AlessandroCrosby/GRUPO2/TALLERES/TALLERES SEMANA N°7/Link del video.pdf

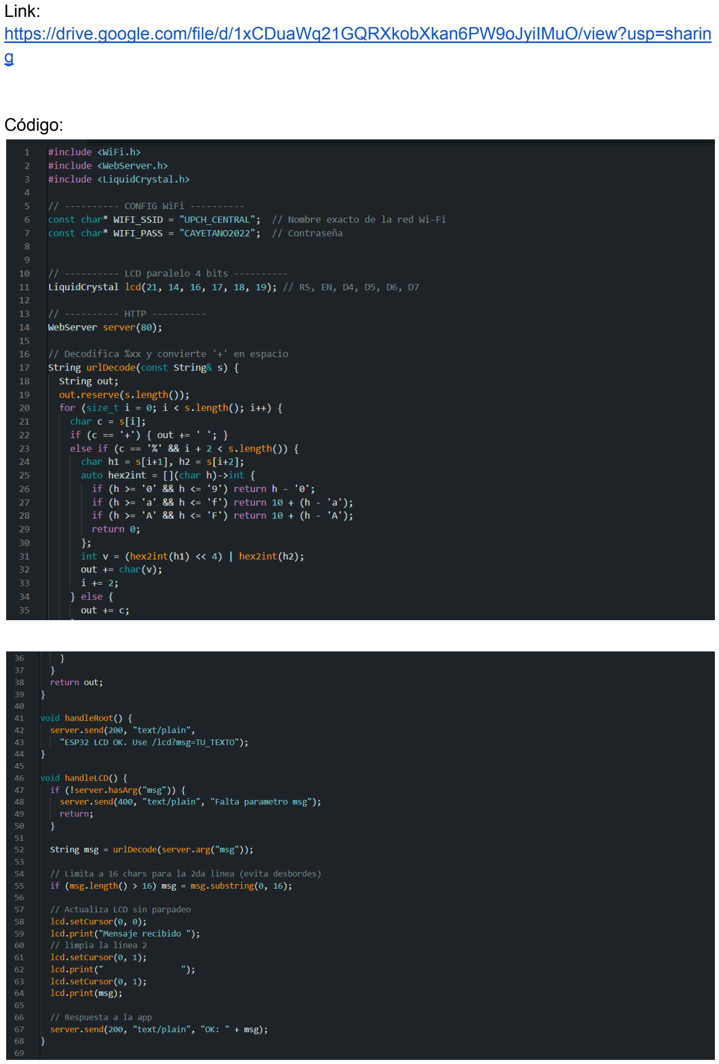
[picture p41: page 1]

Link:
https://drive.google.com/file/d/1xCDuaWq21GQRXkobXkan6PW9oJyiIMuO/view?usp=sharin g (https://drive.google.com/file/d/1xCDuaWq21GQRXkobXkan6PW9oJyiIMuO/view?usp=sharing)

Código:

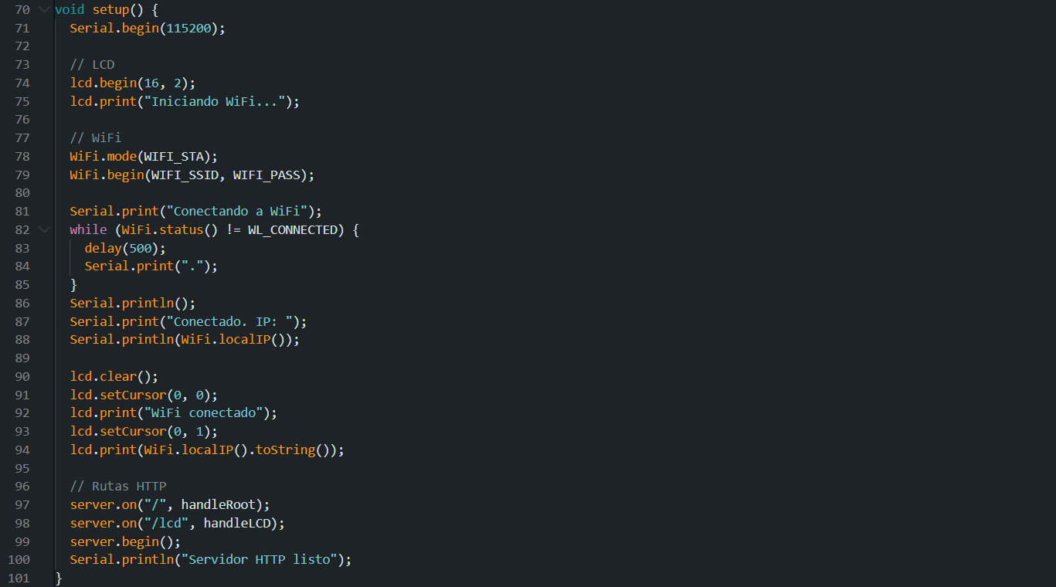
[picture p42: figure]

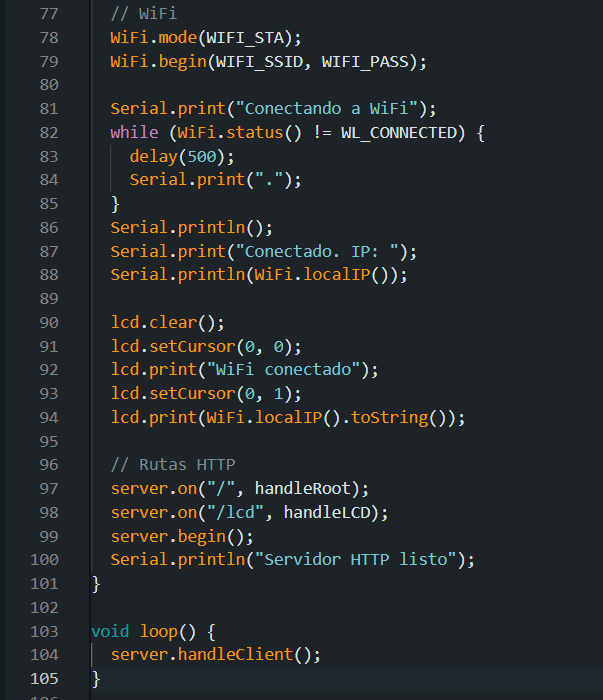
[picture p43: figure]

#include <WiFi.h>

#include <WebServer.h>

#include <LiquidCrystal.h>

// ---------- CONFIG WiFi ----------
const char* WIFI_SSID = "UPCH_CENTRAL"; // Nombre exacto de la red Wi-Fi const char* WIFI_PASS = "CAYETANO2022"; // Contraseña

// ---------- LCD paralelo 4 bits ----------
LiquidCrystal lcd(21, 14, 16, 17, 18, 19); // RS, EN, D4, D5, D6, D7

// ---------- HTTP ----------
WebServer server(80);

// Decodifica %xx y convierte '+' en espacio String urlDecode(const String& s) {
String out;
out.reserve(s.length());
for (size_t i = 0; i < s.length(); i++) { char c = s[i];
if (c == '+') { out += ' '; }
else if (c == '%' && i + 2 < s.length()) { char h1 = s[i+1], h2 = s[i+2];
auto hex2int = [](char h)->int {
if (h >= '0' && h <= '9') return h - '0';
if (h >= 'a' && h <= 'f') return 10 + (h - 'a'); if (h >= 'A' && h <= 'F') return 10 + (h - 'A'); return 0;
};
int v = (hex2int(h1) << 4) | hex2int(h2);
out += char(v);
i += 2;
} else {
out += c;
}
}
return out;
}

void handleRoot() {
server.send(200, "text/plain",
"ESP32 LCD OK. Use /lcd?msg=TU_TEXTO"); }

void handleLCD() {
if (!server.hasArg("msg")) {
server.send(400, "text/plain", "Falta parametro msg"); return;
}

String msg = urlDecode(server.arg("msg"));

// Limita a 16 chars para la 2da linea (evita desbordes) if (msg.length() > 16) msg = msg.substring(0, 16);

// Actualiza LCD sin parpadeo

lcd.setCursor(0, 0);
lcd.print("Mensaje recibido "); // limpia la linea 2
lcd.setCursor(0, 1);
lcd.print(" | ");
lcd.setCursor(0, 1);
lcd.print(msg);

// Respuesta a la app
server.send(200, "text/plain", "OK: " + msg); }

void setup() {
Serial.begin(115200);

// LCD
lcd.begin(16, 2);
lcd.print("Iniciando WiFi...");

// WiFi
WiFi.mode(WIFI_STA);
WiFi.begin(WIFI_SSID, WIFI_PASS);

Serial.print("Conectando a WiFi");
while (WiFi.status() != WL_CONNECTED) { delay(500);
Serial.print(".");
}
Serial.println();
Serial.print("Conectado. IP: "); Serial.println(WiFi.localIP());

lcd.clear();
lcd.setCursor(0, 0);
lcd.print("WiFi conectado"); lcd.setCursor(0, 1);
lcd.print(WiFi.localIP().toString());

// Rutas HTTP
server.on("/", handleRoot); server.on("/lcd", handleLCD); server.begin();
Serial.println("Servidor HTTP listo"); }

void loop() {
server.handleClient();
}
