AlessandroCrosby/GRUPO2/TALLERES/TALLERES SEMANA N°8/TALLER 8.pdf

## EJERCICIO 1:

## Captura del correo

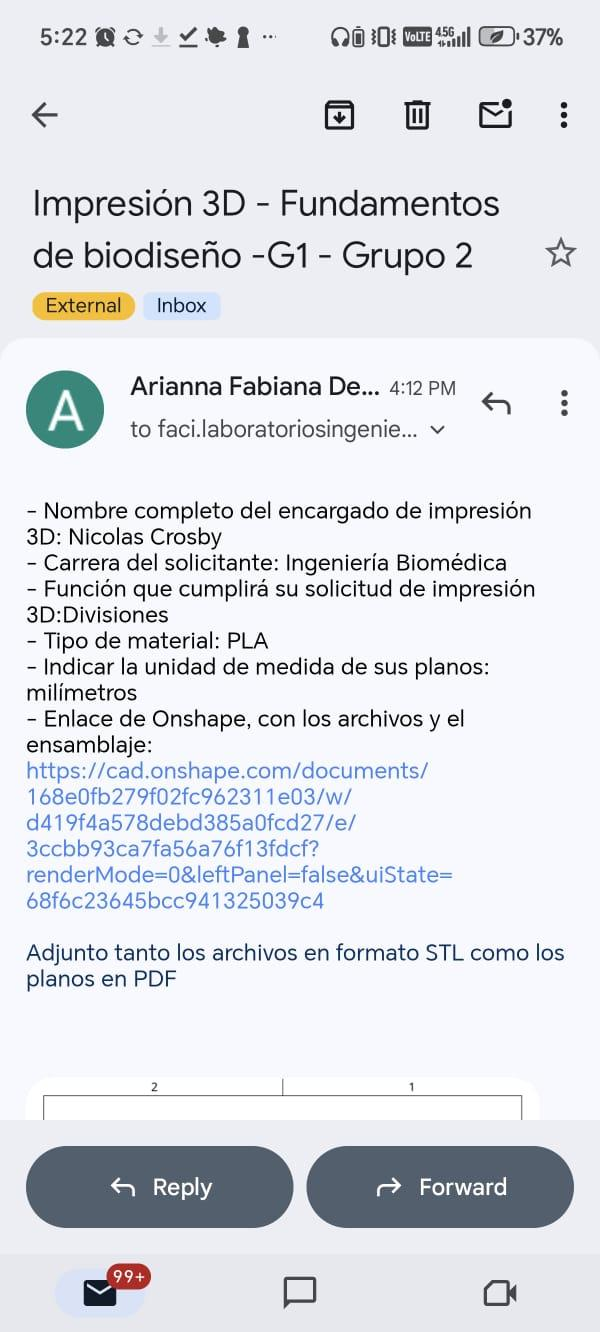
[picture p44: figure]
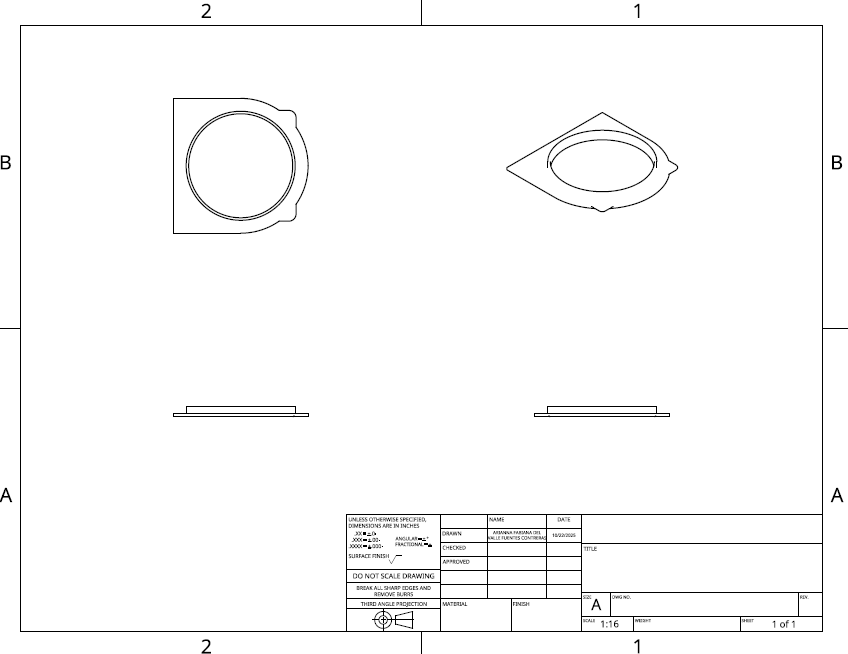
[picture p45: figure]
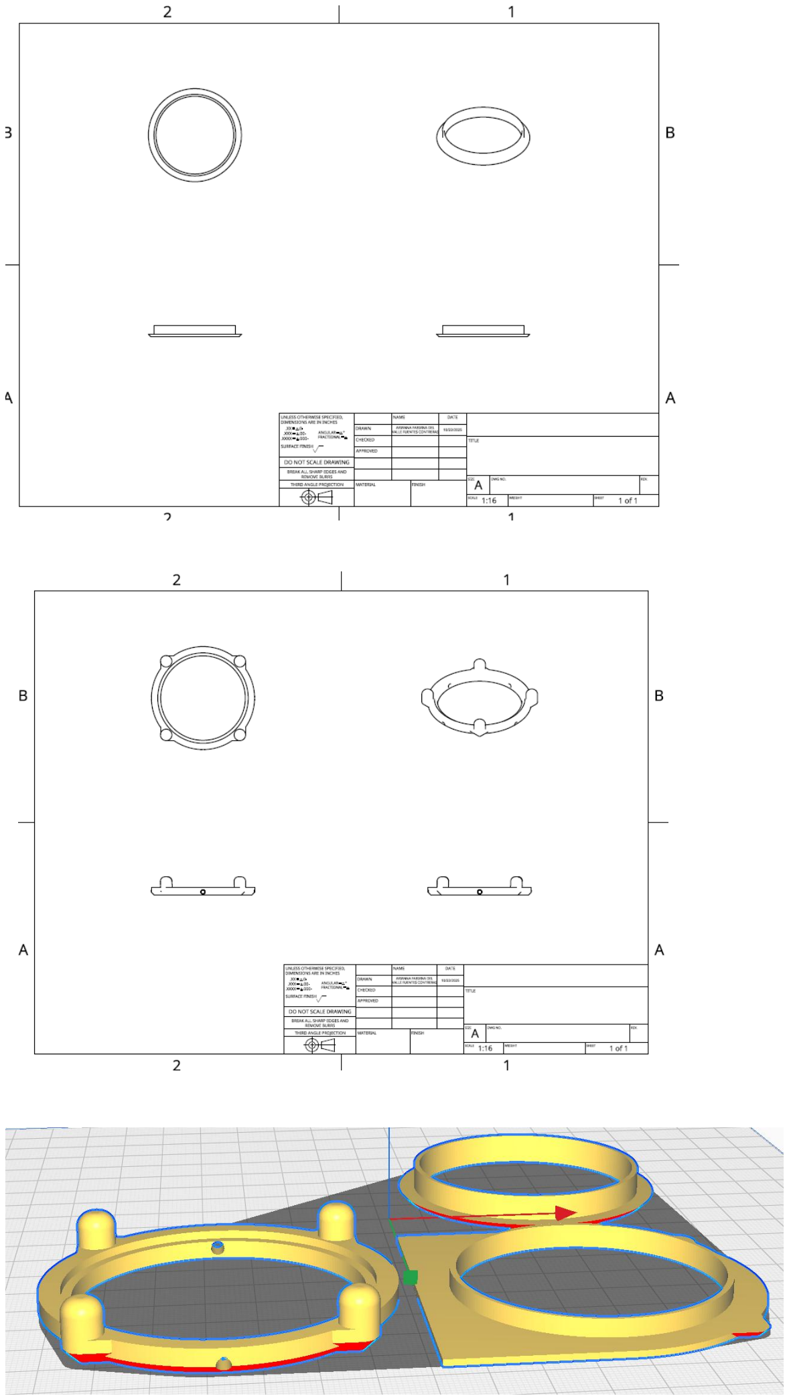
[picture p46: page 2]

## EJERCICIO 2:

## Plano 2.1

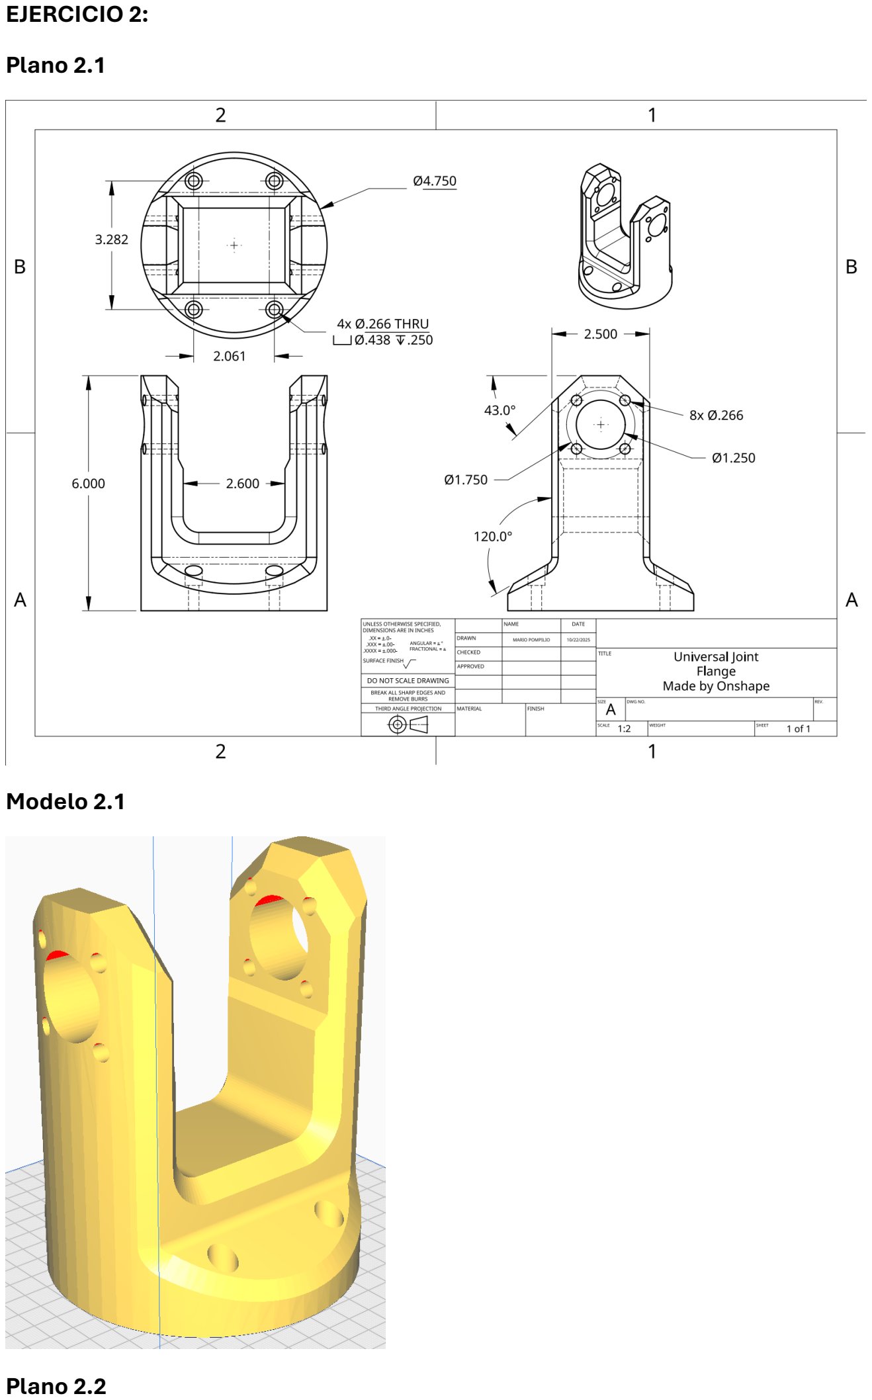
[picture p47: page 3]

## Modelo 2.1

## Plano 2.2

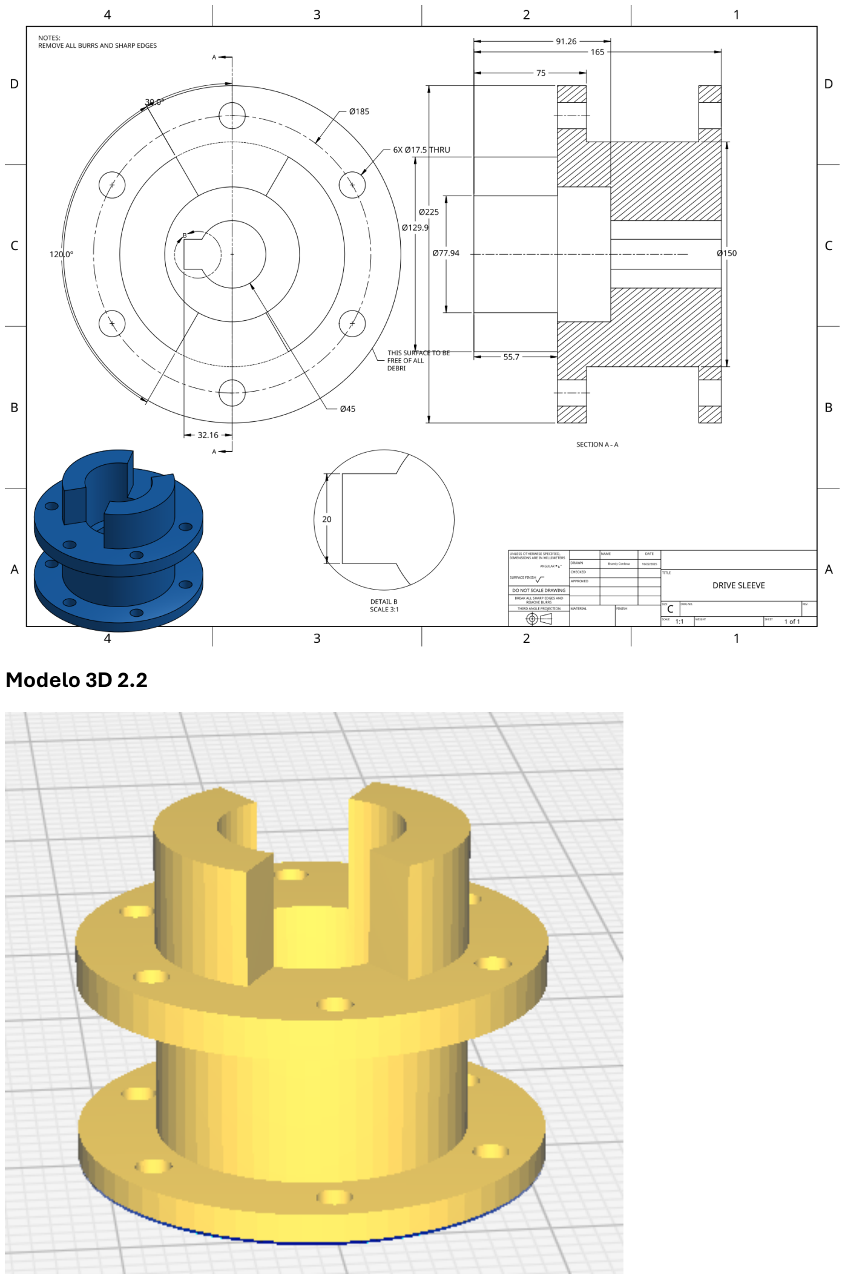
[picture p48: page 4]

## Modelo 3D 2.2

## EJERCICIO 3:

Parámetro Valor Bajo

Valor Medio
(Recomendado)
Valor Alto | Efecto Principal

Altura de
capa
0.12 mm | 0.2 mm | 0.28 mm

A menor altura: mejor calidad, pero más lento. A mayor altura: impresión más rápida, pero menos detallada.

Densidad de
relleno
10% | 20% | 30% o más

A menor relleno: piezas más ligeras y rápidas. A mayor relleno: piezas más fuertes, más pesadas y tardan más.

Velocidad de
impresión
30−40 mm/s | 40−60 mm/s | 80−100 mm/s (o más)

A menor velocidad: mejor
calidad. A mayor velocidad: más rápida pero puede fallar o perder.

## - Valor bajo - Tiempo de duración = 11 horas y 2 minutos:

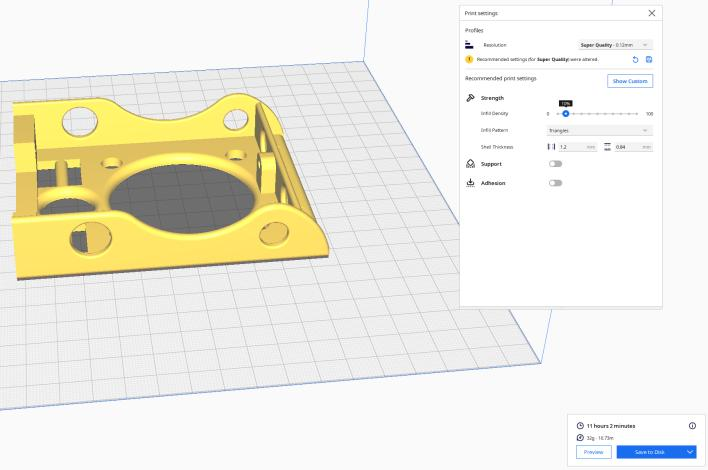
[picture p49: figure]

Figura 1: Valor bajo

## - Valor medio - Tiempo de duración = 5 horas y 1 minutos:

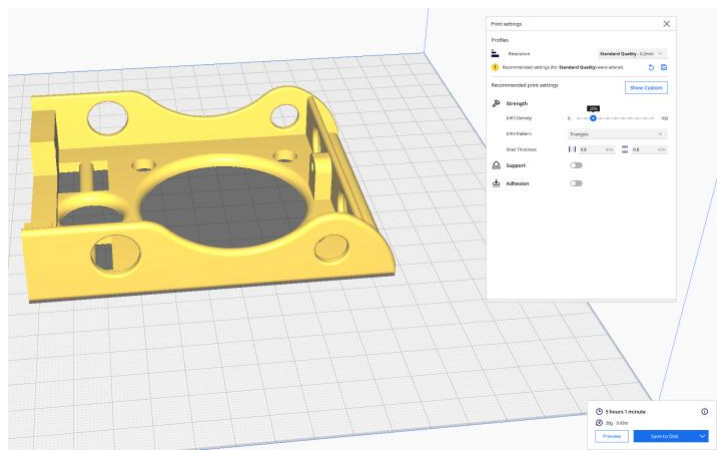
[picture p50: figure]

Figura 2: Valor medio

## - Valor alto - Tiempo de duración = 3 horas y 3 minutos:

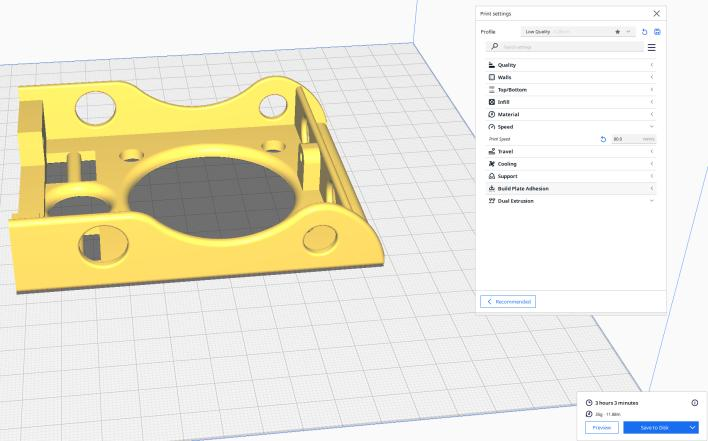
[picture p51: figure]

Figura 3: Valor Alto
