AlessandroCrosby/GRUPO2/TALLERES/TALLERES SEMANA N°7/PAOLA FERNANDEZ - CERTIFICADO (CORREGIDO).pdf

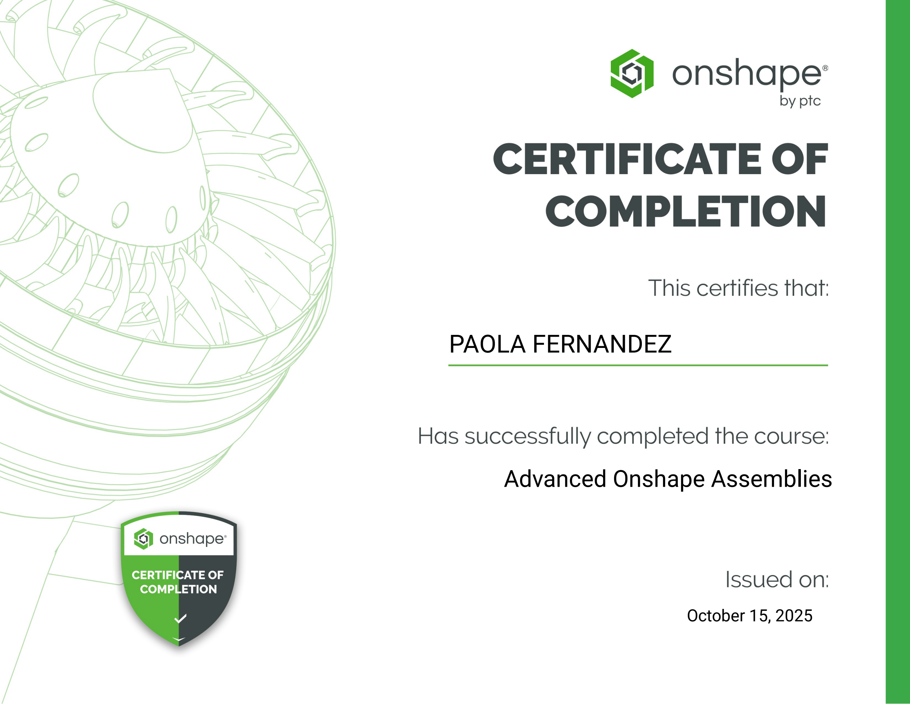
[picture p58: page 1]

PAOLA FERNANDEZ

Advanced Onshape Assemblies

October 15, 2025
