AlessandroCrosby/GRUPO2/TALLERES/TALLERES SEMANA N°7/BRANDY CORDOVA - CERTIFICADO..pdf

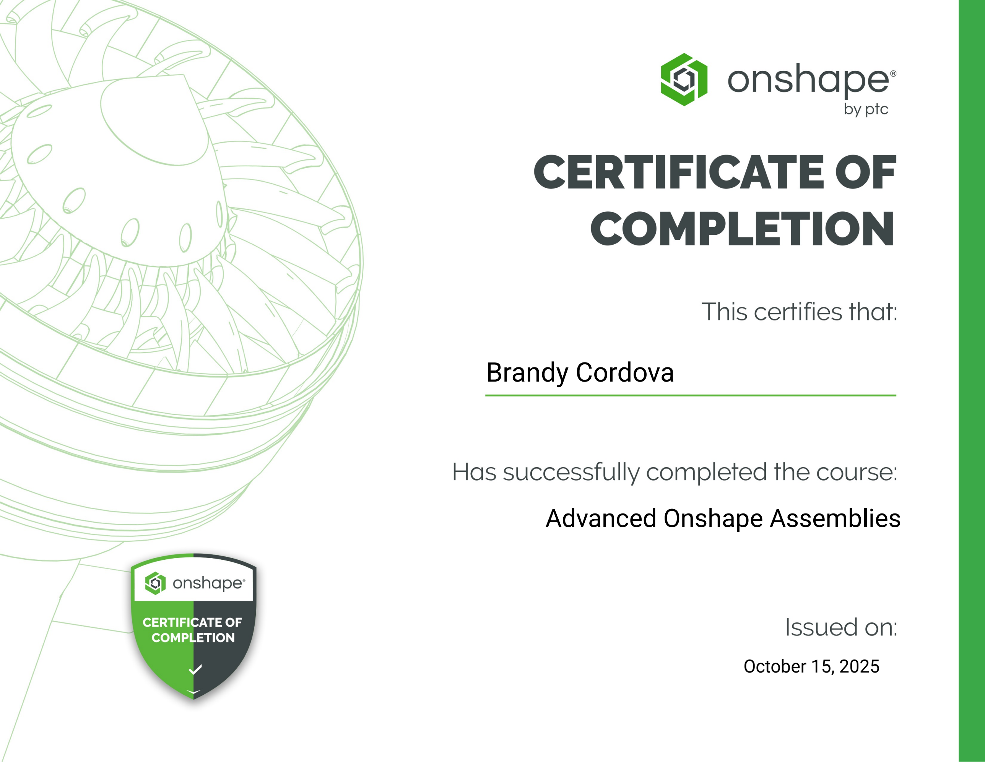
[picture p59: page 1]

Brandy Cordova

Advanced Onshape Assemblies

October 15, 2025
