AlessandroCrosby/GRUPO2/TALLERES/TALLERES SEMANA N°7/CERTIFICADO - SEBASTIAN ESPINOZA.pdf

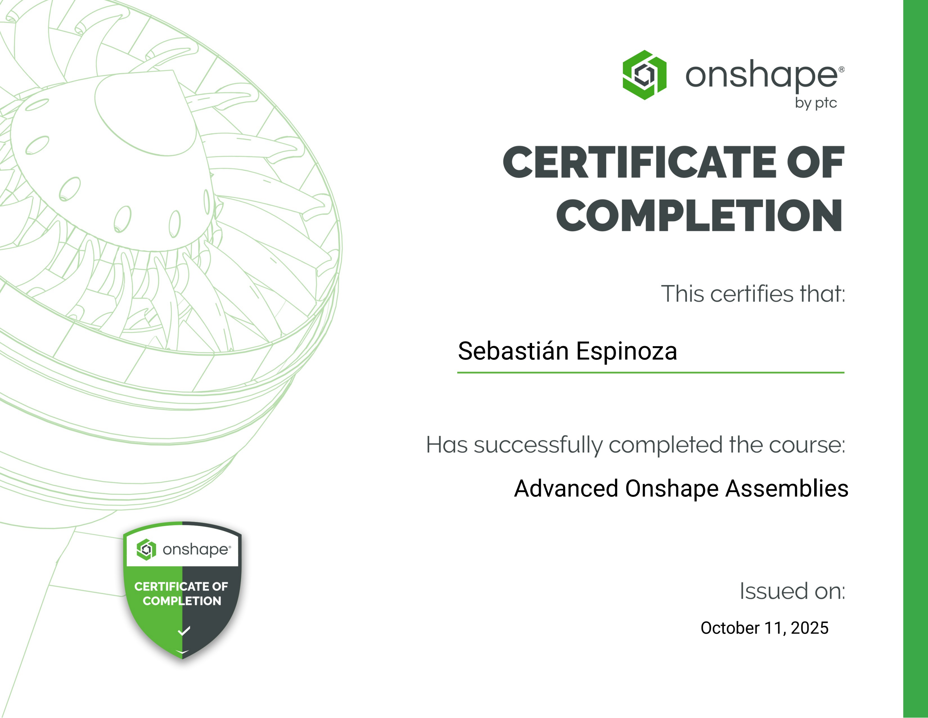
[picture p70: page 1]

Sebastián Espinoza

Advanced Onshape Assemblies

October 11, 2025
