AlessandroCrosby/GRUPO2/TALLERES/TALLERES SEMANA N°7/ARIANNA FUENTES - CERTIFICADO.pdf

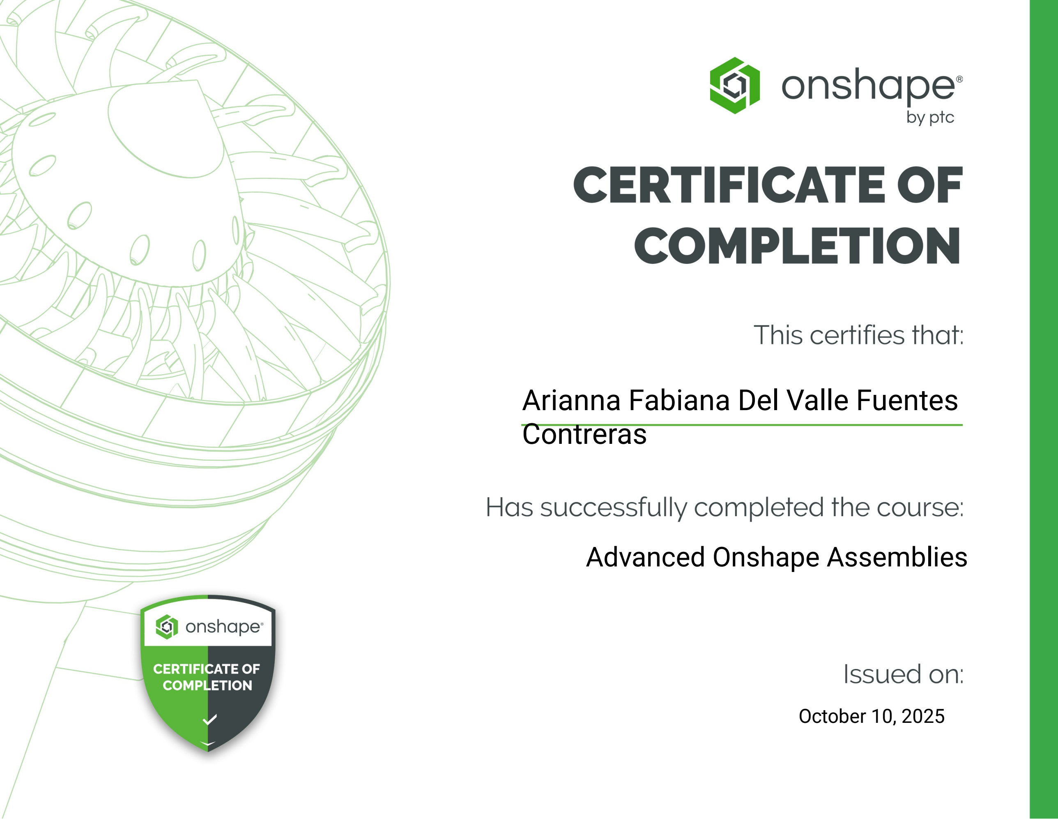
[picture p71: page 1]

Arianna Fabiana Del Valle Fuentes Contreras

Advanced Onshape Assemblies

October 10, 2025
