AlessandroCrosby/GRUPO2/TALLERES/TALLERES SEMANA N°7/MARIO POMPILIO - CERTIFICADO.pdf

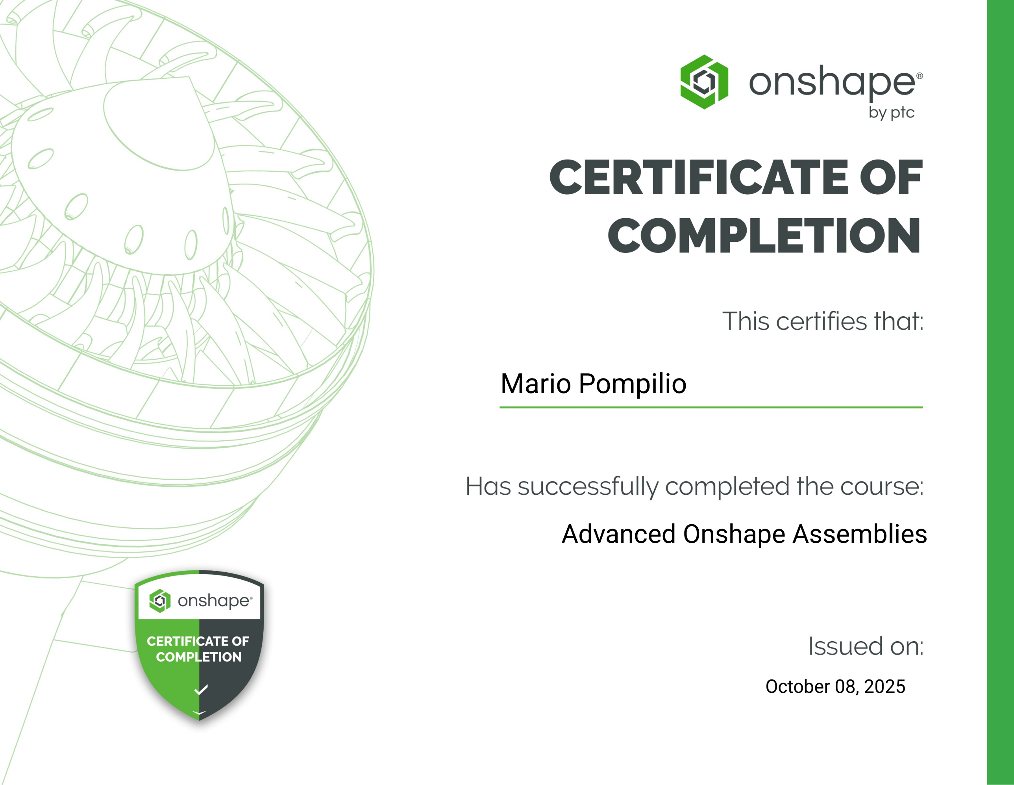
[picture p72: page 1]

Mario Pompilio

Advanced Onshape Assemblies

October 08, 2025
