AlessandroCrosby/GRUPO2/TALLERES/TALLERES SEMANA N°7/ALESSANDRO CROSBY - CERTIFICADO.pdf

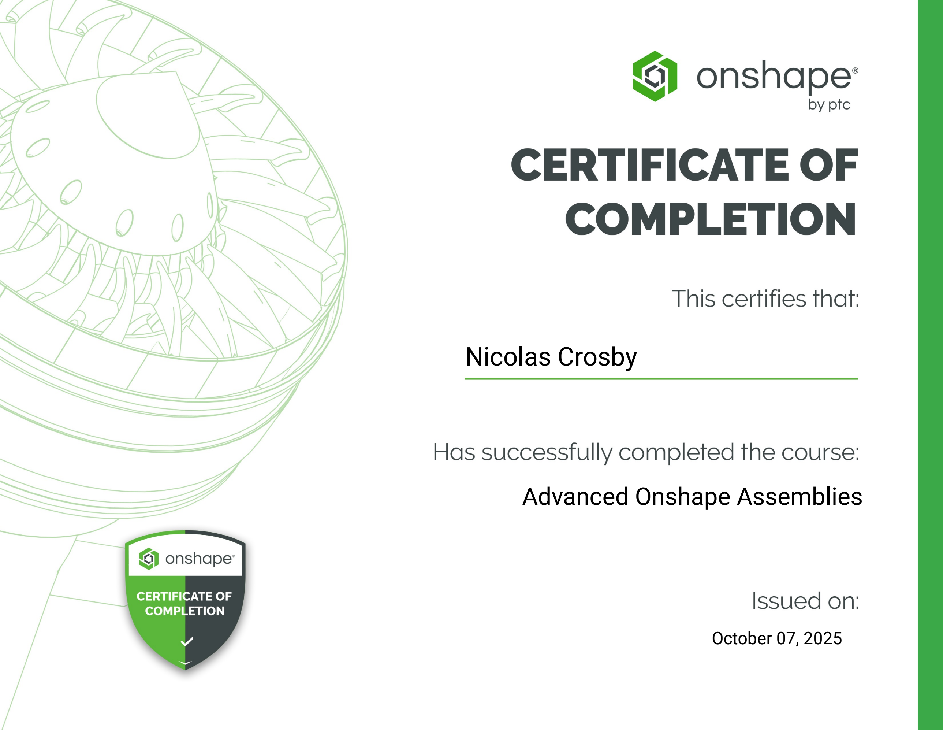
[picture p73: page 1]

Nicolas Crosby

Advanced Onshape Assemblies

October 07, 2025
