AlessandroCrosby/GRUPO2/TALLERES/TALLERES SEMANA N°6/Talleres Semana N°6.pdf

Control de velocidad y sentido "seguro de un actuador con potenciómetro y pulsador:
Código:

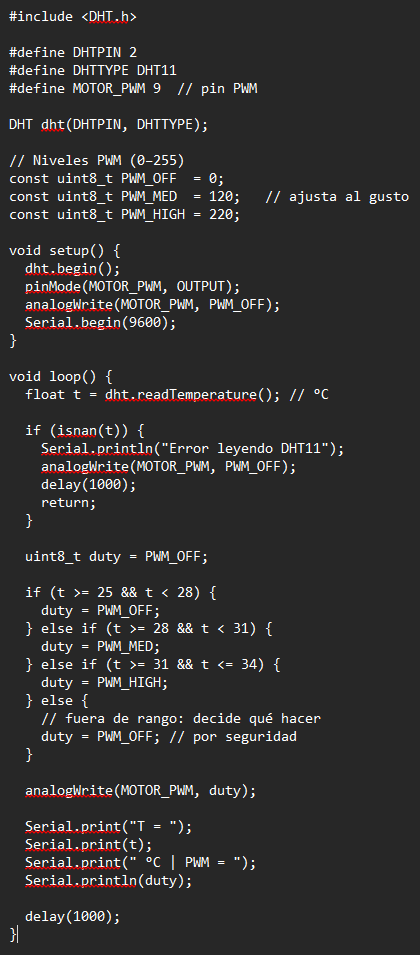
[picture p74: figure]

Vídeo:
https://youtu.be/nqgcbofGsaQ

Control angular de 0 a 270 grados con sensor flex y alerta por máximo: Código:

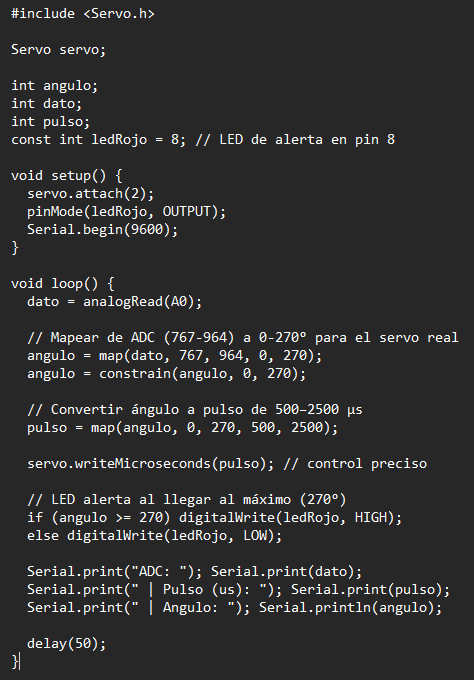
[picture p75: figure]

Vídeo:
https://youtube.com/shorts/ELOo07f0l_c

"Haptic Comfort" Alerta háptica de confort térmico: Código:

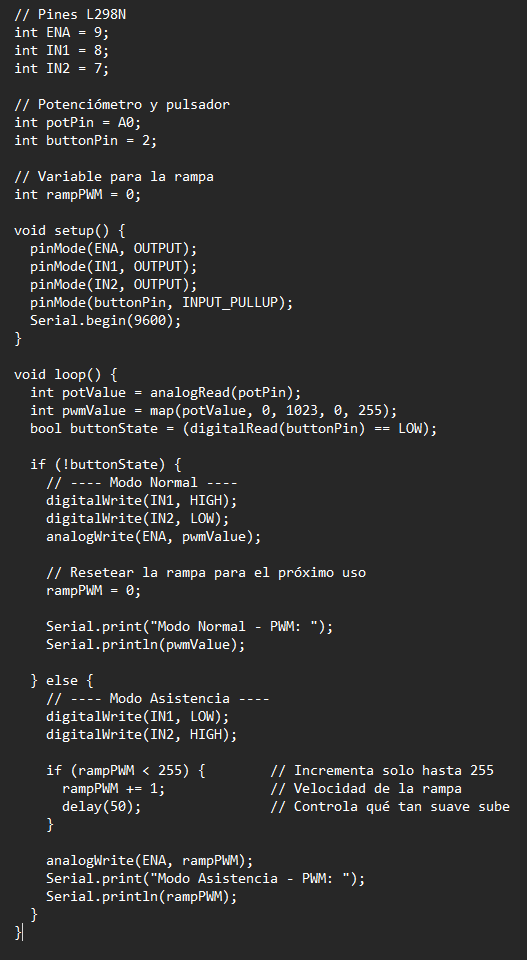
[picture p76: figure]

Vídeo:
https://youtube.com/shorts/SWmqY8hiBsc
