AlessandroCrosby/GRUPO2/TALLERES/TALLERES SEMANA N°7/PAOLA FERNANDEZ - CERTIFICADO.pdf

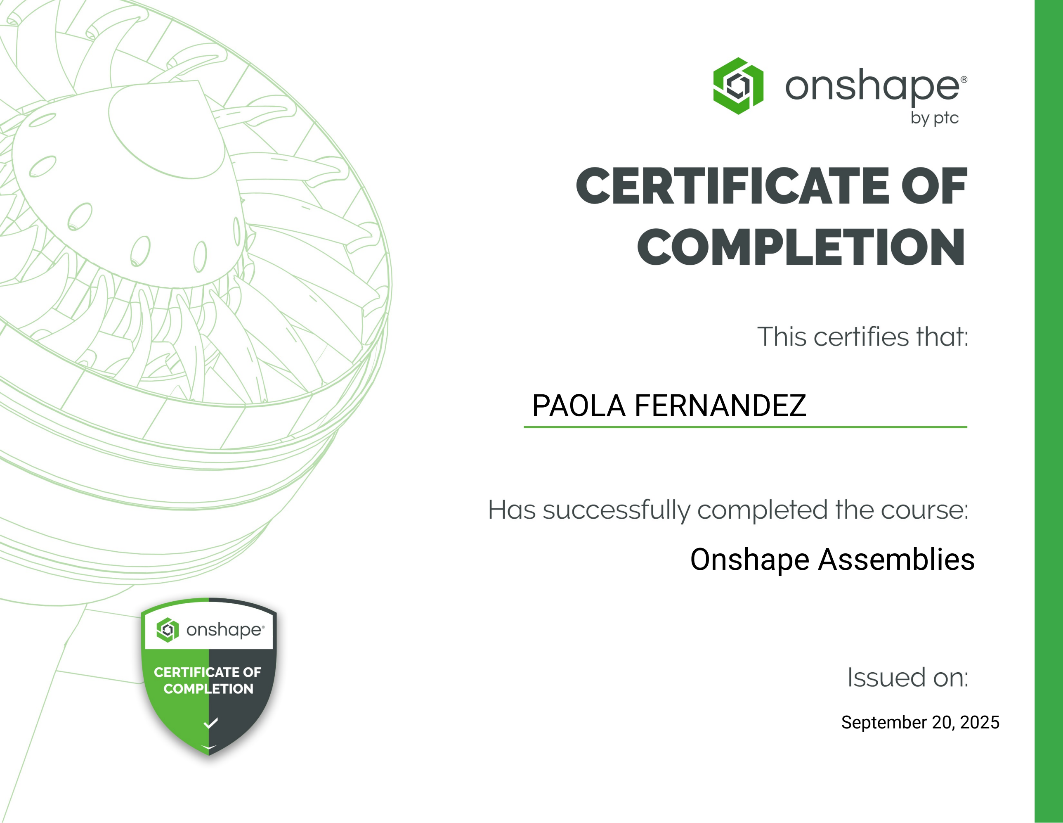
[picture p77: page 1]

PAOLA FERNANDEZ

September 20, 2025

Onshape Assemblies
