AlessandroCrosby/GRUPO2/TALLERES/TALLERES SEMANA N°4/LINK DE VIDEOS DE LOS TRABAJOS CON SENSORES.pdf

LINK DE VIDEOS DE LOS TRABAJOS CON SENSORES: https://drive.google.com/drive/folders/1y1I-DP5qafuJuMX3bPiQ4m6cW_Xysbt?usp=sharing (https://drive.google.com/drive/folders/1y1I-DP5qafuJuMX3bPiQ4m6cW_Xy-sbt?usp=sharing)
