AlessandroCrosby/GRUPO2/TALLERES/TALLERES SEMANA N°3/SISTEMA DE DETECCIÓN DE PROXIMIDAD CON LEDS.pdf

SISTEMA DE DETECCIÓN DE PROXIMIDAD CON LEDS

- CÓDIGO:

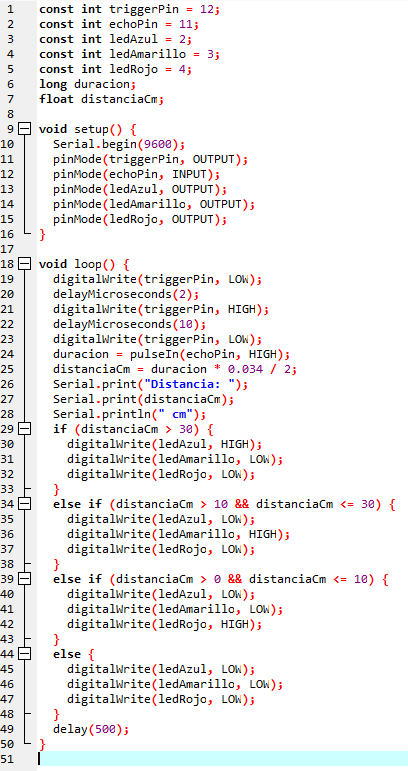
[picture p78: figure]

}

- FOTOS:

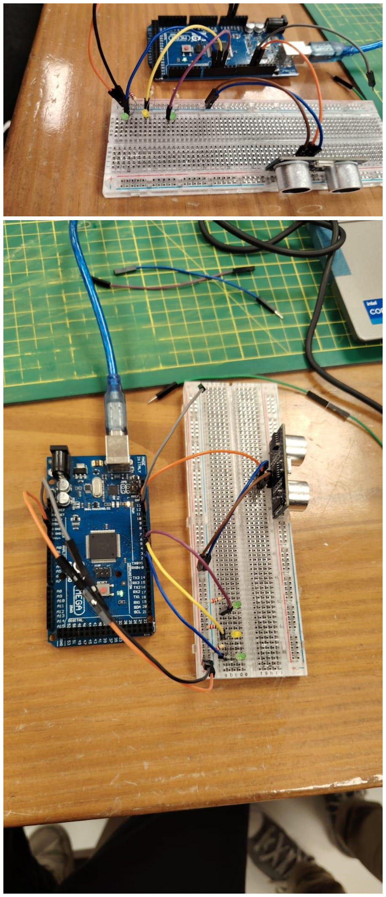
[picture p79: figure]

- VÍDEO:
https://youtube.com/shorts/fzW8f1nStyw
