AlessandroCrosby/GRUPO2/TALLERES/TALLERES SEMANA N°3/SISTEMA DE NAVEGACIÓN LCD CON JOYSTICK.pdf

SISTEMA DE NAVEGACIÓN LCD CON JOYSTICK

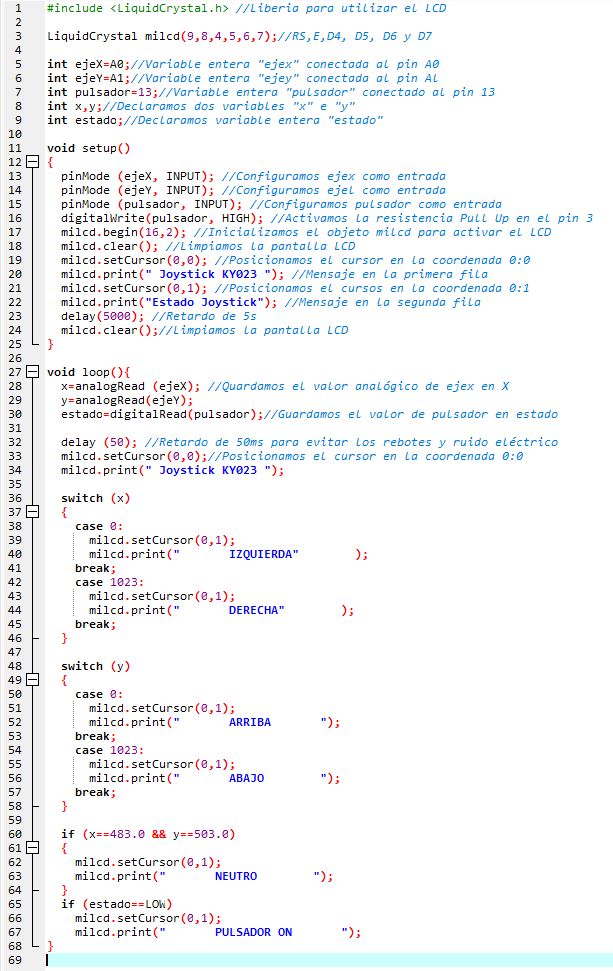
[picture p80: figure]

- CÓDIGO:

- FOTO:

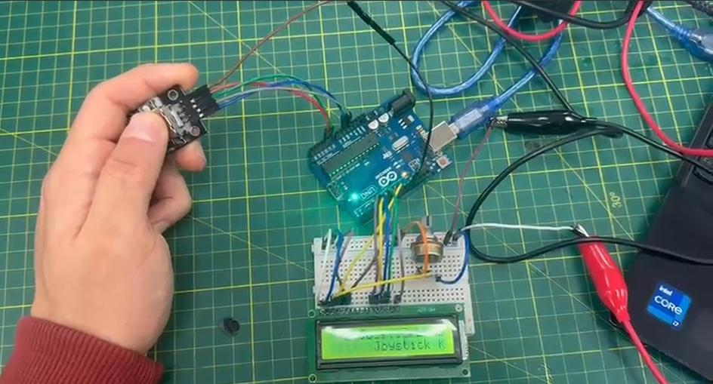
[picture p81: figure]

- VIDEO:
https://youtu.be/YSJlPFgi8W8

Nota: Al parecer en nuestro circuito había un falso negativo con uno de los cables el cual no dejaba q se aprecie en todo momento los movimientos del joystick, no nos quedaba mucho tiempo y no pudimos solucionarlo correctamente. Aún así sí funcionaba el código.
