AlessandroCrosby/GRUPO2/TALLERES/TALLERES SEMANA N°3/SISTEMA DE ALARMA POR TEMPERATURA.pdf

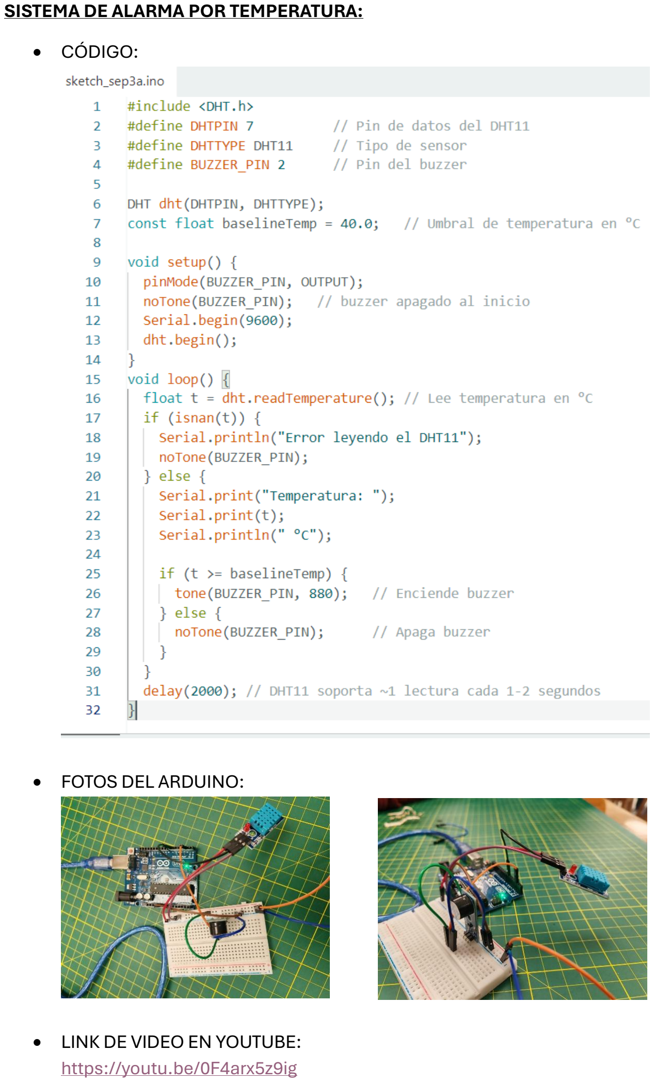
[picture p82: page 1]

SISTEMA DE ALARMA POR TEMPERATURA:

- CÓDIGO:
- FOTOS DEL ARDUINO:
- LINK DE VIDEO EN YOUTUBE: https://youtu.be/0F4arx5z9ig
