AlessandroCrosby/GRUPO2/TALLERES/TALLERES SEMANA N°2/T3 - Entregable 2.pdf

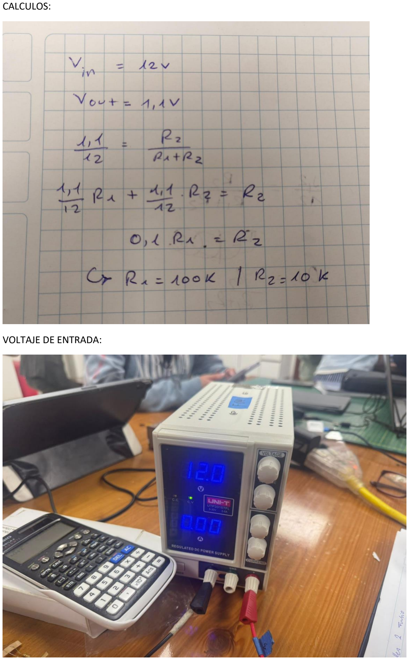
[picture p83: page 1]

CALCULOS:

VOLTAJE DE ENTRADA:

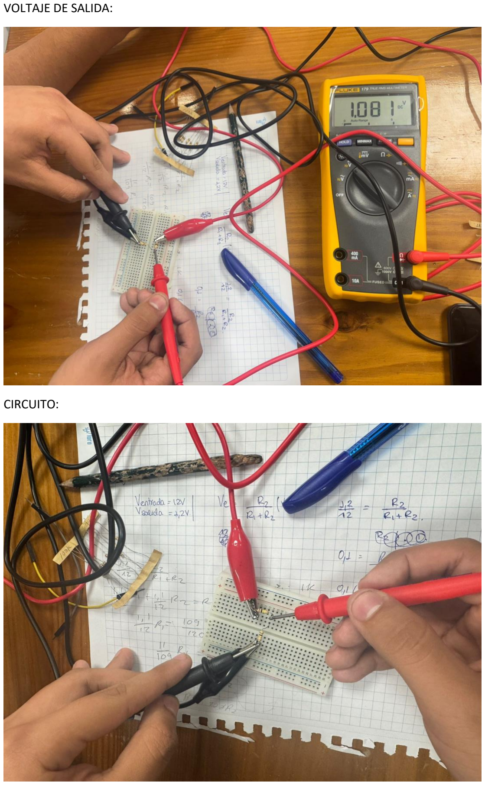
[picture p84: page 2]

VOLTAJE DE SALIDA:

CIRCUITO:
