AlessandroCrosby/GRUPO2/TALLERES/TALLERES SEMANA N°5/Condori Pompilio, Pabel Mario/mario-pompilio-fed711da-1624-4ce5-843c-b44c58120fdf-certificate.pdf

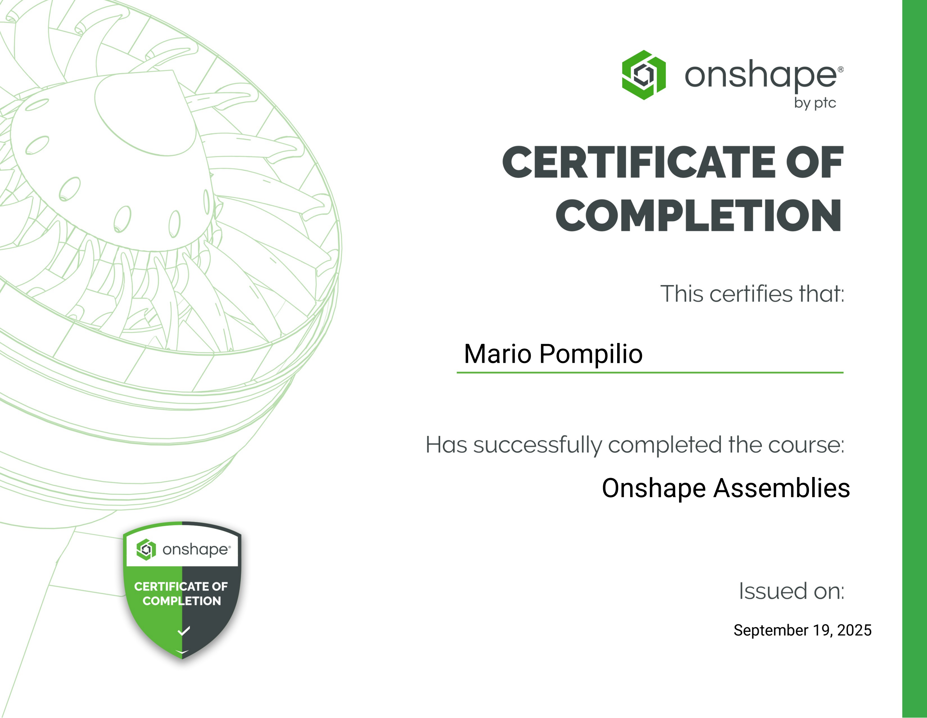
[picture p85: page 1]

Mario Pompilio

September 19, 2025

Onshape Assemblies
