AlessandroCrosby/GRUPO2/TALLERES/TALLERES SEMANA N°5/Espinoza Padilla, Sebastian Amadeus/CERTIFICADO 5 - SEBASTIÁN ESPINOZA.pdf

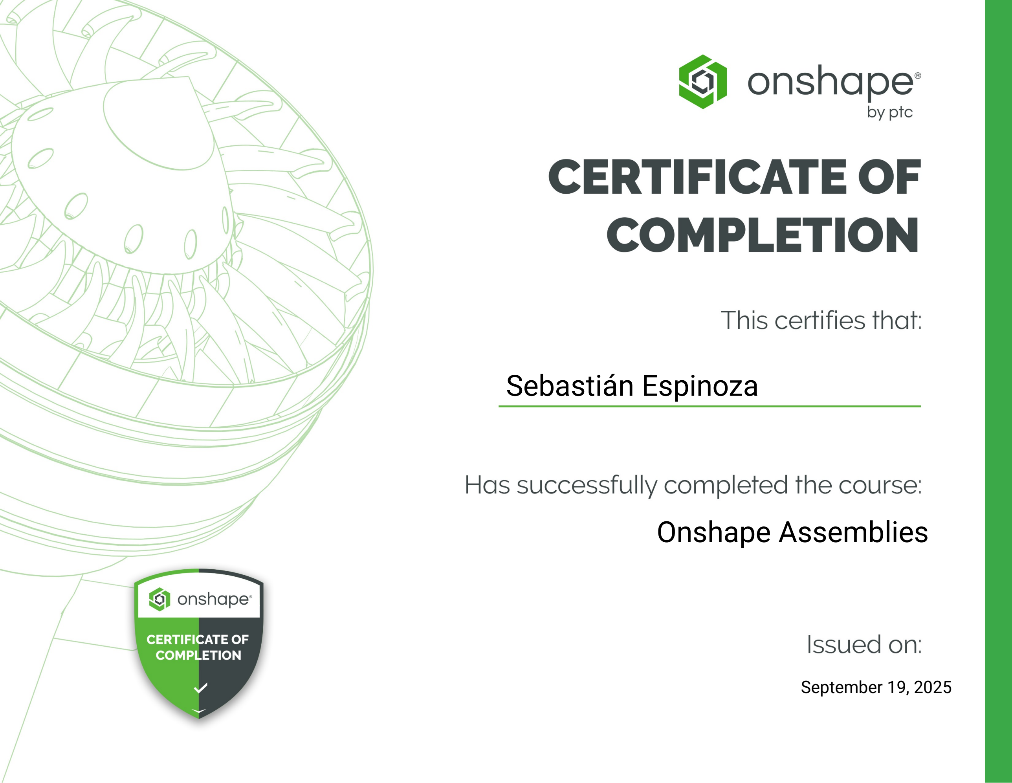
[picture p86: page 1]

Sebastián Espinoza

September 19, 2025

Onshape Assemblies
