AlessandroCrosby/GRUPO2/TALLERES/TALLERES SEMANA N°5/Crosby Collantes, Alessandro Nicolas/CERTIFICADO 4 - NICOLAS CROSBY.pdf

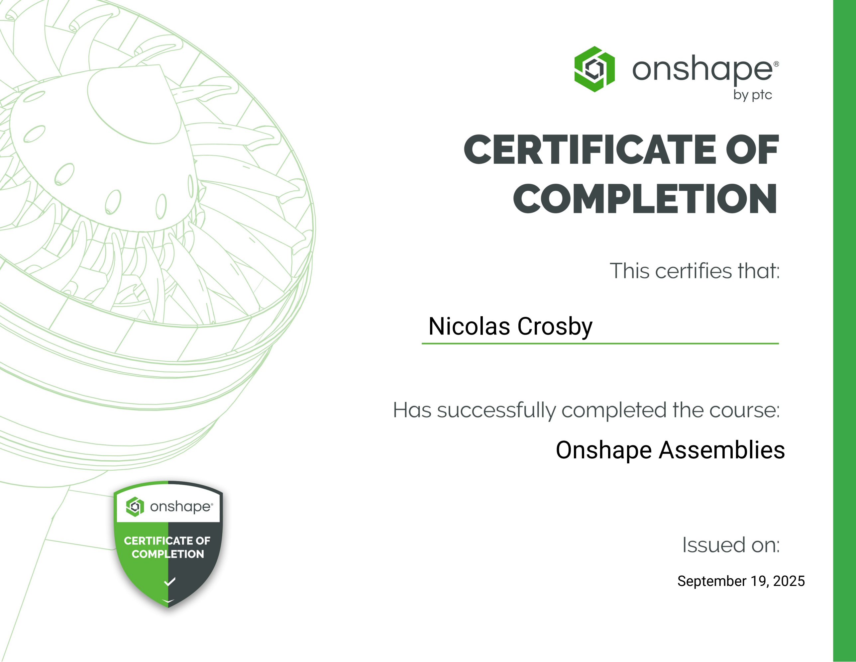
[picture p87: page 1]

Nicolas Crosby

September 19, 2025

Onshape Assemblies
