AlessandroCrosby/GRUPO2/ENTREGABLES/ENTREGABLES SEMANA N°9/ENTREGABLE N°9.pdf

Entregable N°9:

MODELADO 3D/AVANCE PROTOTIPADO ELECTRÓNICO.Plan de usabilidad basado en evidencias.

Autores:

Alessandro Nicolas Crosby Collantes

Pabel Mario Condori Pompilio

Arianna Fabiana Del Valle Fuentes Contreras

Paola Andrea Fernández García

Brandy Abigail Cordova Palomino

Sebastián Amadeus Espinoza Padilla

Asesores:

Miguel Rogger Hoyos Alvitez

Marco Mugaburu Celi

Shirley Pahuachon Nuñez

Curso:

Fundamentos de Biodiseño – Ciclo IV

Universidad Peruana Cayetano Heredia

Facultad de Ciencias e Ingeniería

Octubre 2025

### 1. Esquema de conexión corregido

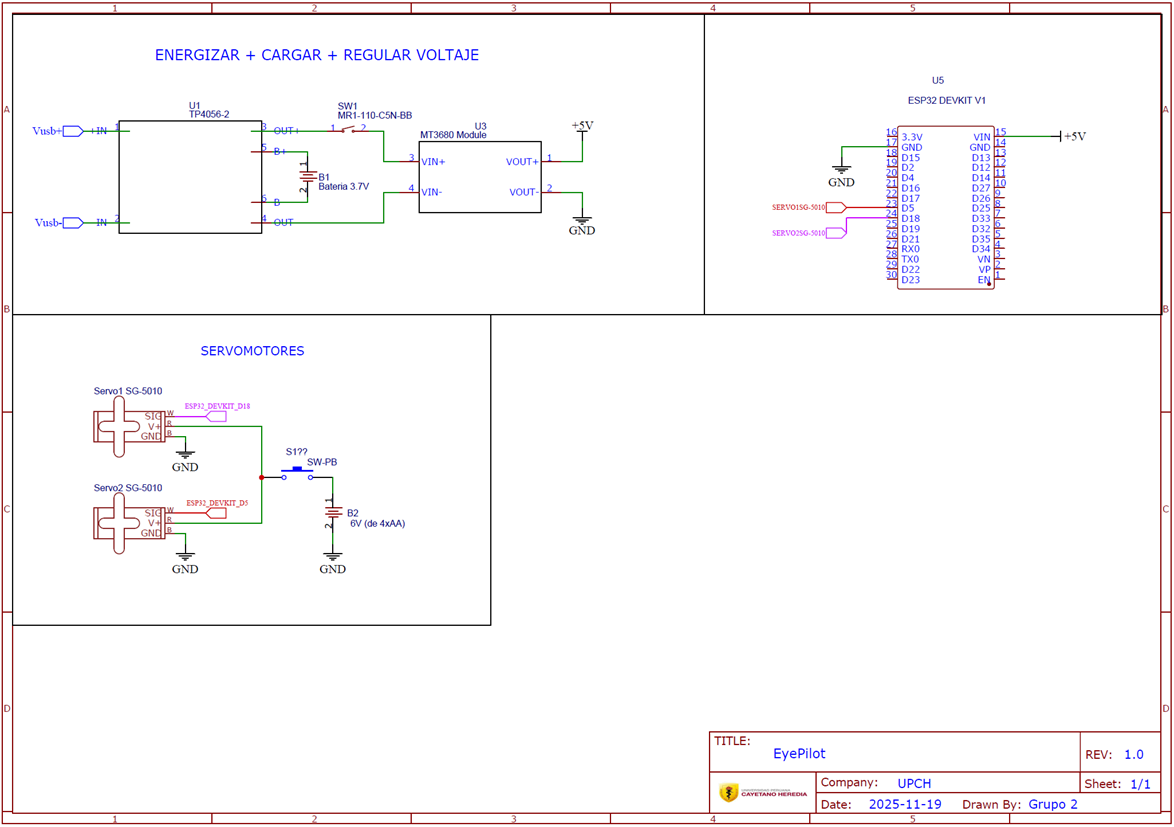
[picture p125: figure]

### 2. Código del prototipo

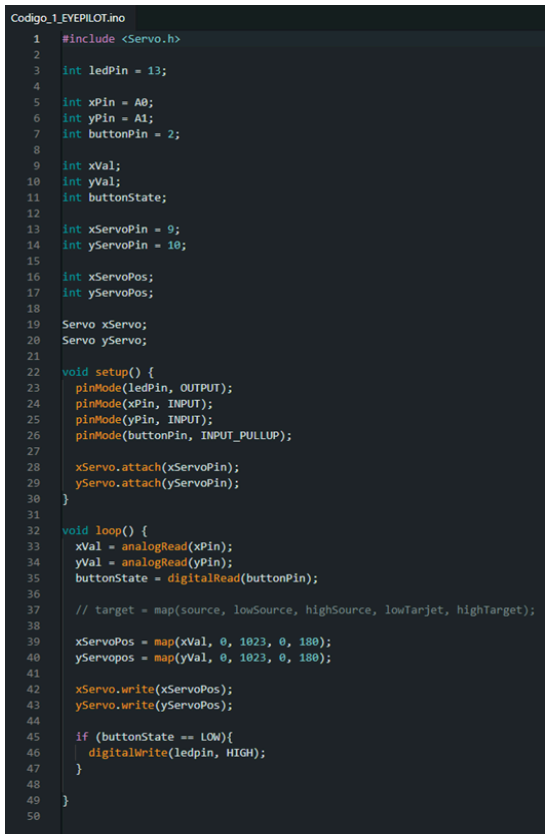
[picture p126: figure]

### 3. Imágen del prototipado


Vídeo del funcionamiento: https://youtube.com/shorts/OhZxIiCbmYA

### 4. Modelado de prototipo final


5. MODELO 3D DE LOS COMPONENTES POR SEPARADO (En el link está el archivo STL y sus planos respectivos)

Partes de la mano electrónica


https://cad.onshape.com/documents/927f9d930a183de838edcac2/w/3bcfa64efb8507dd82d95b43/e/a9c65f4d9c443f50373546c3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 6f3615368f (https://cad.onshape.com/documents/927f9d930a183de838edcac2/w/3bcfa64efb8507dd82d95b43/e/a9c65f4d9c443f50373546c3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)

Caja Maestra

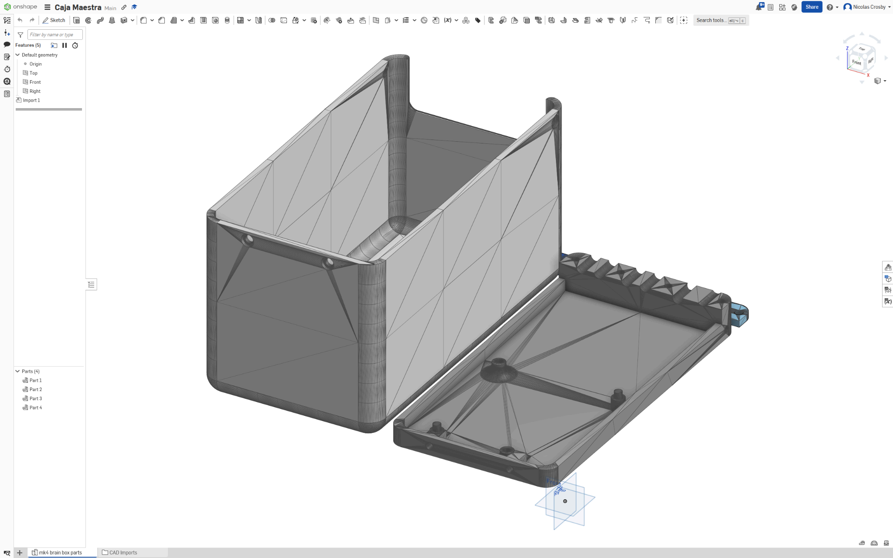
[picture p127: figure]

https://cad.onshape.com/documents/92b52b4e0c300ed93bdf525a/w/cddcb3f246b215be201326a7/e/bde1416c9744771a4ff36ce2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 1588afa5c2 (https://cad.onshape.com/documents/92b52b4e0c300ed93bdf525a/w/cddcb3f246b215be201326a7/e/bde1416c9744771a4ff36ce2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)

Placa localizadora

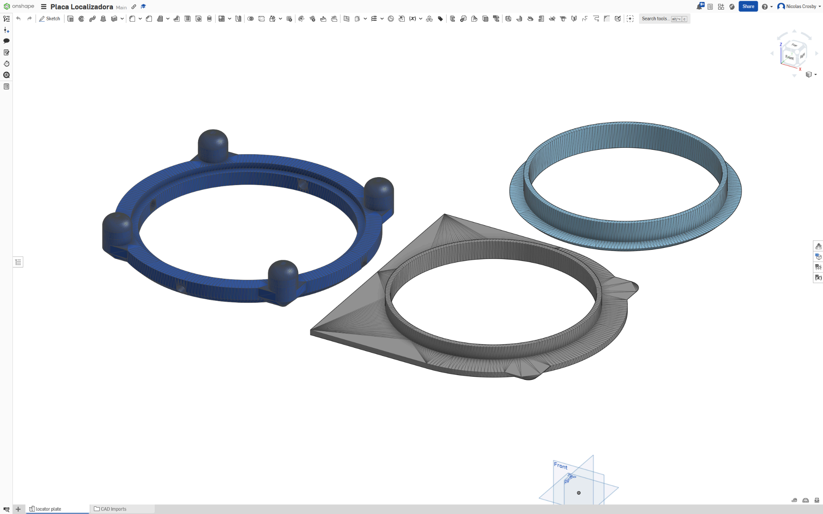
[picture p128: figure]

https://cad.onshape.com/documents/168e0fb279f02fc962311e03/w/d419f4a578debd385a0fcd27/e/3ccbb93ca7fa56a76f13fdcf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 f6c23645bcc941325039c4 (https://cad.onshape.com/documents/168e0fb279f02fc962311e03/w/d419f4a578debd385a0fcd27/e/3ccbb93ca7fa56a76f13fdcf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)

Widgets de nivelación de la placa

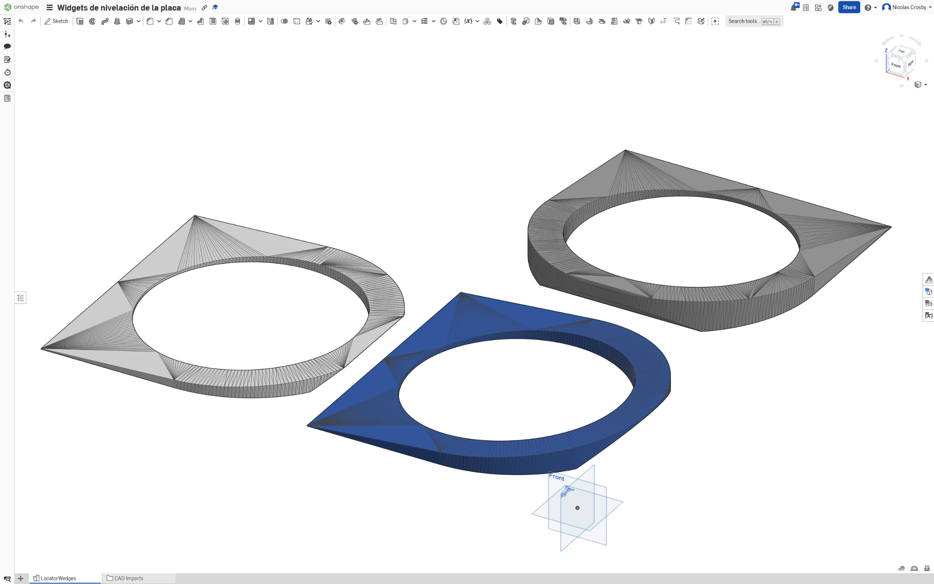
[picture p129: figure]

https://cad.onshape.com/documents/f1b766af54a61c95dd358874/w/bbb4037a9761144664293a34/e/a7c4b9bcc94228c8a9a27d8e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 (https://cad.onshape.com/documents/f1b766af54a61c95dd358874/w/bbb4037a9761144664293a34/e/a7c4b9bcc94228c8a9a27d8e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)

Fundas para el joystick de la silla

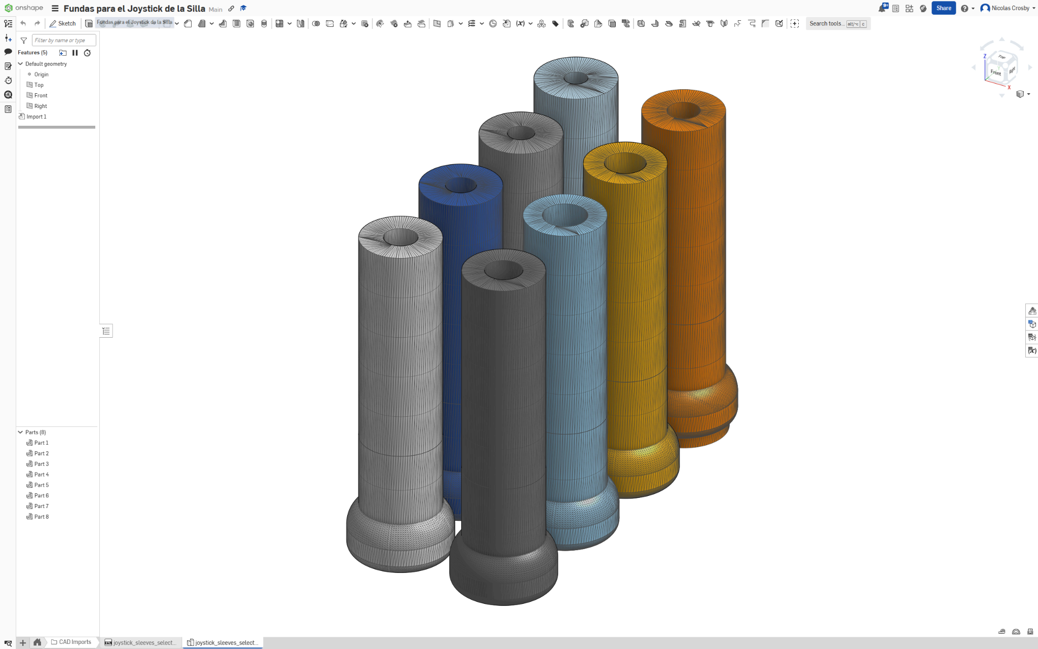
[picture p130: figure]

https://cad.onshape.com/documents/d7fdf115b7fa3b05aaad5f9b/w/b24232bda438e4b2c956bb41/e/189860676e1bd6b74a4bc799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 b0087a392d (https://cad.onshape.com/documents/d7fdf115b7fa3b05aaad5f9b/w/b24232bda438e4b2c956bb41/e/189860676e1bd6b74a4bc799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)

Base de la mano electrónica

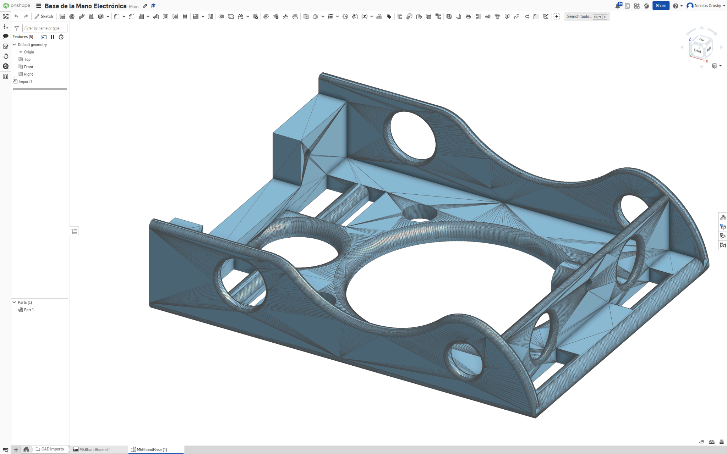
[picture p131: figure]

https://cad.onshape.com/documents/afd46ea642bc3d8c53162def/w/6fc6773dec8da8fe8db94871/e/7183207c0e2449b9e7caf463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 80c481086 (https://cad.onshape.com/documents/afd46ea642bc3d8c53162def/w/6fc6773dec8da8fe8db94871/e/7183207c0e2449b9e7caf463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)

TABLA 1: Plan de usabilidad basado en la evidencia

Sección del plan | ¿Qué es? | ¿Qué hacer? | ¿Qué evidencia deben incluir?


1. Contexto
de uso | El prototipo será utilizado por personas que padecen de esclerosis múltiple avanzada las cuales presentan discapacidad motriz severa, pero mantienen el control ocular y cognitivo suficiente para manejar el dispositivo. Este consiste en controlar una silla de ruedas eléctrica mediante movimientos oculares detectados por una app Android con eye-tracking, que envía comandos vía Bluetooth al ESP32, el cual acciona dos servomotores que mueven el joystick.
| Por otro lado, en cuanto su uso se realizará en entornos exteriores controlados y clínicas de rehabilitación, bajo supervisión inicial de un terapeuta. El sistema busca mejorar la autonomía y seguridad del usuario, integrando sensores ultrasónicos y botón de parada de emergencia para prevenir accidentes.

El prototipo está diseñado principalmente para pacientes con esclerosis múltiple avanzada, quienes presentan discapacidad motriz severa, pero conservan control ocular y cognitivo. Asimismo, el terapeuta o cuidador actúa como usuario secundario, puesto que este debe encargarse de configurar y supervisar el funcionamiento del sistema en todo momento, garantizando la correcta interacción del paciente con la silla de ruedas.

Por otro lado, el uso del prototipo debe realizarse en entornos controlados, como hospitales, clínicas de rehabilitación y zonas exteriores seguras, donde las condiciones físicas y técnicas permiten un manejo confiable del equipo. Sin embargo, no se recomienda su uso en exteriores con múltiples factores externos (automóviles o lugares concurridos), ya que se requieren programas y sensores adicionales que aseguren la seguridad e integridad del paciente frente a obstáculos o interferencias múltiples [1].

En cuanto a la frecuencia de uso, esta depende del estado físico del paciente y del plan de rehabilitación propuesto, entonces las sesiones diarias podrían ser progresivas 10, 20, 30 a 60 minutos, lo que permite que el usuario practique y mejore su autonomía de manera progresiva, mientras se garantiza su seguridad mediante sensores y un botón de parada de emergencia.

2. Perfil del
usuario

El perfil del usuario describe las características físicas, cognitivas y emocionales de la persona que utilizará el dispositivo, en este caso, un hombre de 52 años con diagnóstico de Esclerosis Múltiple Avanzada y disartria severa.

Características físicas:

- Debilidad muscular generalizada (3/5 en escala de fuerza muscular).
- Fatiga fácil con esfuerzo físico moderado.
- Control parcial de micción e intestino.
- Apetito conservado.
- Emisión verbal ininteligible, con habla limitada.

Características cognitivas:

- Estado de conciencia lúcido.
- Comprensión de órdenes simples y complejas conservadas.
- Capacidad de responder mediante gestos o medios no verbales.
- Dificultad para la comunicación oral, pero conserva la comprensión.

Características emocionales:

- Ánimo bajo, posiblemente relacionado con la limitación funcional y la dependencia.
- Necesidad de mantener participación

Analizar si el usuario tiene limitaciones visuales, motoras, cognitivas o de comprensión mediante:

Evaluación de limitaciones motoras: Verificar capacidad de movimiento, fuerza muscular y coordinación para manipular dispositivos. En el caso del usuario con EM avanzada, se evidencia debilidad generalizada (3/5) y fatiga fácil, lo que dificulta realizar movimientos finos o sostenidos.

Evaluación de limitaciones visuales: Determinar agudeza visual, sensibilidad al contraste y capacidad de enfoque. Aunque no se reportan problemas visuales específicos en el caso, la EM puede asociarse con visión borrosa o nistagmo, por lo que se requiere contraste alto y elementos visuales grandes.

Evaluación de limitaciones cognitivas: Analizar memoria, atención y capacidad de procesamiento. El usuario mantiene estado consciente y comprensión de órdenes complejas, pero la fatiga puede afectar su concentración durante uso prolongado.

Evaluación de limitaciones de comprensión: Verificar comprensión de lenguaje oral, escrito y simbólico. El usuario comprende órdenes pero tiene emisión verbal ininteligible, por lo que requiere sistemas de comunicación aumentativa con retroalimentación visual clara.

Evidencia | incluida | (Datos | del | caso
seleccionado):

❖ Limitaciones Motoras:

Característica: Debilidad generalizada y fatiga fácil que afecta la interacción física con el dispositivo.

Evidencia: Del examen clínico: "Motricidad: debilidad generalizada (3/5), fatiga fácil."

❖ Capacidades | Cognitivas | y | de
Comprensión:

Característica: Comprensión de órdenes simples
y | complejas | conservada; | capacidad | de
comunicación mediante gestos.

Evidencia: Del examen clínico: "Estado de conciencia: lúcido, comprende órdenes simples y complejas. Lenguaje: emisión verbal ininteligible, comunicación limitada." Y de la funcionalidad inicial: "Puede comprender y responder con gestos."

❖ Estado Emocional:

Característica: Ánimo bajo.

Evidencia: De las funciones biológicas: "Ánimo bajo."

| social y emocional. ● Dependencia en contextos sociales y laborales para la comunicación. | | ❖ Necesidad Comunicativa Principal: Característica: Gran limitación en la comunicación oral, dependiente de sistemas alternativos. Evidencia: Del diagnóstico y la funcionalidad inicial: "Disartria severa y pérdida parcial del habla en paciente con EM avanzada.", "Gran limitación en la comunicación oral."
3. Análisis de tareas | Es el proceso mediante el cual se identifican y describen las acciones necesarias para que el usuario y el cuidador utilicen correctamente el prototipo. Permite determinar las tareas que se deben realizar para su funcionamiento, reconocer las tareas críticas que podrían generar daño o error, y evaluar los riesgos asociados a cada una. [4], [5]. | Listar todas las tareas que el usuario y el cuidador deben ejecutar para poner en marcha, operar y apagar el sistema (por ejemplo, encender el módulo, calibrar el eye-tracking, seleccionar comandos, activar sensores y detener la silla). Identificar aquellas tareas críticas cuya ejecución incorrecta podría comprometer la seguridad del usuario o el funcionamiento del dispositivo. [4], [6]. | Tabla de tareas y riesgos; justificación de criticidad. Evidencia incluida: Tabla que describe cada tarea, su tipo, los posibles riesgos asociados y una breve justificación de por qué se considera crítica. Esta información se obtuvo del análisis funcional del sistema y de la simulación práctica del uso del prototipo [1], [2].
4. Criterios de éxito (requisitos de usabilidad) | Son los indicadores concretos que permiten evaluar si el sistema es fácil, seguro y eficiente de usar. Estos criterios miden el desempeño del usuario (eficacia y eficiencia), su nivel de satisfacción y la seguridad del dispositivo durante las pruebas [4], [5], [6]. | Definir objetivos cuantificables para cada criterio de usabilidad: ● Eficacia: porcentaje de tareas completadas correctamente. ● Eficiencia: tiempo requerido para ejecutar las tareas. ● Satisfacción: percepción del usuario sobre comodidad y facilidad de uso. ● Seguridad: cantidad de errores o incidentes durante la prueba [6], [7]. | Tabla de métricas objetivo. Evidencia incluida: Resultados de pruebas de usabilidad con usuarios, cronometraje del tiempo de operación, encuestas SUS (System Usability Scale) y registro de incidentes. Estas métricas permiten verificar la facilidad, seguridad y confiabilidad del sistema [5], [6].

### Tabla de tareas y riesgos

Tarea | Descripción | Tipo de tarea | Riesgo asociado | Justificación de criticidad
Encendido del sistema | El cuidador enciende la caja maestra (ESP32) y verifica la conexión Bluetooth con la App. | Inicial / Configuración | Falla de conexión o sobrecalentamiento. | Sin conexión, el sistema no puede operar correctamente [2].
Calibración del eye-tracking | El usuario fija la mirada para calibrar el rastreador ocular antes del uso. | Configuración | Error en la detección del ojo o calibración imprecisa. | Un error de calibración puede generar movimientos no deseados de la silla [1].
Selección de comandos | El usuario selecciona con la mirada los botones de movimiento (adelante, izquierda, derecha, detener). | Operativa crítica | Activación involuntaria o errónea del comando. | Puede generar desplazamientos imprevistos o colisiones [2].
Activación de sensores ultrasónicos | El sistema detecta obstáculos y detiene el movimiento automáticamente. | Automática / Seguridad | Desalineación o interferencia del sensor. | Si no detecta obstáculos, puede ocurrir un accidente [2].
Uso del botón de emergencia | El cuidador o usuario presiona el botón físico para detener la silla. | Emergencia | Retardo o fallo del sistema ante la orden. | Es la función principal de seguridad ante fallos de software o hardware [7].
Apagado del sistema | El cuidador apaga la caja maestra y cierra la aplicación. | Finalización | Apagado incorrecto o pérdida de configuración. | Un apagado inadecuado puede dañar el hardware o corromper datos [5].

### Tabla de métricas objetivo

Criterio | Indicador de éxito | Métrica objetivo | Método de evaluación
Eficacia | Porcentaje de tareas realizadas correctamente (conexión, control, parada). | ≥ 95 % de tareas completadas sin error. | Observación directa durante pruebas supervisadas [5].
Eficiencia | Tiempo promedio desde encendido hasta la ejecución del primer movimiento. | < 2 minutos. | Cronometrado durante la sesión práctica [5].
Satisfacción | Percepción de facilidad y confort en el uso. | SUS ≥ 70. | Encuesta posterior a la prueba [6].
Seguridad | Número de colisiones o fallos críticos. | 0 incidentes por sesión. | Registro de bitácora de pruebas [2].
Confiabilidad | Tiempo de operación continua sin reinicios o bloqueos. | ≥ 60 minutos. | Prueba de estabilidad en laboratorio [2].
Accesibilidad | Diseño visual claro y elementos grandes para usuarios con limitaciones visuales. | Contraste > 70 %, iconos ≥ 1.5 cm. | Validación visual y revisión con usuario [1].

## Bibliografía

[1] C. Ferrín-Bolaños et al., «Interfaz humano-computador basada en gestos faciales y orientada a la aplicación WhatsApp para personas con limitación motriz de miembros superiores», TecnoLógicas, vol. 24, n.o 50, p. e1722, ene. 2021, doi: 10.22430/22565337.1722.
[2] J. M. Córdova, “Diseño de una silla de ruedas eléctrica controlada por voz para personas con discapacidad motriz,” Universidad Politécnica Salesiana, Guayaquil, Ecuador, 2018. [Online]. Available: https://dspace.ups.edu.ec/bitstream/123456789/16059/1/UPS-GT002280.pdf
[3] | World | Health | Organization, | “Disability | and | health,” | WHO | Fact | Sheets, | Oct. | 2022. | [Online]. | Available:
https://www.who.int/news-room/fact-sheets/detail/disability-and-health
[4] D. A. Norman, The Design of Everyday Things, Rev. and expanded ed. New York: Basic Books, 2013.
[5] J. Nielsen, Usability Engineering. San Francisco: Academic Press, 1994.
[6] J. Brooke, “SUS: A quick and dirty usability scale,” in Usability Evaluation in Industry, P. W. Jordan, B. Thomas, B. A. Weerdmeester, and I. L. McClelland, Eds. London: Taylor & Francis, 1996, pp. 189–194.
[7] International Organization for Standardization, ISO 9241-210: Ergonomics of Human-System Interaction – Part 210: Human-Centred Design for Interactive Systems, Geneva, Switzerland: ISO, 2018.
