AlessandroCrosby/GRUPO2/TALLERES/TALLERES SEMANA N°2/T2 - Entregable 2.pdf

NIVEL POLLO:

- Horizontal:

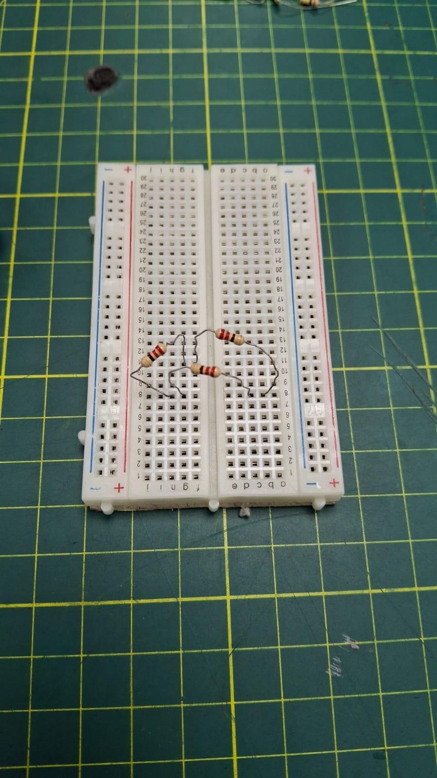
[picture p148: figure]

- Vertical:

NIVEL GATO:

- Horizontal:

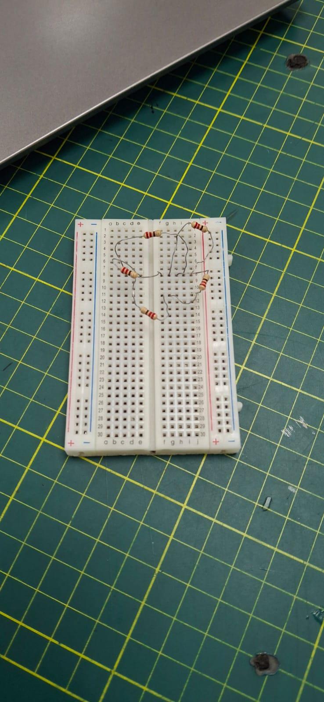
[picture p149: figure]

- Vertical:

NIVEL DRAGÓN:

- Horizontal:

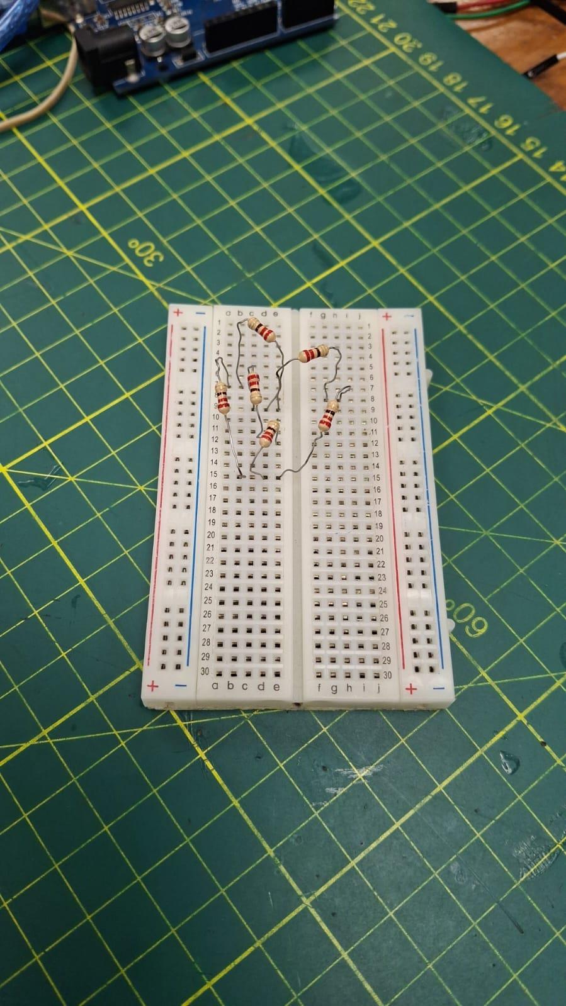
[picture p150: figure]

- Vertical:
