AlessandroCrosby/GRUPO2/TALLERES/TALLERES SEMANA N°5/Fernandez García, Paola Andrea/paola-fernandez-0e73c01a-8400-4122-8615-0be7cb9d28c3-certificate.pdf

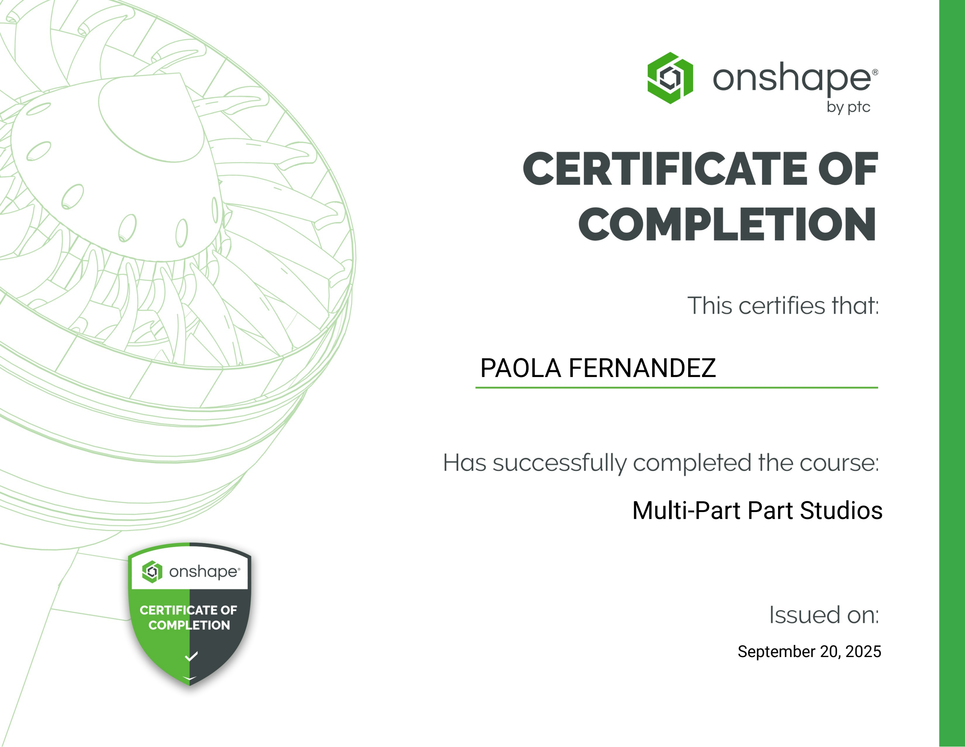
[picture p151: page 1]

PAOLA FERNANDEZ

September 20, 2025

Multi-Part Part Studios
