AlessandroCrosby/GRUPO2/TALLERES/TALLERES SEMANA N°5/Fernandez García, Paola Andrea/paola-fernandez-351027fe-3fa6-4f8b-a15e-0fac20326197-certificate.pdf

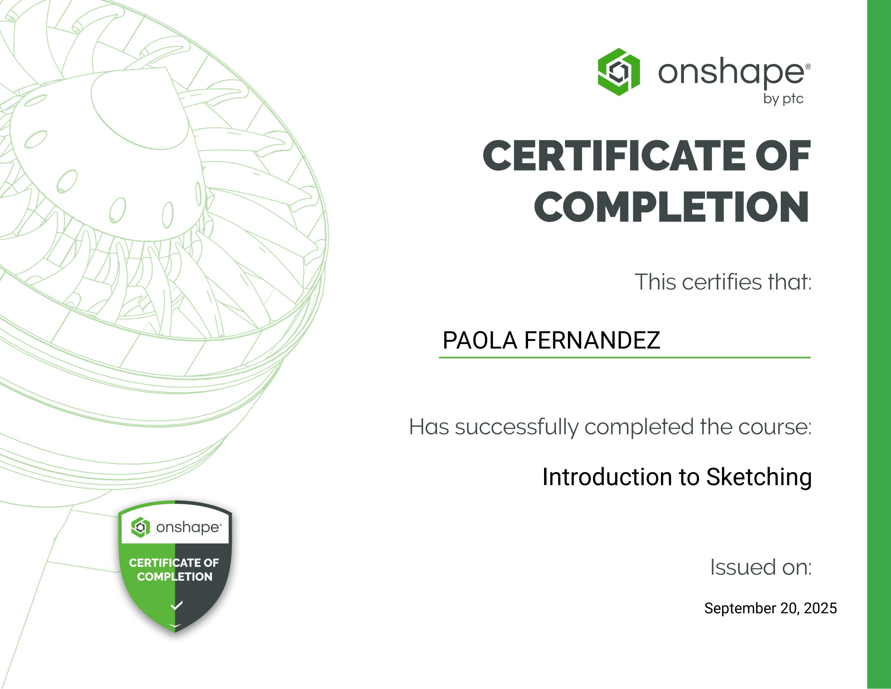
[picture p152: page 1]

PAOLA FERNANDEZ

Introduction to Sketching

September 20, 2025
