AlessandroCrosby/GRUPO2/TALLERES/TALLERES SEMANA N°5/Fernandez García, Paola Andrea/paola-fernandez-bb560dbd-75e2-441b-a428-13dfef4abb3d-certificate.pdf

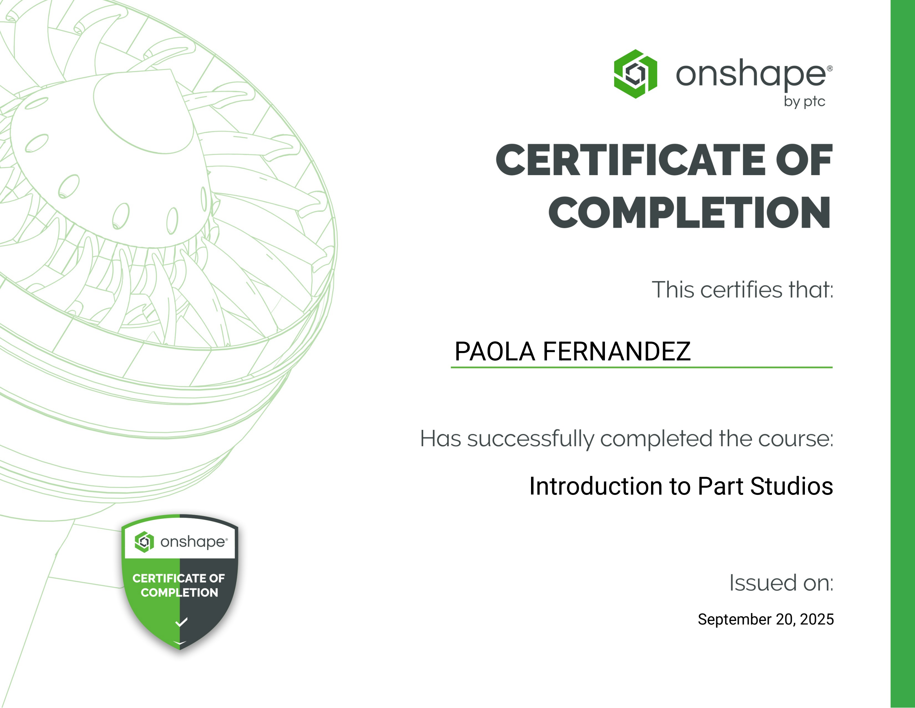
[picture p153: page 1]

PAOLA FERNANDEZ

Introduction to Part Studios

September 20, 2025
