AlessandroCrosby/GRUPO2/TALLERES/TALLERES SEMANA N°5/Fernandez García, Paola Andrea/paola-fernandez-c09a783c-87af-457d-ac6f-3a8fa06c29f1-certificate (1).pdf

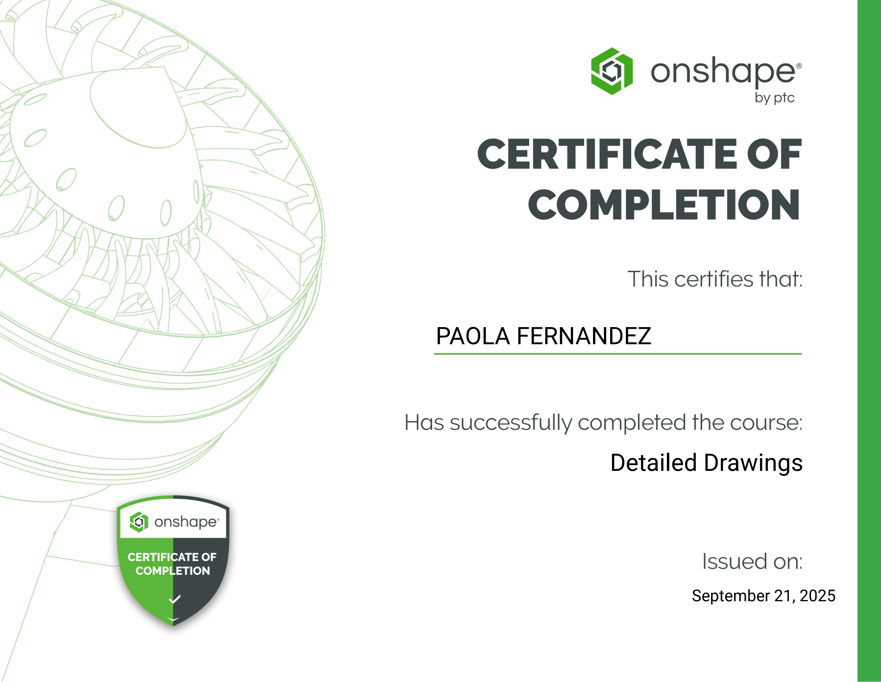
[picture p154: page 1]

PAOLA FERNANDEZ

September 21, 2025

Detailed Drawings
