AlessandroCrosby/GRUPO2/TALLERES/TALLERES SEMANA N°5/Cordova Palomino, Brandy Abigail/Certificado - Introducción a Part Studios.pdf

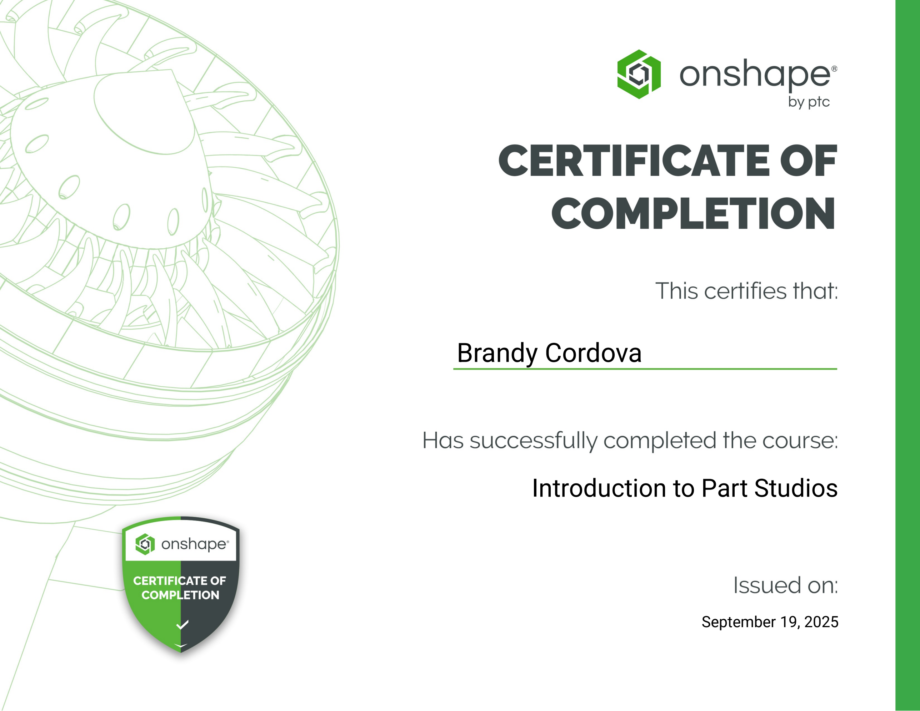
[picture p155: page 1]

Brandy Cordova

Introduction to Part Studios

September 19, 2025
