AlessandroCrosby/GRUPO2/TALLERES/TALLERES SEMANA N°5/Cordova Palomino, Brandy Abigail/Certificado-boceto.pdf

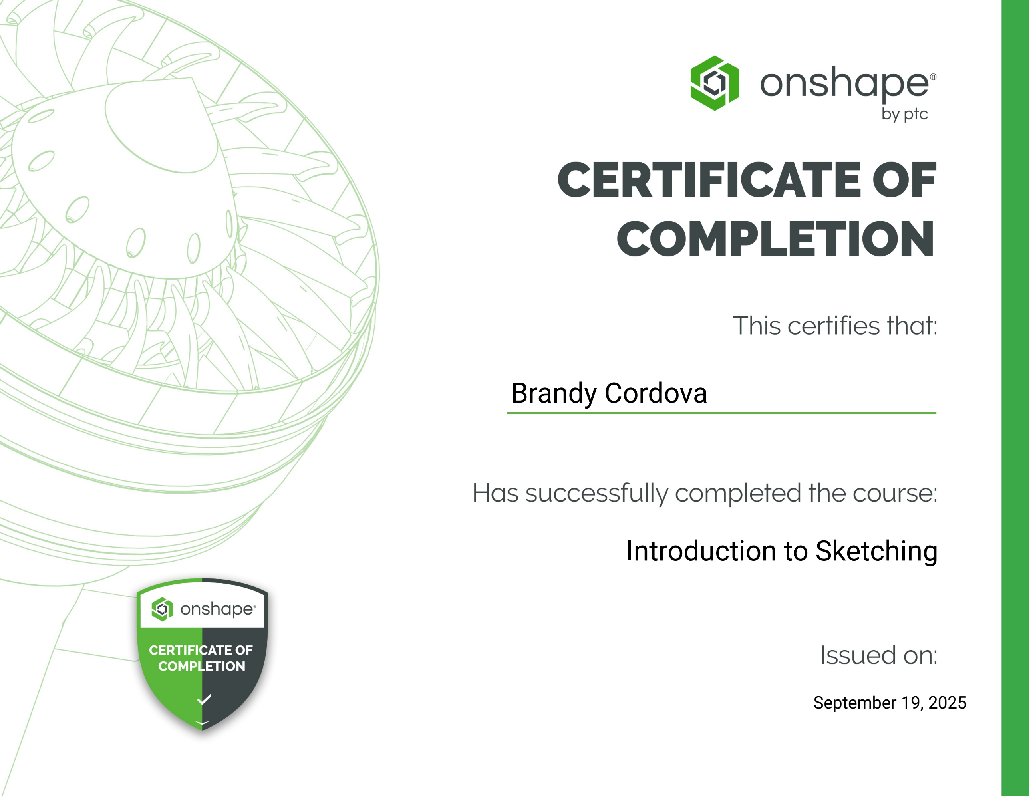
[picture p156: page 1]

Brandy Cordova

Introduction to Sketching

September 19, 2025
