AlessandroCrosby/GRUPO2/TALLERES/TALLERES SEMANA N°5/Cordova Palomino, Brandy Abigail/Certificado-Dibujos detallados.pdf

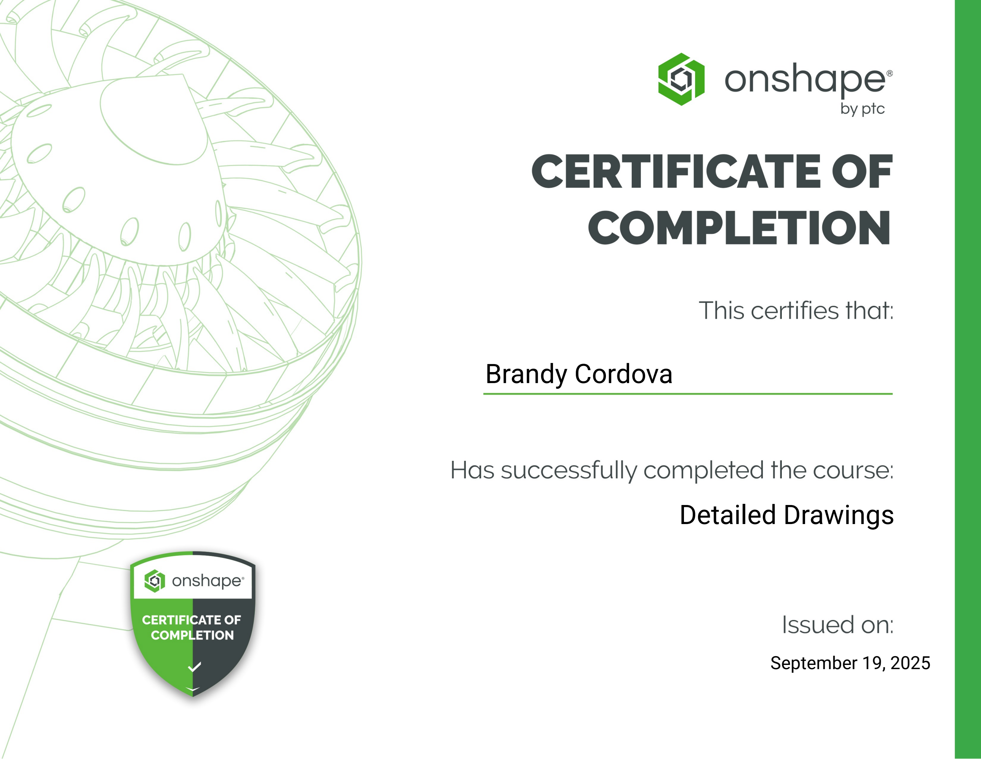
[picture p157: page 1]

Brandy Cordova

September 19, 2025

Detailed Drawings
