AlessandroCrosby/GRUPO2/TALLERES/TALLERES SEMANA N°5/Cordova Palomino, Brandy Abigail/Certificado-Estudios de varias partes.pdf

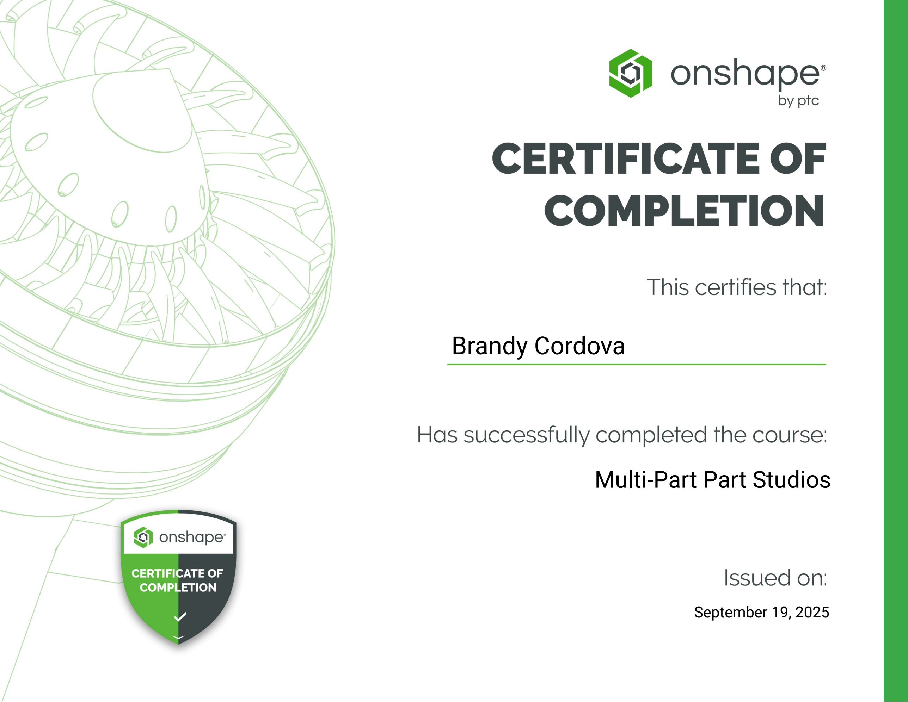
[picture p158: page 1]

Brandy Cordova

September 19, 2025

Multi-Part Part Studios
