AlessandroCrosby/GRUPO2/TALLERES/TALLERES SEMANA N°5/Fuentes Contreras, Arianna Fabiana del Valle/Arianna_Fuentes_DETAILED DRAWINGS.pdf

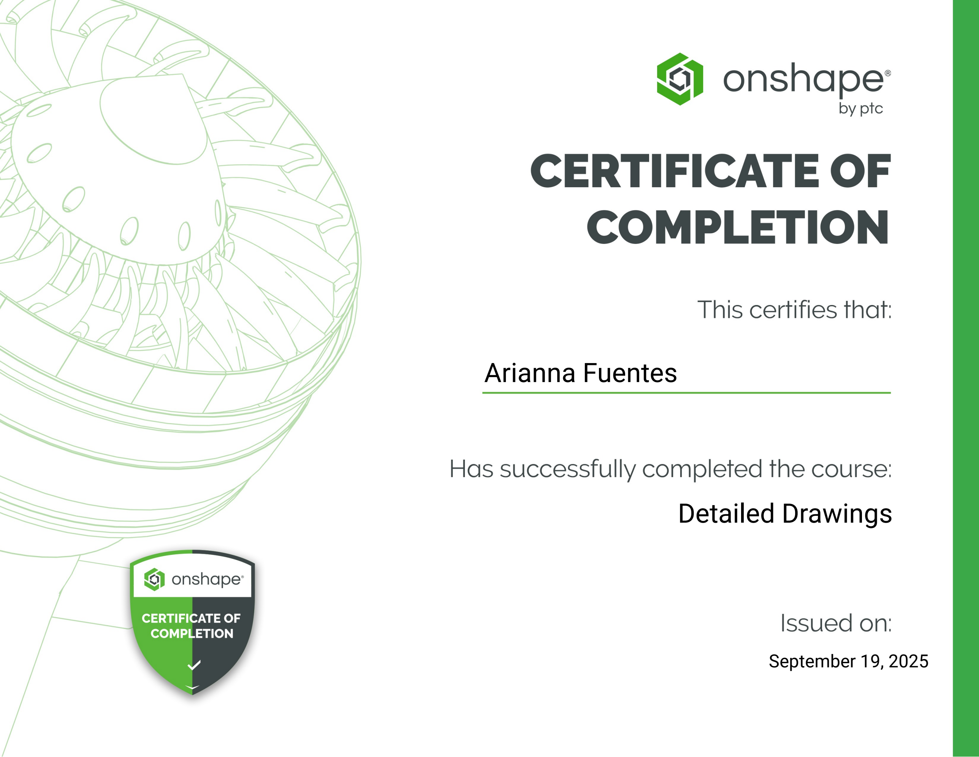
[picture p159: page 1]

Arianna Fuentes

September 19, 2025

Detailed Drawings
