AlessandroCrosby/GRUPO2/TALLERES/TALLERES SEMANA N°5/Fuentes Contreras, Arianna Fabiana del Valle/Arianna_Fuentes_INTRODUCTION TO PART STUDIOS.pdf

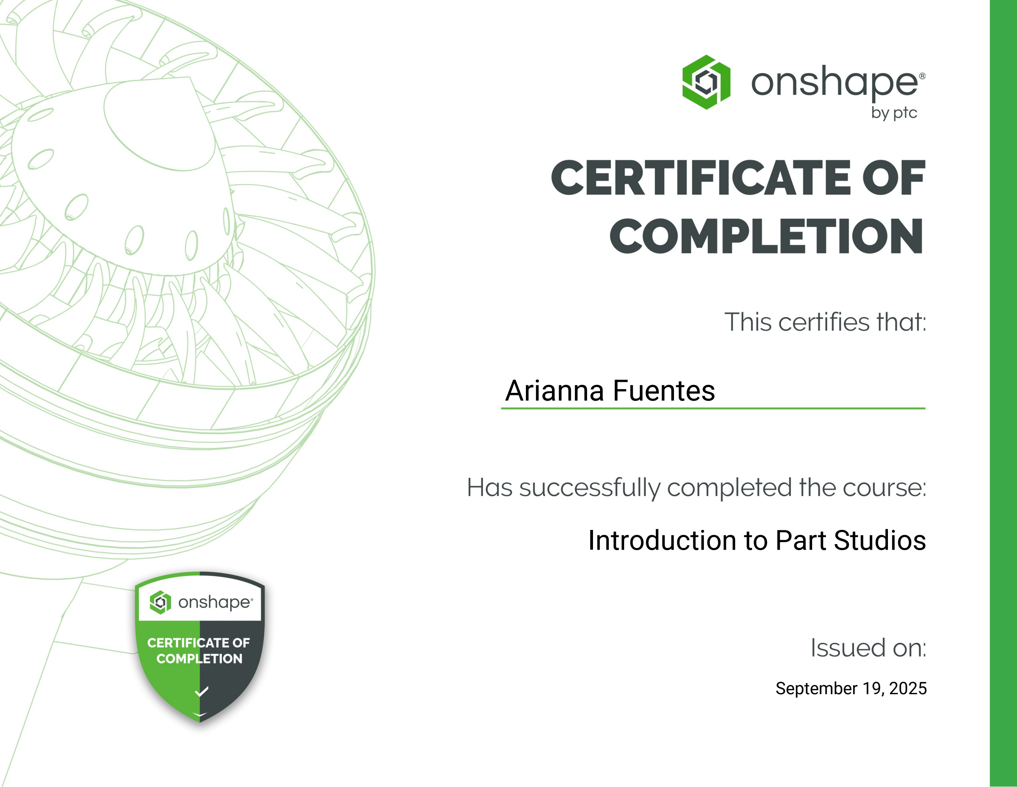
[picture p160: page 1]

Arianna Fuentes

Introduction to Part Studios

September 19, 2025
