AlessandroCrosby/GRUPO2/TALLERES/TALLERES SEMANA N°5/Fuentes Contreras, Arianna Fabiana del Valle/Arianna_Fuentes_INTRODUCTION TO SKETCHING.pdf

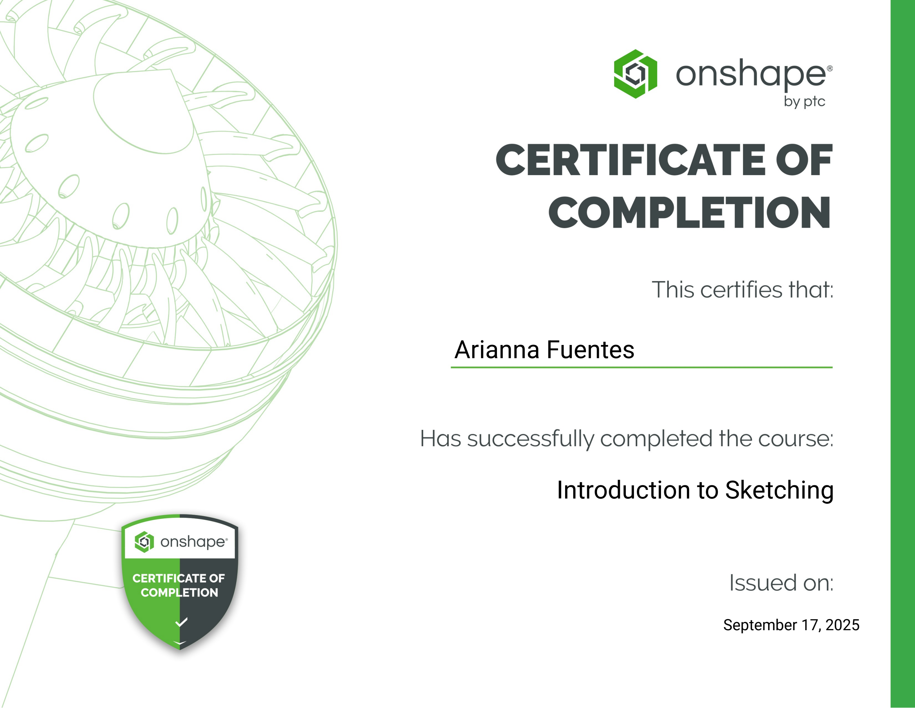
[picture p161: page 1]

Arianna Fuentes

Introduction to Sketching

September 17, 2025
