AlessandroCrosby/GRUPO2/TALLERES/TALLERES SEMANA N°5/Fuentes Contreras, Arianna Fabiana del Valle/Arianna_Fuentes_MULTI-PART PART STUDIOS.pdf

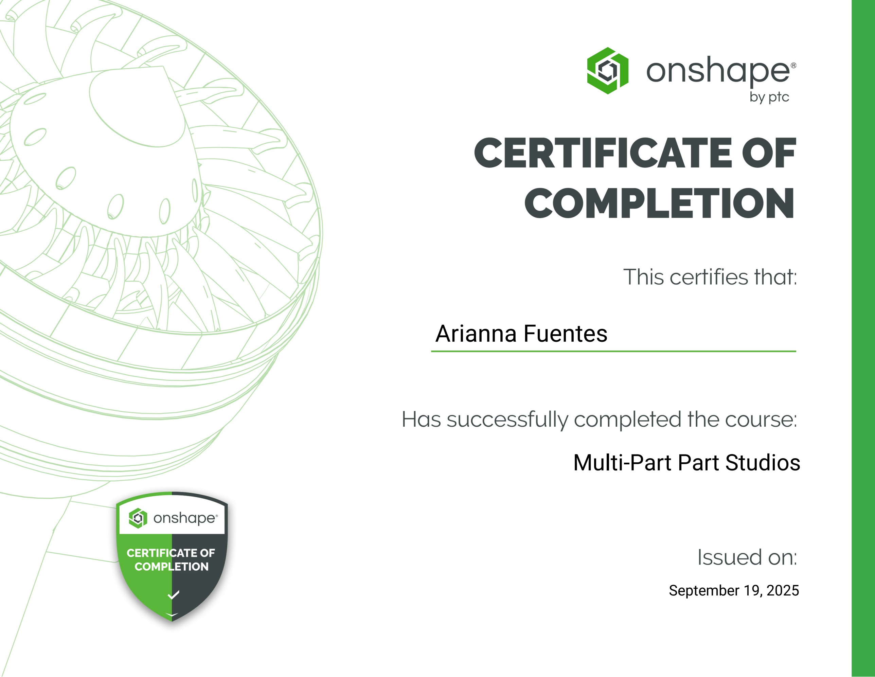
[picture p162: page 1]

Arianna Fuentes

September 19, 2025

Multi-Part Part Studios
