AlessandroCrosby/GRUPO2/TALLERES/TALLERES SEMANA N°5/Espinoza Padilla, Sebastian Amadeus/CERTIFICADO 1 - SEBASTIÁN ESPINOZA.pdf

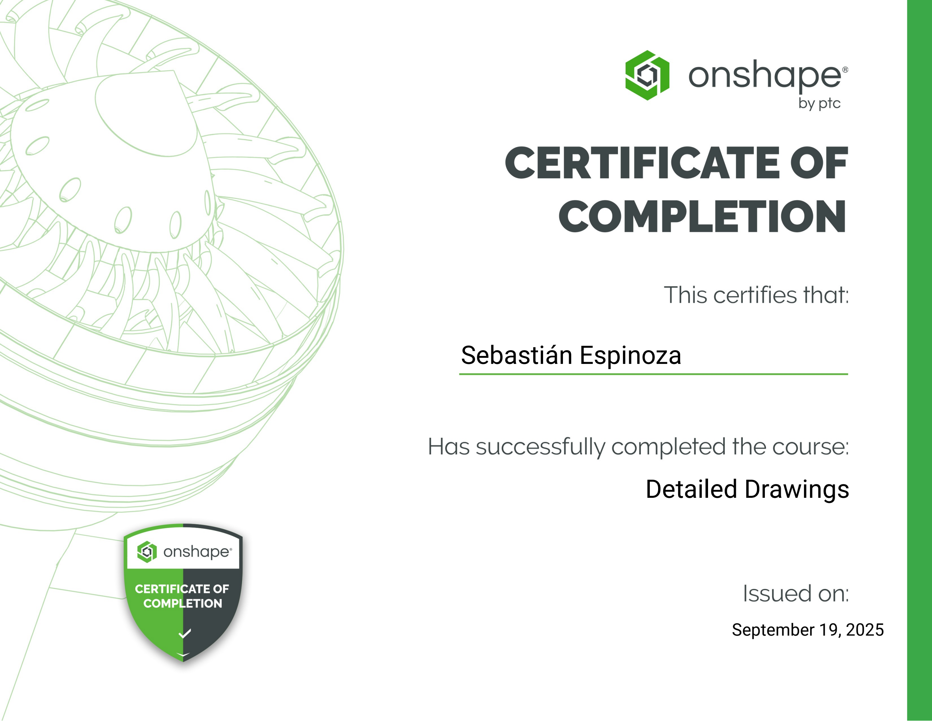
[picture p163: page 1]

Sebastián Espinoza

September 19, 2025

Detailed Drawings
