AlessandroCrosby/GRUPO2/TALLERES/TALLERES SEMANA N°5/Espinoza Padilla, Sebastian Amadeus/CERTIFICADO 2 - SEBASTIÁN ESPINOZA.pdf

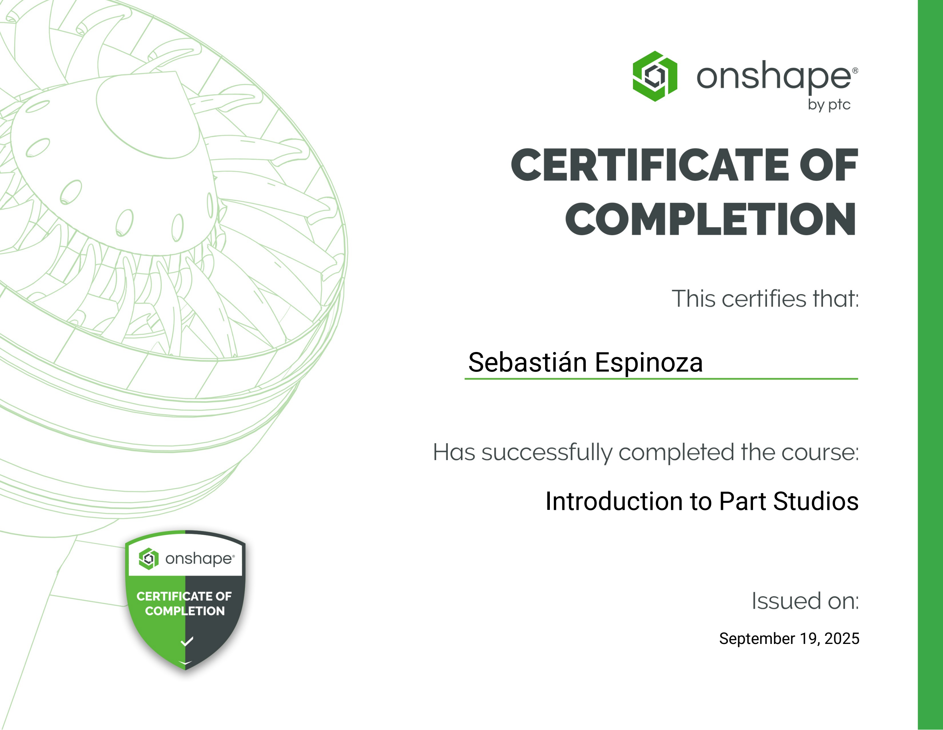
[picture p164: page 1]

Sebastián Espinoza

Introduction to Part Studios

September 19, 2025
