AlessandroCrosby/GRUPO2/TALLERES/TALLERES SEMANA N°5/Espinoza Padilla, Sebastian Amadeus/CERTIFICADO 3 - SEBASTIÁN ESPINOZA.pdf

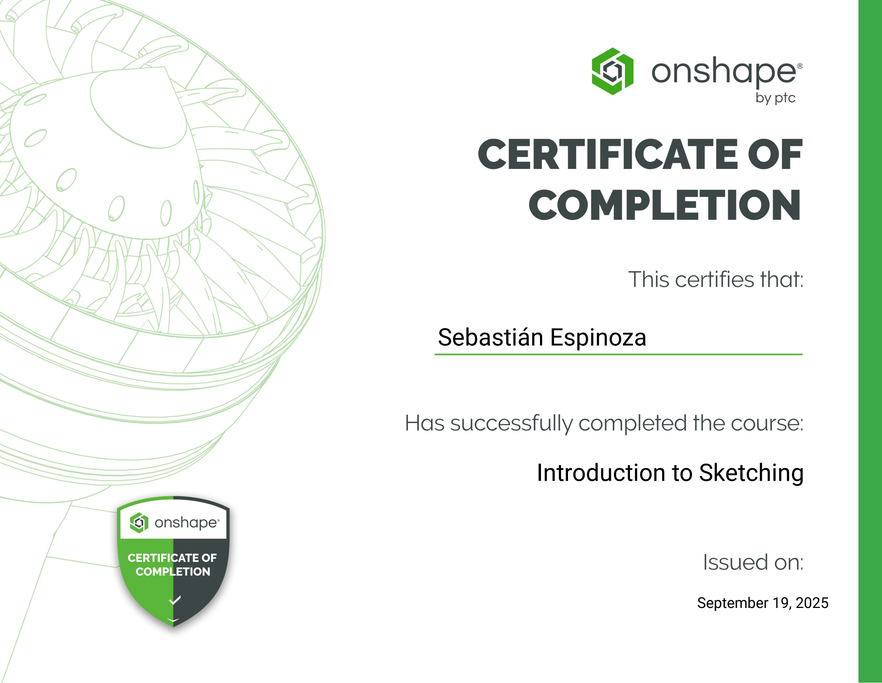
[picture p165: page 1]

Sebastián Espinoza

Introduction to Sketching

September 19, 2025
