AlessandroCrosby/GRUPO2/TALLERES/TALLERES SEMANA N°5/Espinoza Padilla, Sebastian Amadeus/CERTIFICADO 4 - SEBASTIÁN ESPINOZA.pdf

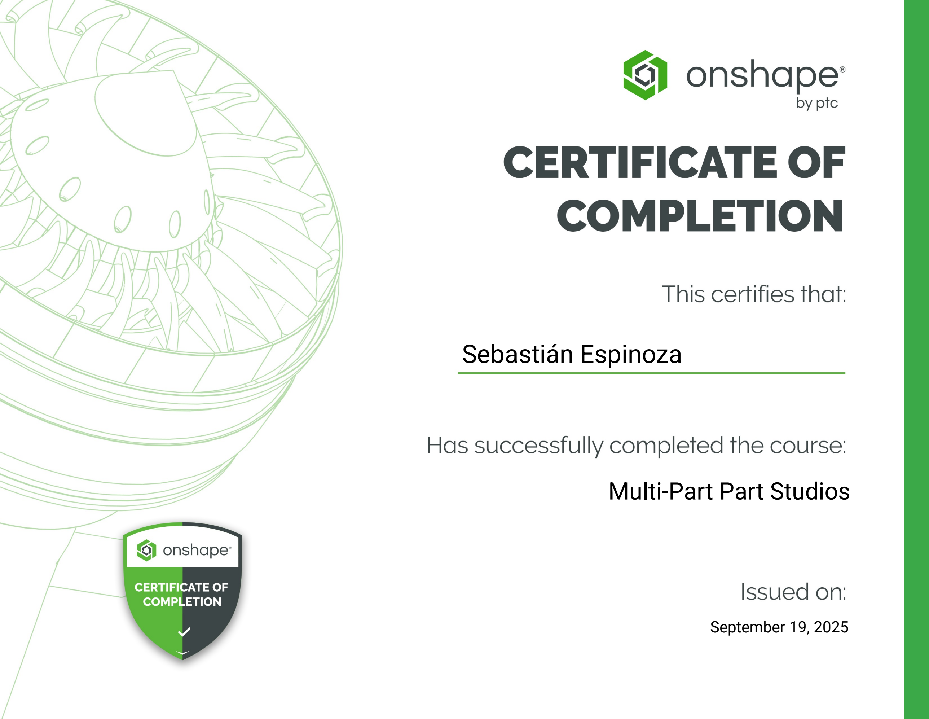
[picture p166: page 1]

Sebastián Espinoza

September 19, 2025

Multi-Part Part Studios
