AlessandroCrosby/GRUPO2/TALLERES/TALLERES SEMANA N°5/Condori Pompilio, Pabel Mario/mario-pompilio-181177f3-0594-4d01-954e-b05a50adc350-certificate.pdf

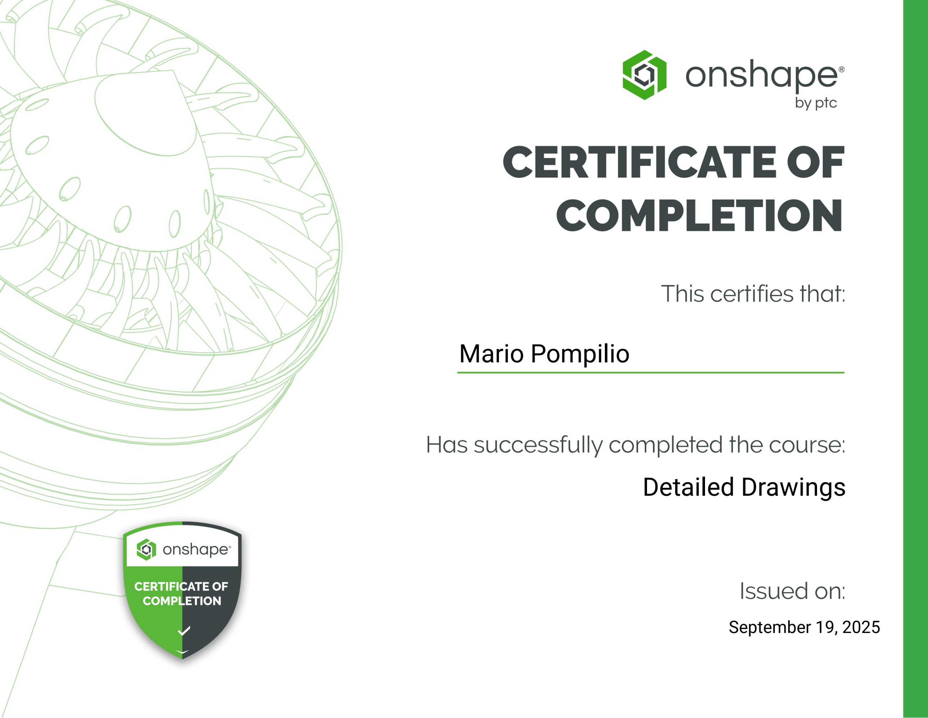
[picture p167: page 1]

Mario Pompilio

September 19, 2025

Detailed Drawings
