AlessandroCrosby/GRUPO2/TALLERES/TALLERES SEMANA N°5/Condori Pompilio, Pabel Mario/mario-pompilio-3bf081cb-a4ac-4c37-9e74-448e70caadb8-certificate.pdf

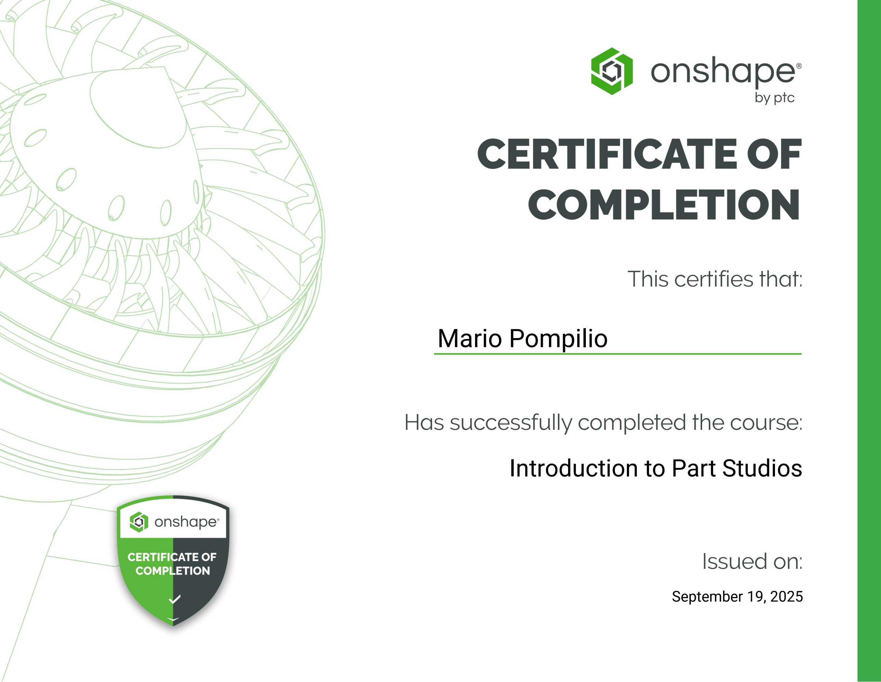
[picture p168: page 1]

Mario Pompilio

Introduction to Part Studios

September 19, 2025
