AlessandroCrosby/GRUPO2/TALLERES/TALLERES SEMANA N°5/Condori Pompilio, Pabel Mario/mario-pompilio-b14564b3-5958-4e6c-8011-4ced1874a12a-certificate.pdf

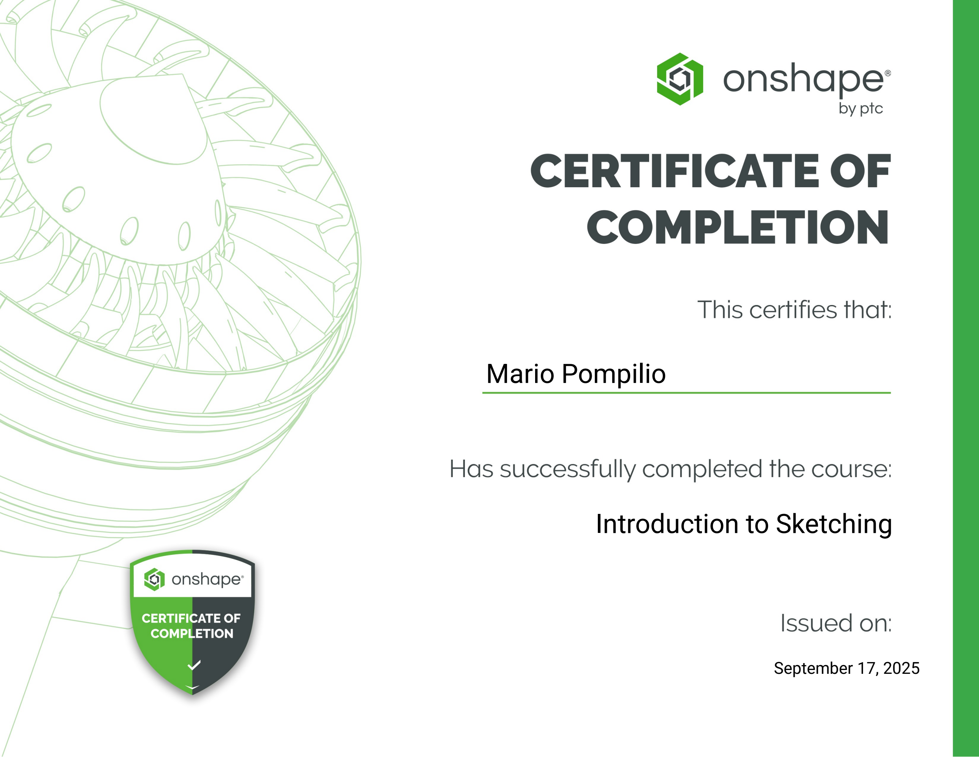
[picture p169: page 1]

Mario Pompilio

Introduction to Sketching

September 17, 2025
