AlessandroCrosby/GRUPO2/TALLERES/TALLERES SEMANA N°5/Condori Pompilio, Pabel Mario/mario-pompilio-d6866049-fd2c-4adb-bc8d-93340ebdb7ff-certificate.pdf

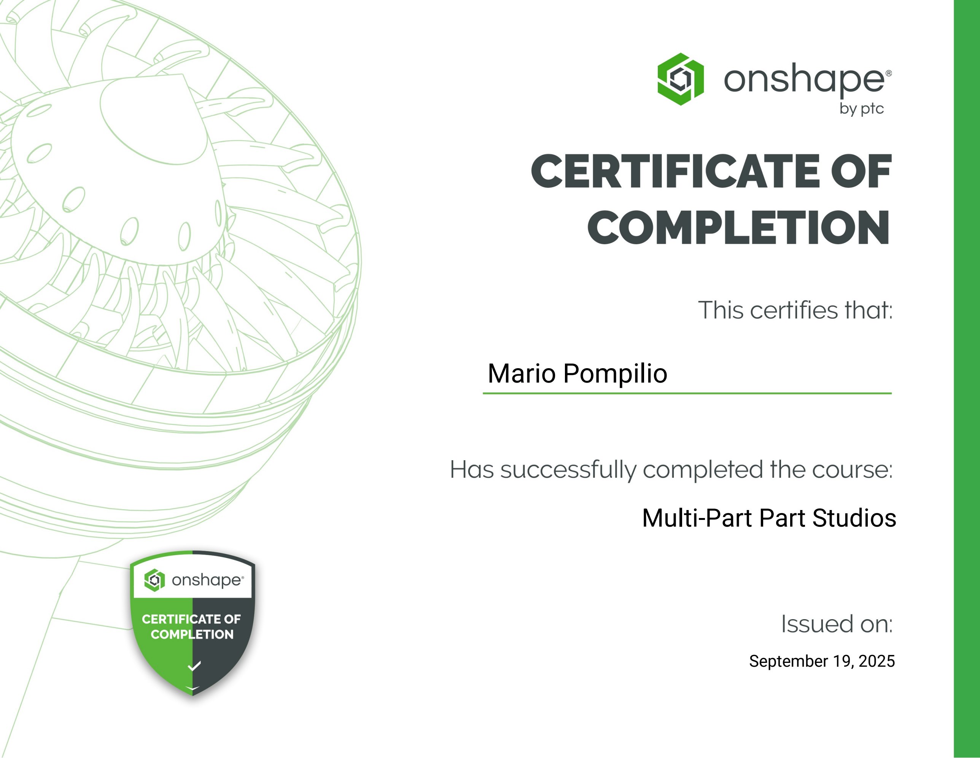
[picture p170: page 1]

Mario Pompilio

September 19, 2025

Multi-Part Part Studios
