AlessandroCrosby/GRUPO2/TALLERES/TALLERES SEMANA N°5/Crosby Collantes, Alessandro Nicolas/CERTIFICADO 1 - NICOLAS CROSBY.pdf

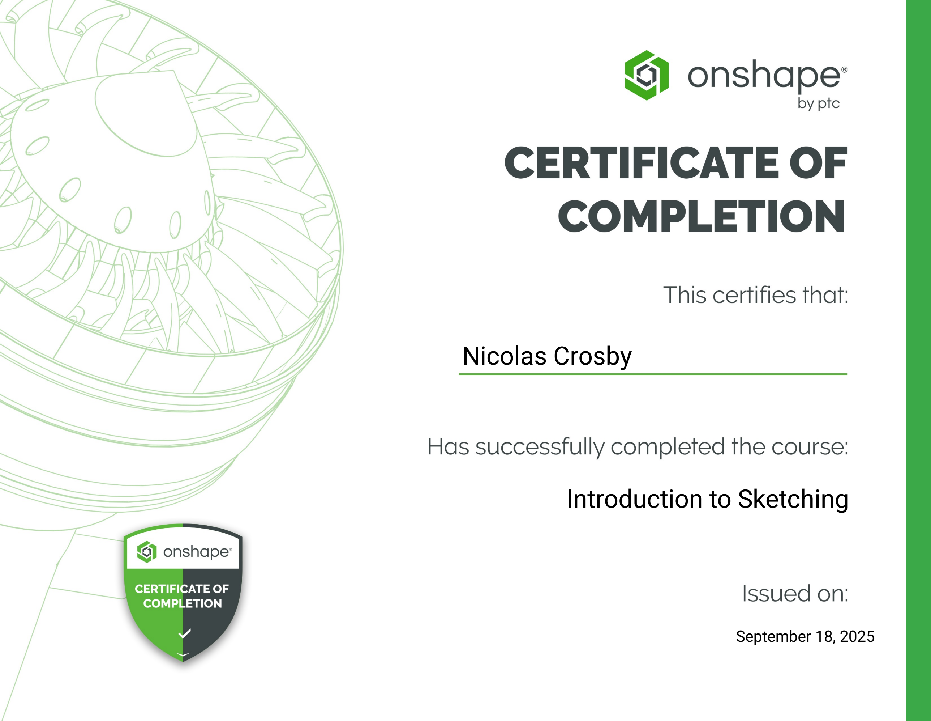
[picture p171: page 1]

Nicolas Crosby

Introduction to Sketching

September 18, 2025
