AlessandroCrosby/GRUPO2/TALLERES/TALLERES SEMANA N°5/Crosby Collantes, Alessandro Nicolas/CERTIFICADO 2 - NICOLAS CROSBY.pdf

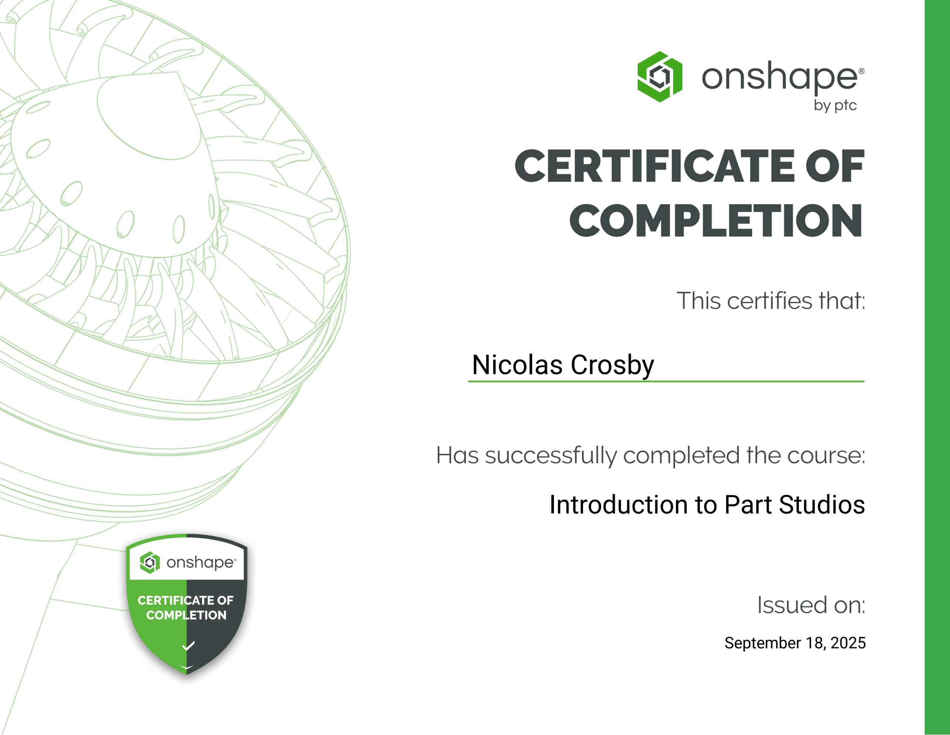
[picture p172: page 1]

Nicolas Crosby

Introduction to Part Studios

September 18, 2025
