AlessandroCrosby/GRUPO2/TALLERES/TALLERES SEMANA N°5/Crosby Collantes, Alessandro Nicolas/CERTIFICADO 3 - NICOLAS CROSBY.pdf

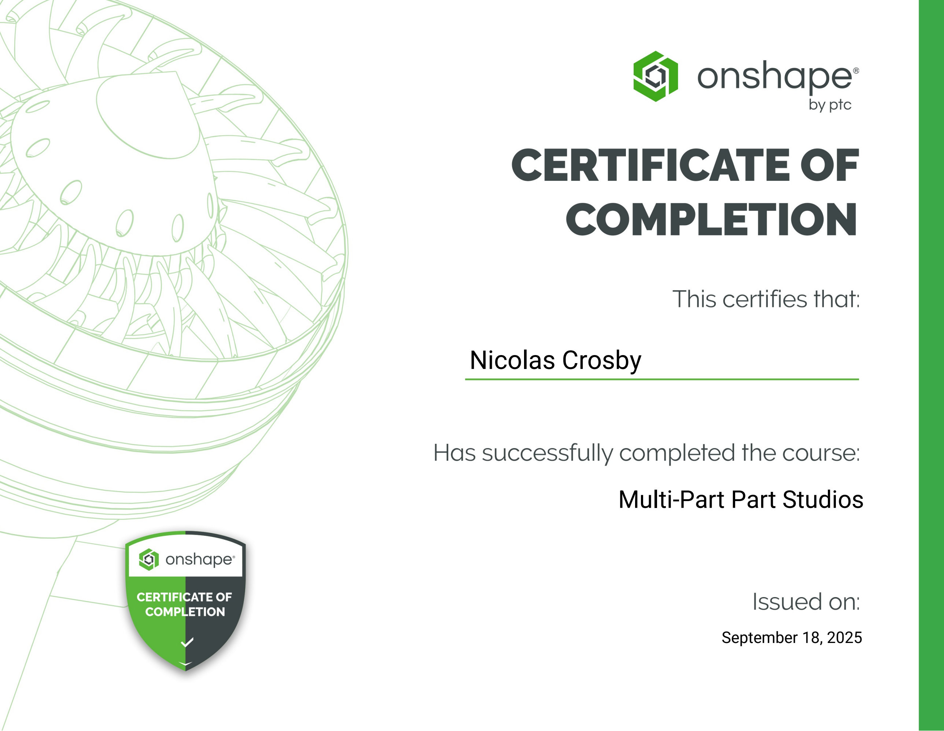
[picture p173: page 1]

Nicolas Crosby

September 18, 2025

Multi-Part Part Studios
