AlessandroCrosby/GRUPO2/TALLERES/TALLERES SEMANA N°5/Crosby Collantes, Alessandro Nicolas/CERTIFICADO 5 - NICOLAS CROSBY.pdf

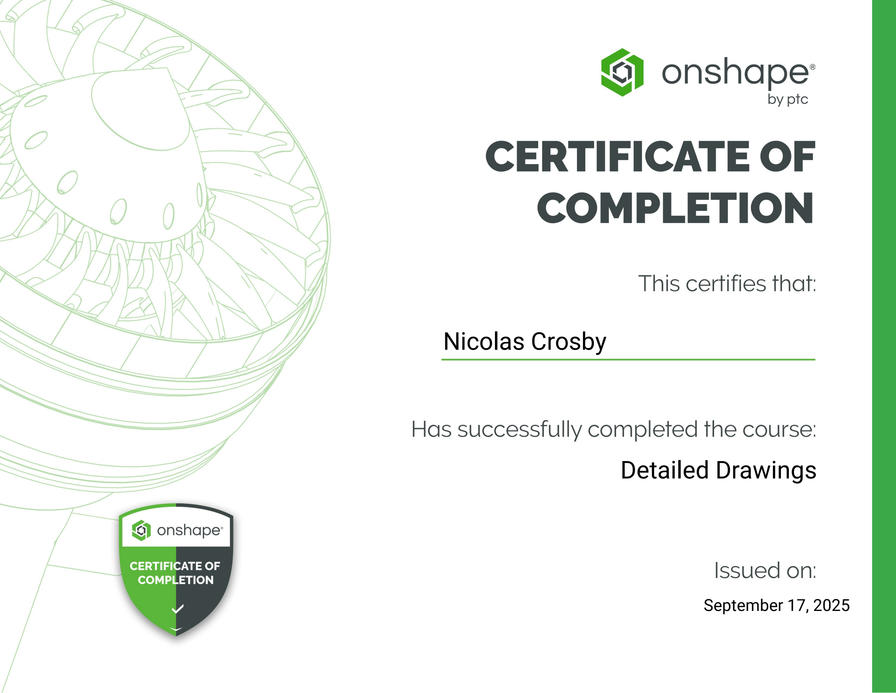
[picture p174: page 1]

Nicolas Crosby

September 17, 2025

Detailed Drawings
