AlessandroCrosby/GRUPO2/ENTREGABLES/ENTREGABLES SEMANA N°2/ENTREGABLE N°2 - CASO CLÍNICO.pdf

## FUNDAMENTOS DE BIODISEÑO

# CASO CLÍNICO - ESCLEROSIS

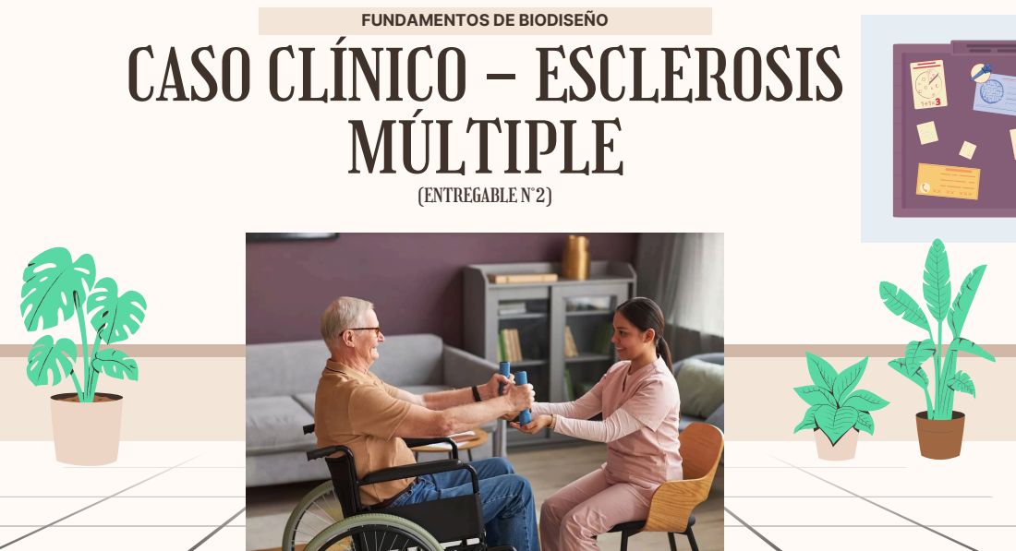
[picture p186: page 1]
MÚLTIPLE; (ENTREGABLE N°2)

1

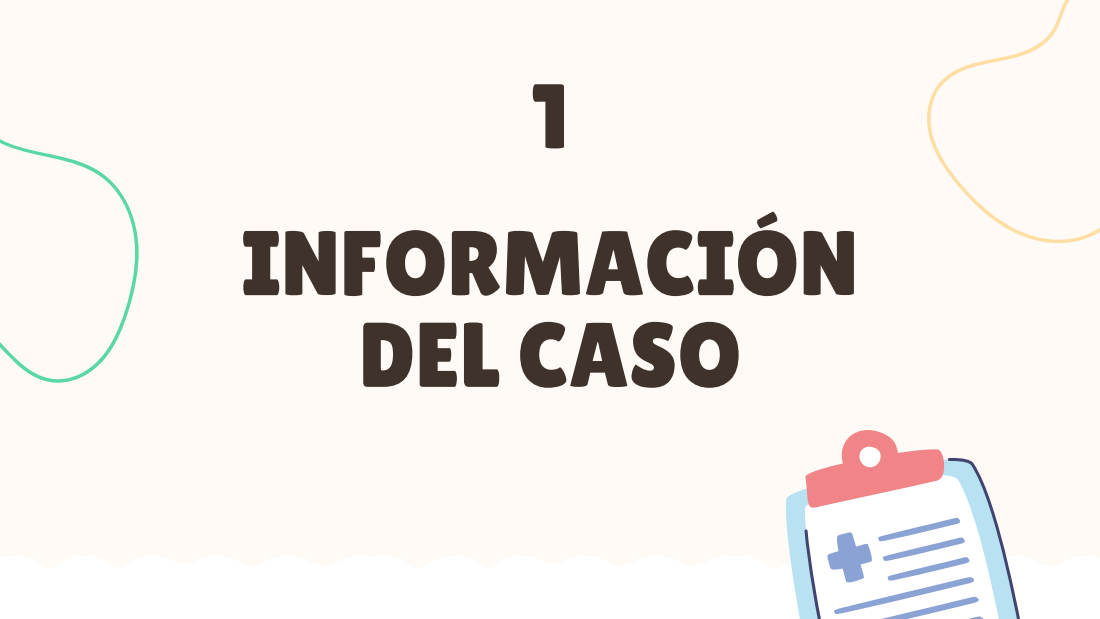
[picture p187: page 2]
INFORMACIÓN DEL CASO

## Nombre: Marco Aurelio Dirección del cliente: Jr. Bolognesi

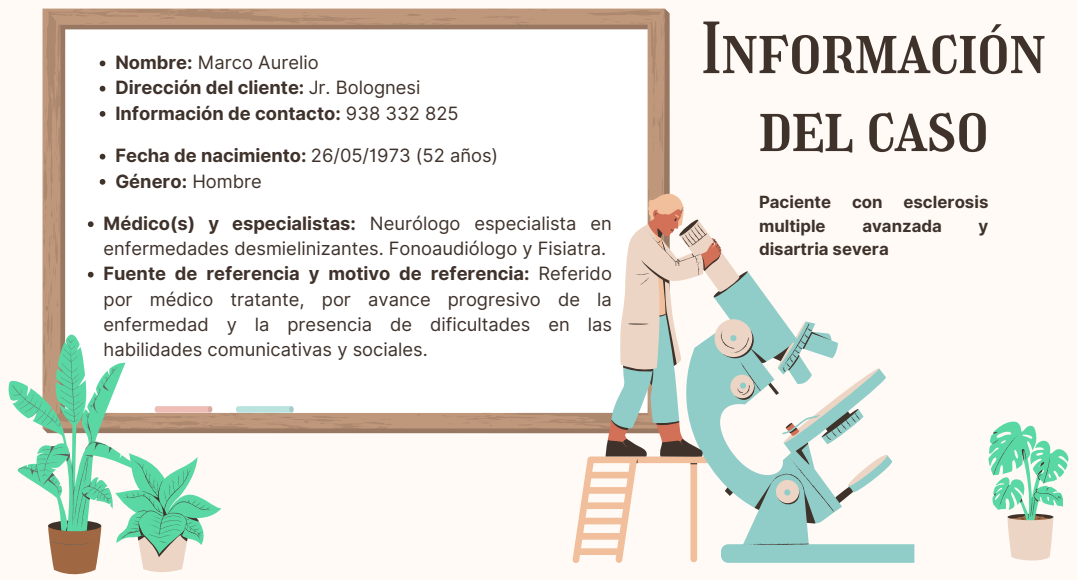
[picture p188: page 3]
enfermedad y la presencia de dificultades en; las; multiple; avanzada; Información del caso

Información de contacto: 938 332 825

Fecha de nacimiento: 26/05/1973 (52 años)
Género: Hombre

Paciente con esclerosis
disartria severa

Médico(s) y especialistas: Neurólogo especialista en
enfermedades desmielinizantes. Fonoaudiólogo y Fisiatra.
Fuente de referencia y motivo de referencia: Referido
por médico tratante, por avance progresivo de la
habilidades comunicativas y sociales.

## Régimen A: Seguimiento periódico por neurología junto con ajuste de

fármacos a medida del avance de la enfermedad.

## Objetivo A: Registrar la progresión de la enfermedad, controlar síntomas

asociados y mejorar calidad de vida.

## Régimen B: Implementación de tableros de comunicación o aplicaciones

digitales.

## Objetivo B: Garantizar una vía efectiva de comunicación, fomentar la

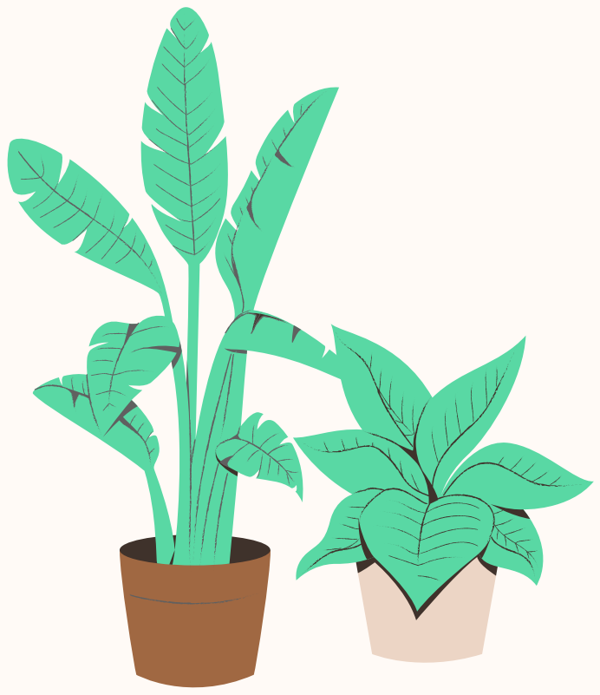
[picture p189: figure]

autonomía y reducir la dependencia del paciente.

## Régimen C: Realizar sesiones de psicoterapia individual y/o farmacoterapia

antidepresiva según necesidad del paciente.
Objetivo C: Mejorar el estado de ánimo, favorecer la adaptación emocional,

## reducir el impacto de la depresión, promover autonomía, participación

social y mejorar calidad de vida familiar.

# Regímenes de tratamiento y objetivos

2

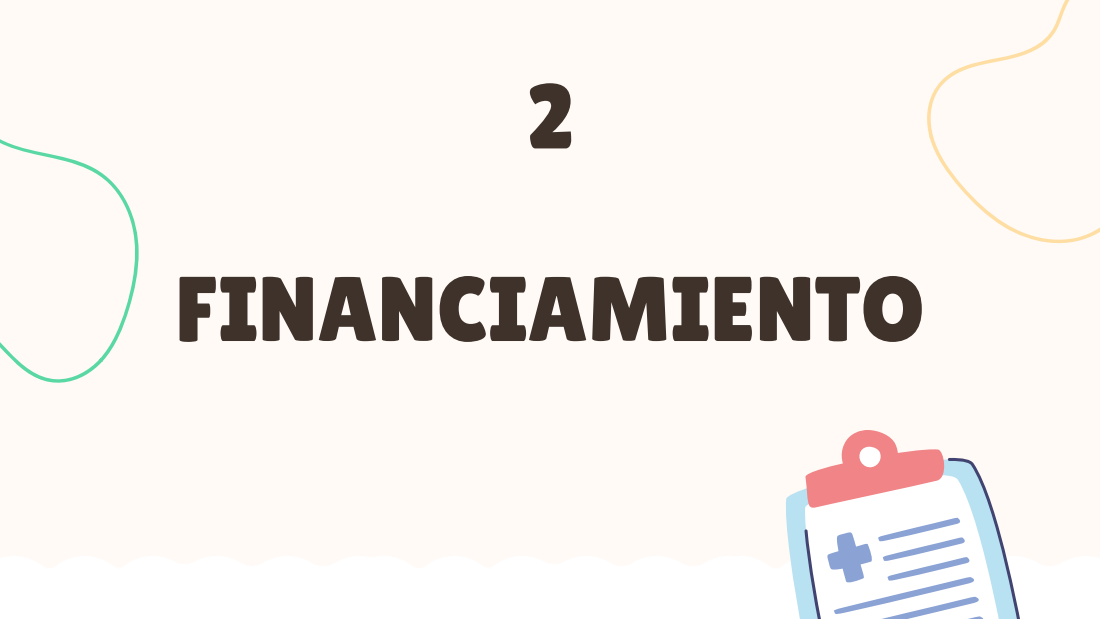
[picture p190: page 5]
FINANCIAMIENTO

# Fuentes de financiamiento

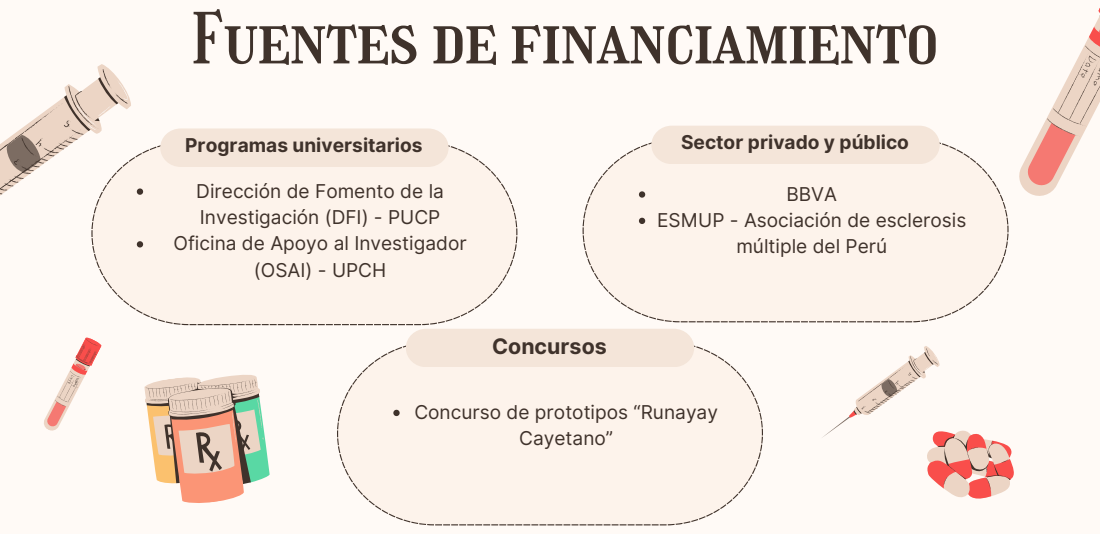
[picture p191: page 6]
Cayetano”; Concursos; (OSAI) - UPCH; Programas universitarios; BBVA

Sector privado y público

Dirección de Fomento de la
Investigación (DFI) - PUCP
Oficina de Apoyo al Investigador

ESMUP - Asociación de esclerosis

múltiple del Perú

Concurso de prototipos “Runayay

Dirección de Fomento de la Investigación (DFI) -PUCP: Apoya la creación de proyectos desarrollados por docentes y estudiantes, sean internos o destinados a fuentes externas. Las convocatorias pueden ser concursables y no concursables, ofreciendo flexibilidad especialmente en los fondos no concursables. Por otro lado, los criterios de evaluación incluyen calidad del proyecto, impacto social y cumplimiento de metas

dentro del plan institucional.

## Oficina de Apoyo al Investigador (OSAI) - UPCH: Brinda asistencia a investigadores en la búsqueda de financiamiento, así como en la gestión de trámites administrativos, desde la postulación hasta la ejecución y cierre de proyectos. Los proyectos internos pueden

financiarse desde fondos generados internamente,

## siempre y cuando estén debidamente gestionados y aprobados a través de la OSAI. Además gestionan desde cartas fianza hasta apertura de cuentas

bancarias y seguimiento administrativo.

Política de la fuente de financiamiento,

# criterios de aprobación y flexibilidad

vri@pucp.edu.pe / (511) 626-2000 | dupgict.osai@oficinas-upch.pe

## BBVA: Cuenta con programas de responsabilidad social y de innovación, sus fondos suelen dirigirse a proyectos de impacto social, innovación tecnológica y sostenibilidad. Posee como criterios de aprobación, la

innovación y aplicabilidad del proyecto en la sociedad,

## viabilidad técnica y financiera del proyecto. Por otro lado, pueden otorgar financiamiento parcial o total, con

posibilidad de patrocinios, becas, apoyo logístico,

## dependiendo de la convocatoria y tipo de proyecto

presentado.

Política de la fuente de financiamiento,

# criterios de aprobación y flexibilidad

## ESMUP – Asociación de Esclerosis Múltiple del Perú: Es una asociación sin fines de lucro que busca mejorar la

calidad de vida de personas con esclerosis múltiple.

## Dentro de los criterios para establecer una línea de comunicación con la finalidad de obtener acceso a

pacientes para pruebas piloto, voluntariado, difusión,

## apoyo en eventos de sensibilización por parte de la organización seria tener relevancia directa para las

personas con EM, contribución a la rehabilitación,

## accesibilidad o comunicación de pacientes y alineación

con la misión de la asociación.

eminformate@gmail.com / (+51) 996816131 | (01) 595-0000

Concurso de prototipos “Runayay Cayetano”: Busca promover la creatividad y el impacto de proyectos en áreas como salud, tecnología y medio ambiente. El concurso requiere que el prototipo, ya sea software o proceso nuevo o mejorado, se desarrolle en el marco de actividades académicas o de investigación en la Universidad Peruana Cayetano Heredia. Los equipos

deben estar conformados por 2 a 4 integrantes,

## incluyendo al menos un profesor y un estudiante. En cuanto a los premios al primer puesto se le otorgara S/

3,000, al segundo S/ 2,000 y tercer puesto S/ 1,000.

Política de la fuente de financiamiento,

# criterios de aprobación y flexibilidad

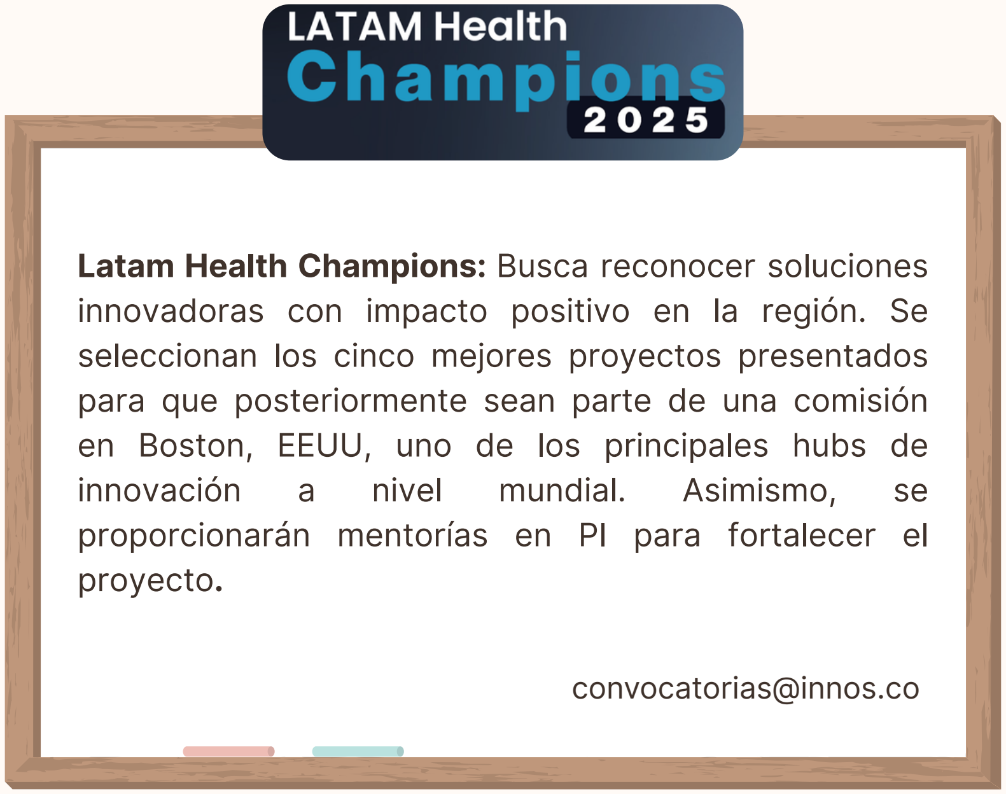
[picture p192: figure]
proyecto.; convocatorias@innos.co

## Latam Health Champions: Busca reconocer soluciones innovadoras con impacto positivo en la región. Se seleccionan los cinco mejores proyectos presentados para que posteriormente sean parte de una comisión en Boston, EEUU, uno de los principales hubs de

innovación | a | nivel | mundial. | Asimismo, | se

## proporcionarán mentorías en PI para fortalecer el

# alternativas de financiamiento

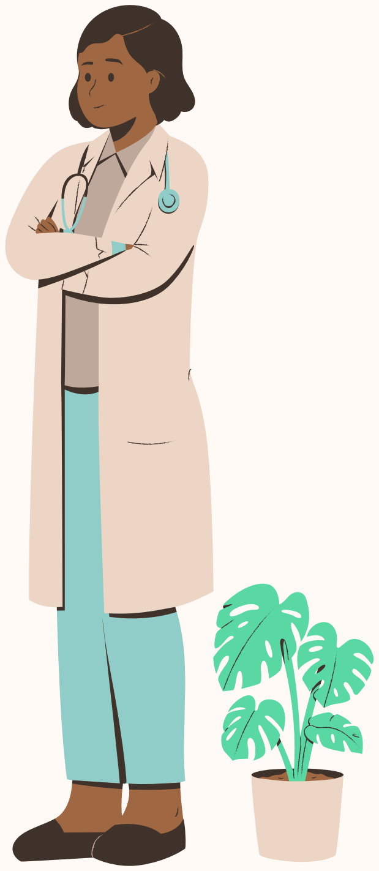
[picture p193: figure]

El financiamiento no se limita únicamente a aportes monetarios, sino que también puede darse a través de mentorías brindadas por fundaciones, instituciones académicas o empresas tecnológicas, que aporten conocimientos y habilidades a cada uno de los integrantes que conforman el grupo de forma que permitan potenciar el desarrollo del prototipo. Por otro lado, puede obtenerse mediante mecanismos como el crowdfunding, una forma de

financiación colectiva de proyectos a través de Internet.

## (Hueso, 2020)

3

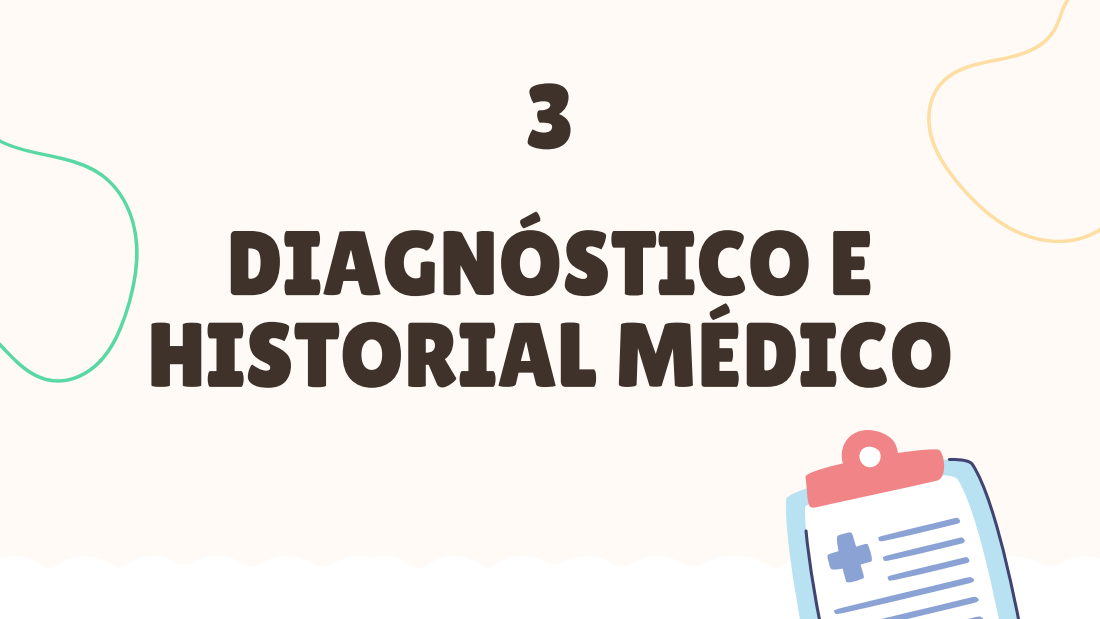
[picture p194: page 11]
DIAGNÓSTICO E HISTORIAL MÉDICO

# diagnóstico e historial médico

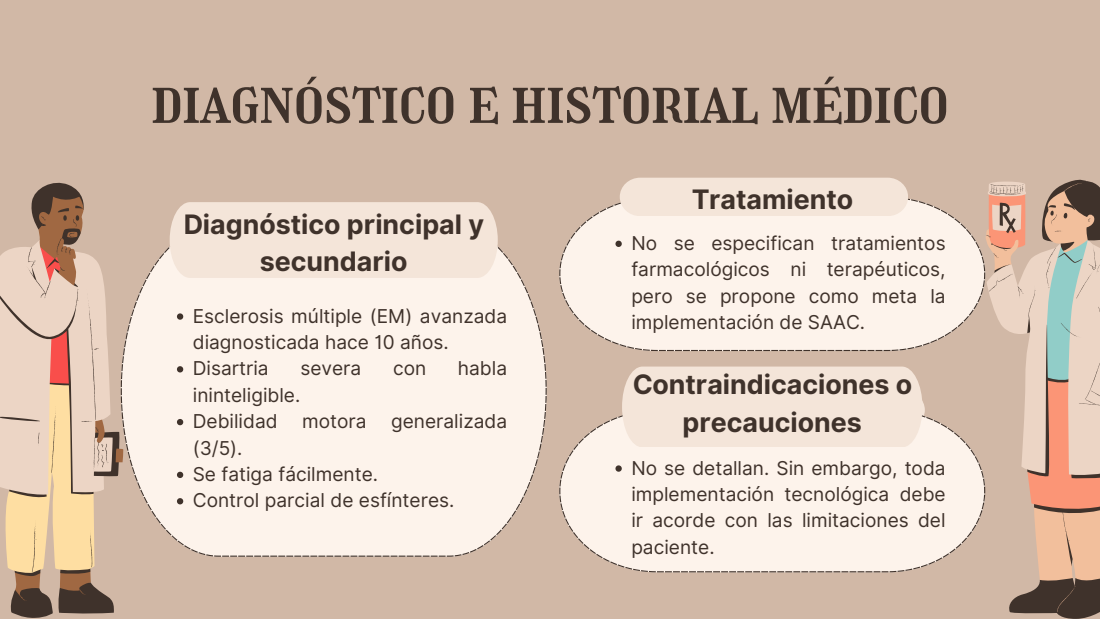
[picture p195: page 12]
Disartria; severa; con; habla; Diagnóstico principal y secundario; Tratamiento

No se especifican tratamientos
farmacológicos ni terapéuticos,
pero se propone como meta la
implementación de SAAC.
Contraindicaciones o
precauciones

Esclerosis múltiple (EM) avanzada
diagnosticada hace 10 años.
ininteligible.
Debilidad motora generalizada
Se fatiga fácilmente.
Control parcial de esfínteres.

No se detallan. Sin embargo, toda
implementación tecnológica debe
ir acorde con las limitaciones del
paciente.

# diagnóstico e historial médico

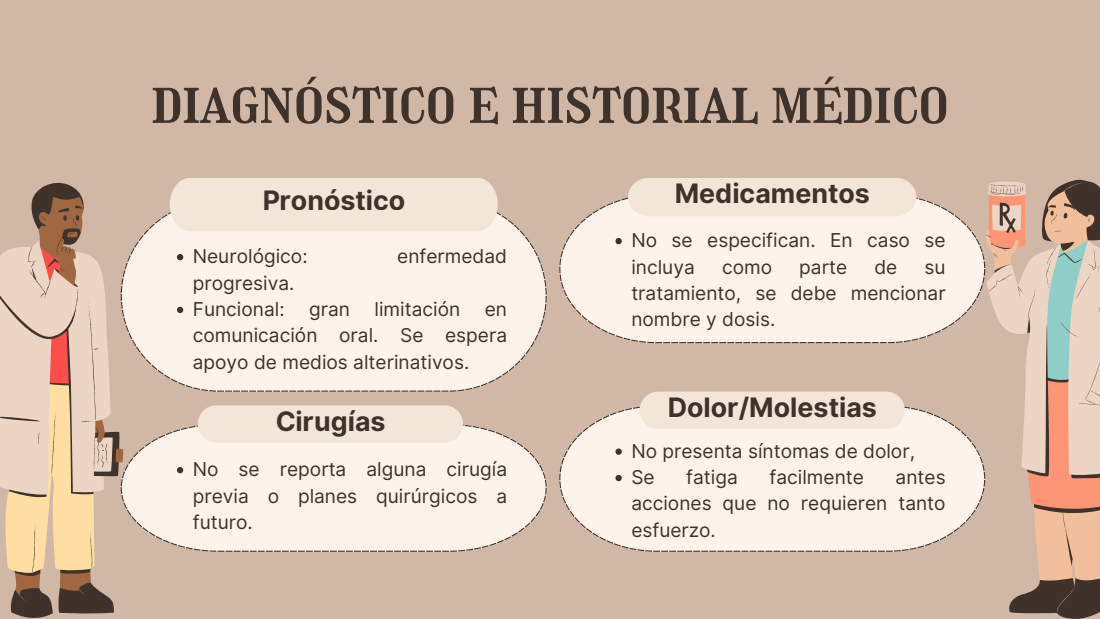
[picture p196: page 13]
Neurológico:; enfermedad; Pronóstico; Medicamentos; fatiga; facilmente; antes; Dolor/Molestias

No se especifican. En caso se
incluya como parte de su
tratamiento, se debe mencionar
nombre y dosis.

progresiva.
Funcional: gran limitación en
comunicación oral. Se espera
apoyo de medios alterinativos.
Cirugías

No presenta síntomas de dolor,
acciones que no requieren tanto
esfuerzo.

No se reporta alguna cirugía
previa o planes quirúrgicos a
futuro.

# diagnóstico e historial médico

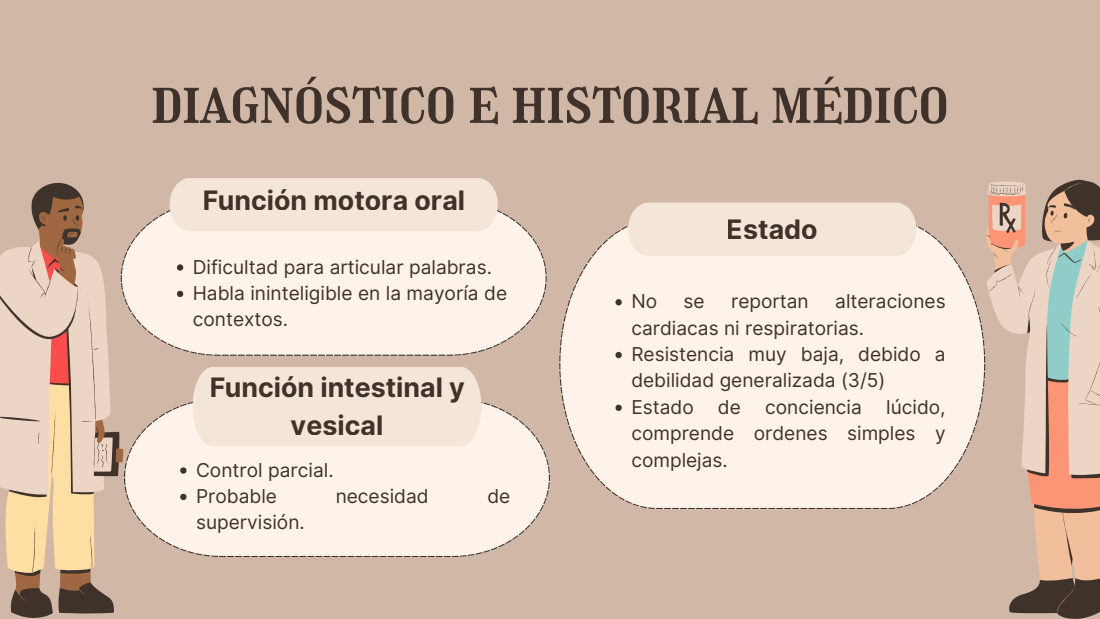
[picture p197: page 14]
Estado; Control parcial.; Probable; necesidad; supervisión.; Función intestinal y vesical

Función motora oral

Dificultad para articular palabras.
Habla ininteligible en la mayoría de
contextos.

No se reportan alteraciones
cardiacas ni respiratorias.
Resistencia muy baja, debido a
debilidad generalizada (3/5)
Estado de conciencia lúcido,
comprende ordenes simples y
complejas.

4

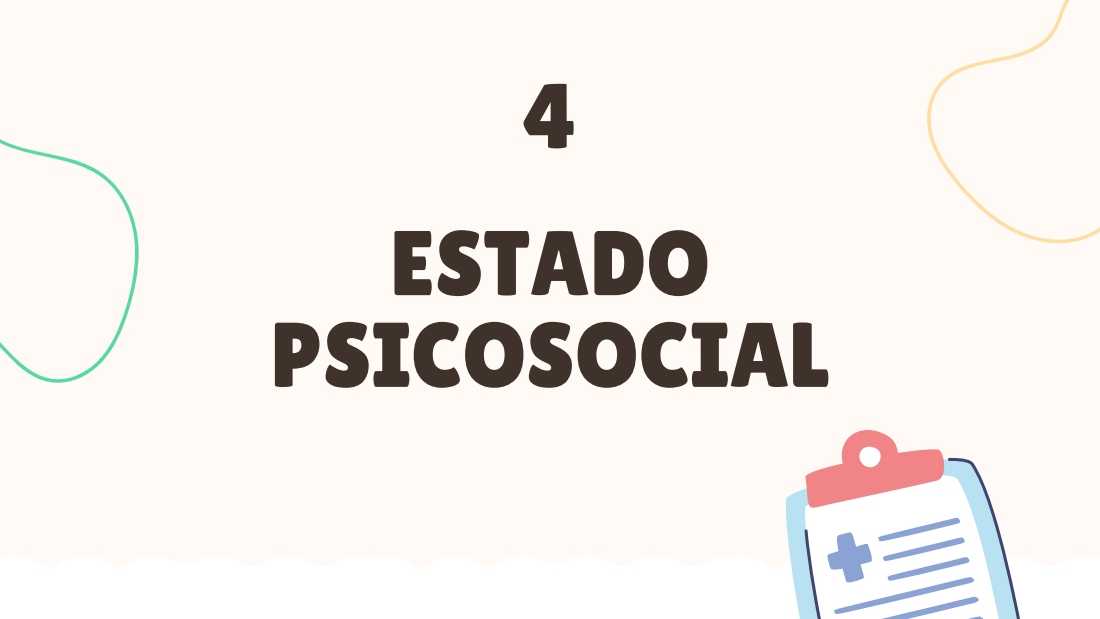
[picture p198: page 15]
ESTADO PSICOSOCIAL

# estado psicosocial

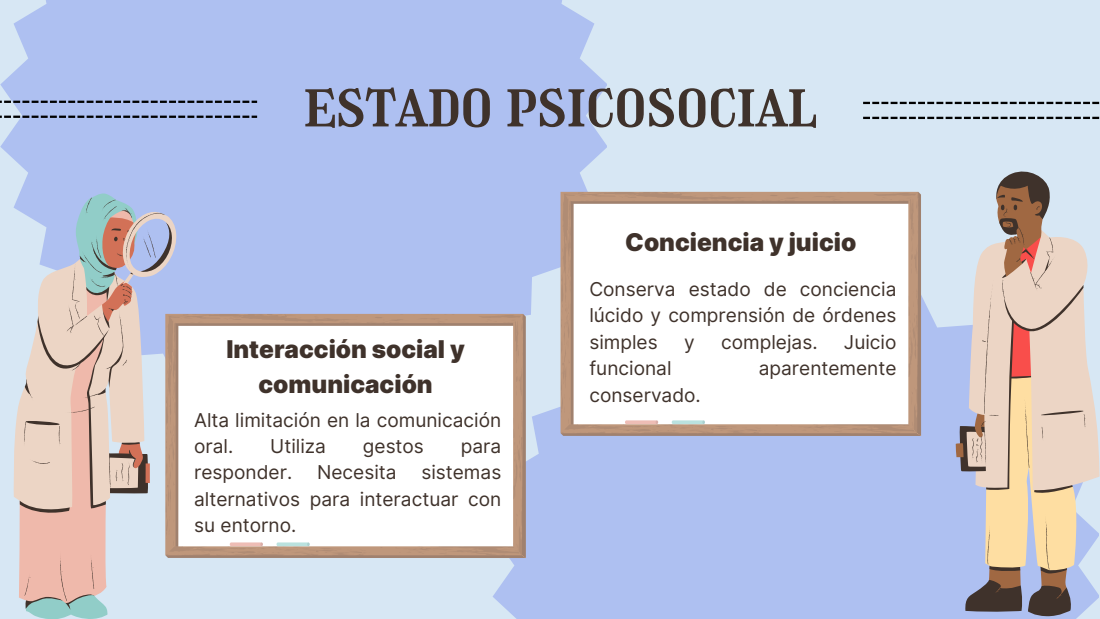
[picture p199: page 16]
funcional; aparentemente

Conciencia y juicio

Conserva estado de conciencia lúcido y comprensión de órdenes simples y complejas. Juicio conservado.

Interacción social y comunicación

Alta limitación en la comunicación oral. Utiliza gestos para responder. Necesita sistemas alternativos para interactuar con su entorno.

# estado psicosocial

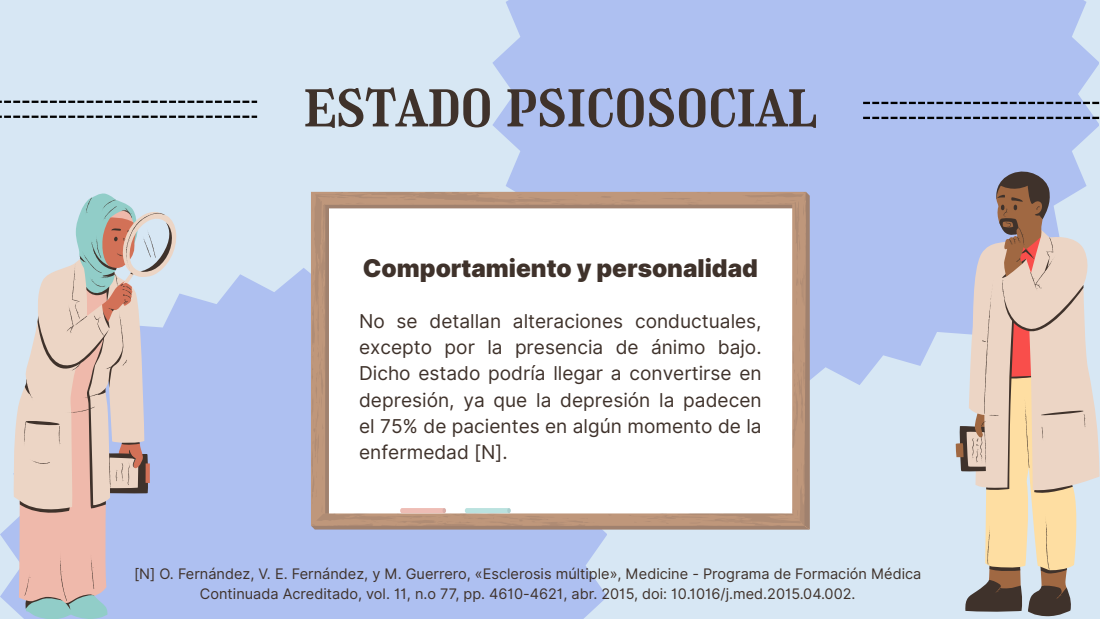
[picture p200: page 17]
excepto por la presencia; de ánimo bajo.; Dicho estado podría llegar; a convertirse en; Comportamiento y personalidad

No se detallan alteraciones conductuales,
depresión, ya que la depresión la padecen
el 75% de pacientes en algún momento de la
enfermedad [N].

[N] O. Fernández, V. E. Fernández, y M. Guerrero, «Esclerosis múltiple», Medicine - Programa de Formación Médica

Continuada Acreditado, vol. 11, n.o 77, pp. 4610-4621, abr. 2015, doi: 10.1016/j.med.2015.04.002.

# estado psicosocial

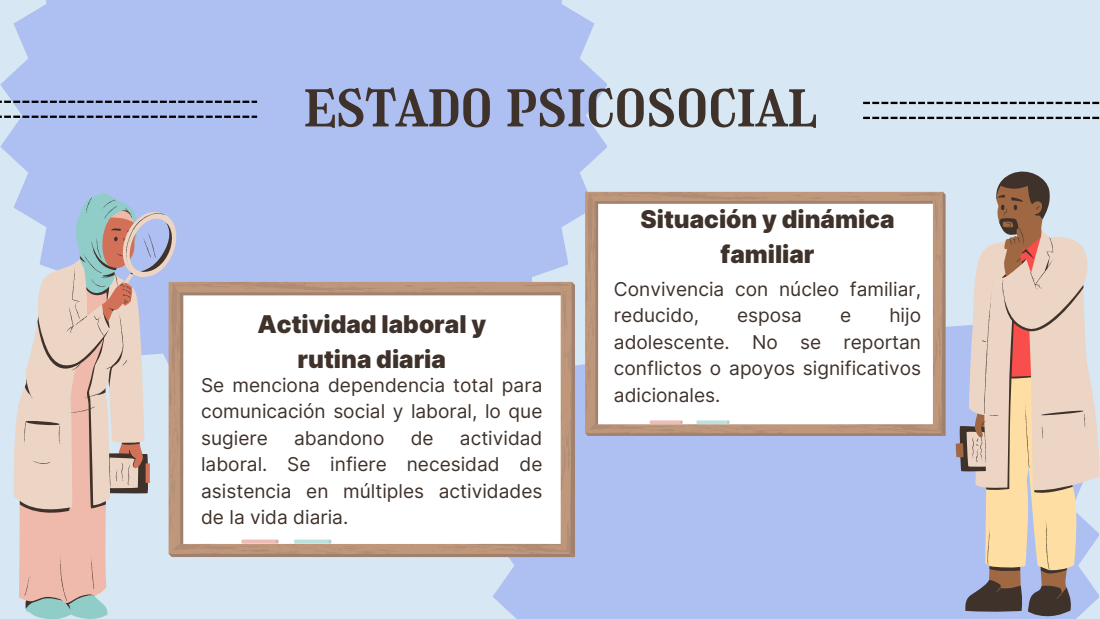
[picture p201: page 18]
reducido,; esposa; hijo; Situación y dinámica familiar

Convivencia con núcleo familiar,
adolescente. No se reportan
conflictos o apoyos significativos
adicionales.

Actividad laboral y rutina diaria Se menciona dependencia total para

comunicación social y laboral, lo que

sugiere abandono de actividad laboral. Se infiere necesidad de asistencia en múltiples actividades de la vida diaria.

5

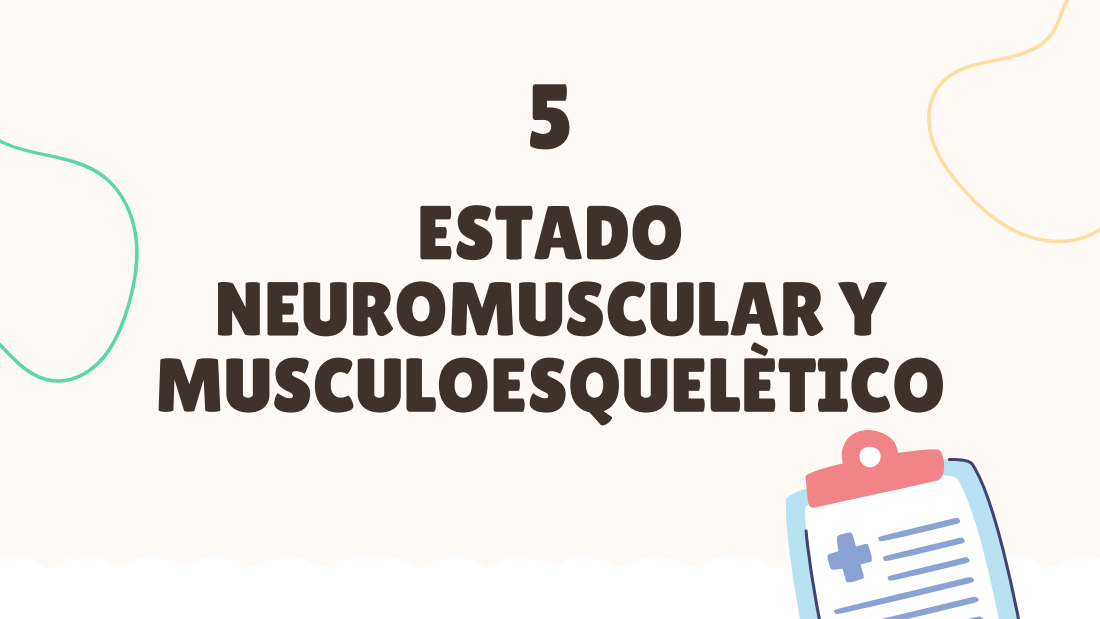
[picture p202: page 19]
ESTADO NEUROMUSCULAR Y MUSCULOESQUELÈTICO

# Articulaciones (ROM y

# Análisis Del Caso

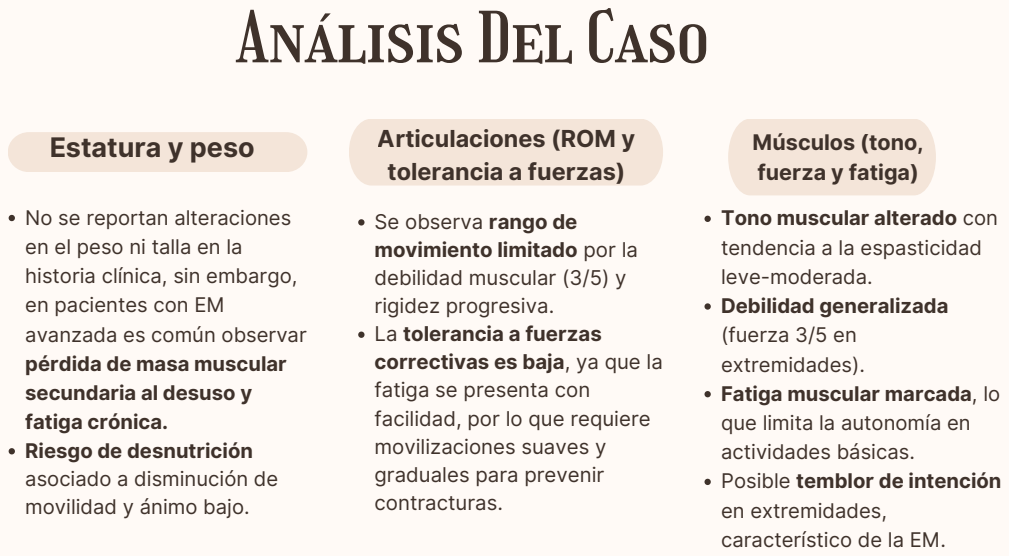
[picture p203: page 20]
Estatura y peso; tolerancia a fuerzas); Músculos (tono, fuerza y fatiga)

No se reportan alteraciones
en el peso ni talla en la
historia clínica, sin embargo,
en pacientes con EM
avanzada es común observar
pérdida de masa muscular
secundaria al desuso y
fatiga crónica.
Riesgo de desnutrición
asociado a disminución de
movilidad y ánimo bajo.

Tono muscular alterado con
tendencia a la espasticidad
leve-moderada.
Debilidad generalizada
(fuerza 3/5 en
extremidades).
Fatiga muscular marcada, lo
que limita la autonomía en
actividades básicas.
Posible temblor de intención
en extremidades,
característico de la EM.

Se observa rango de
movimiento limitado por la
debilidad muscular (3/5) y
rigidez progresiva.
La tolerancia a fuerzas
correctivas es baja, ya que la
fatiga se presenta con
facilidad, por lo que requiere
movilizaciones suaves y
graduales para prevenir
contracturas.

# Influencias

# Postura

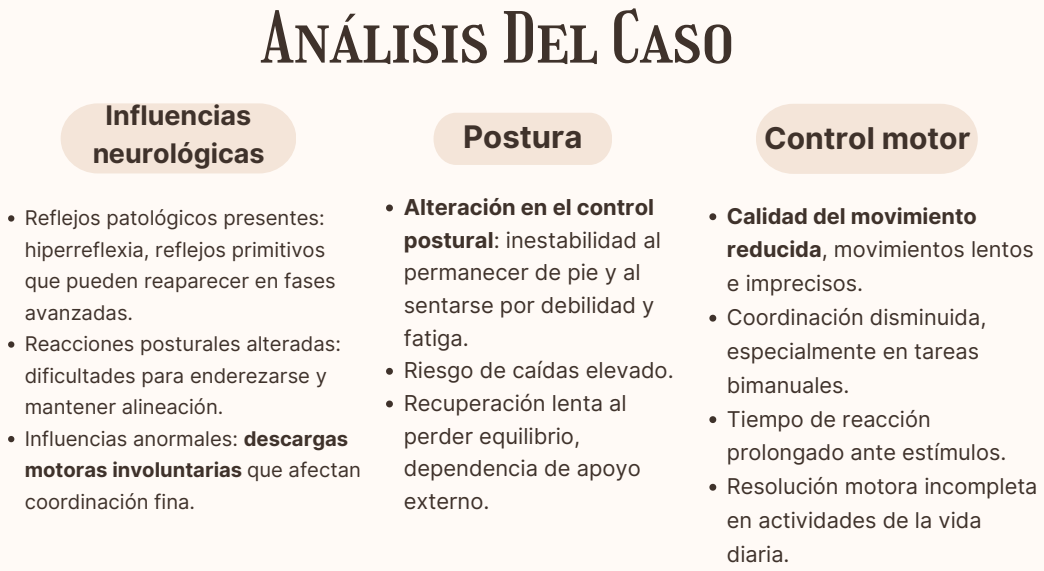
[picture p204: page 21]
neurológicas; Control motor

Análisis Del Caso

Alteración en el control
postural: inestabilidad al
permanecer de pie y al
sentarse por debilidad y
fatiga.
Riesgo de caídas elevado.
Recuperación lenta al
perder equilibrio,
dependencia de apoyo
externo.

Reflejos patológicos presentes:
hiperreflexia, reflejos primitivos
que pueden reaparecer en fases
avanzadas.
Reacciones posturales alteradas:
dificultades para enderezarse y
mantener alineación.
Influencias anormales: descargas
motoras involuntarias que afectan
coordinación fina.

Calidad del movimiento
reducida, movimientos lentos
e imprecisos.
Coordinación disminuida,
especialmente en tareas
bimanuales.
Tiempo de reacción
prolongado ante estímulos.
Resolución motora incompleta
en actividades de la vida
diaria.

# Patrones y estrategias

# Análisis Del Caso

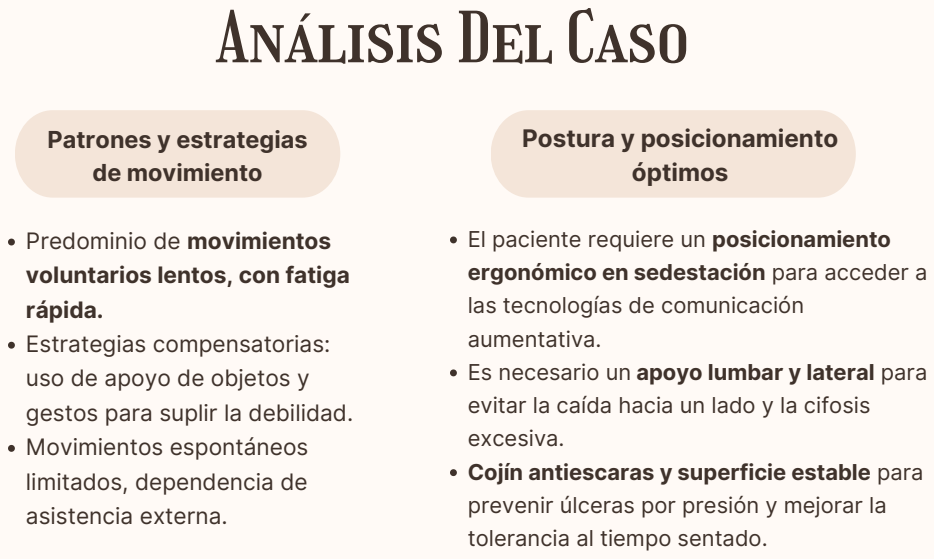
[picture p205: page 22]
de movimiento; Postura y posicionamiento óptimos

Predominio de movimientos
voluntarios lentos, con fatiga
rápida.
Estrategias compensatorias:
uso de apoyo de objetos y
gestos para suplir la debilidad.
Movimientos espontáneos
limitados, dependencia de
asistencia externa.

El paciente requiere un posicionamiento
ergonómico en sedestación para acceder a
las tecnologías de comunicación
aumentativa.
Es necesario un apoyo lumbar y lateral para
evitar la caída hacia un lado y la cifosis
excesiva.
Cojín antiescaras y superficie estable para
prevenir úlceras por presión y mejorar la
tolerancia al tiempo sentado.

# Alineación esquelética y

# evaluación de la sedestación

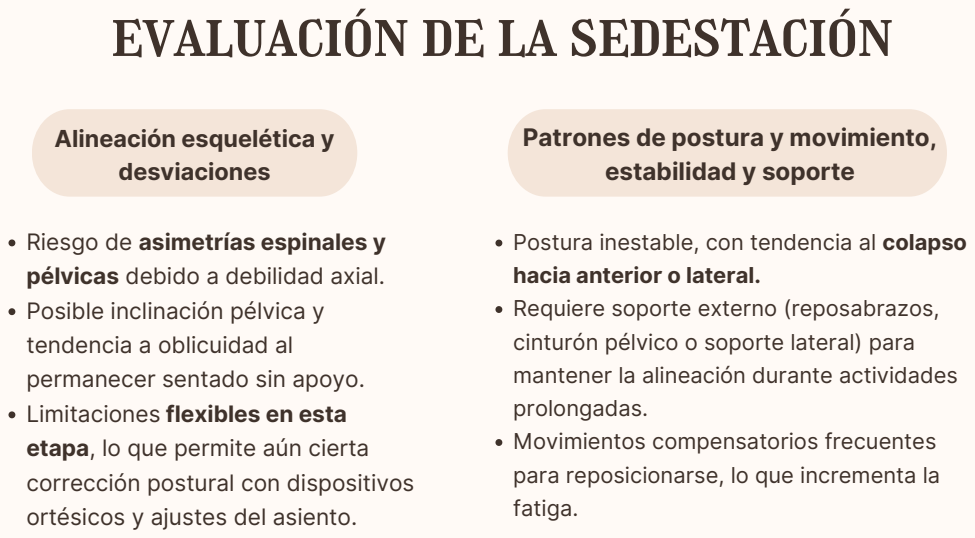
[picture p206: page 23]
desviaciones

Patrones de postura y movimiento,
estabilidad y soporte

Riesgo de asimetrías espinales y
pélvicas debido a debilidad axial.
Posible inclinación pélvica y
tendencia a oblicuidad al
permanecer sentado sin apoyo.
Limitaciones flexibles en esta
etapa, lo que permite aún cierta
corrección postural con dispositivos
ortésicos y ajustes del asiento.

Postura inestable, con tendencia al colapso
hacia anterior o lateral.
Requiere soporte externo (reposabrazos,
cinturón pélvico o soporte lateral) para
mantener la alineación durante actividades
prolongadas.
Movimientos compensatorios frecuentes
para reposicionarse, lo que incrementa la
fatiga.

# La debilidad de tronco y la espasticidad favorecen sobrecargas

en columna y pelvis.

# La fatiga y la incoordinación aumentan la dificultad para mantener la postura, reduciendo la eficiencia

biomecánica.

# Importancia de la intervención fisioterapéutica para optimizar la

función y prevenir deformidades fijas.

# Influencias biomecánicas y kinesiológicas

# evaluación de la sedestación

# El paciente aún presenta potencial para correcciones posturales con adaptaciones externas, siempre que se apliquen de forma

progresiva y bien toleradas.

# La tolerancia es limitada por la fatiga: las correcciones deben ser graduales y

combinadas con períodos de descanso.

# El objetivo es mejorar la estabilidad y

accesibilidad a la comunicación tecnológica,

# más que corregir completamente las

alteraciones.

# Potencial y tolerancia para la corrección

6

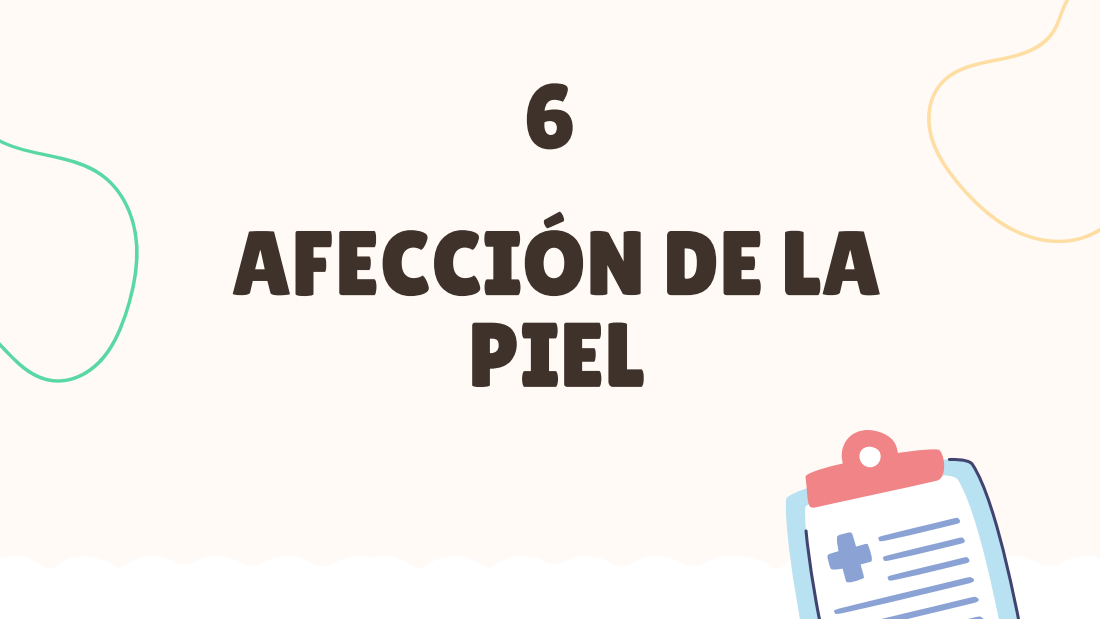
[picture p207: page 25]

AFECCIÓN DE LA
PIEL

# Afección general de la

# Úlceras por

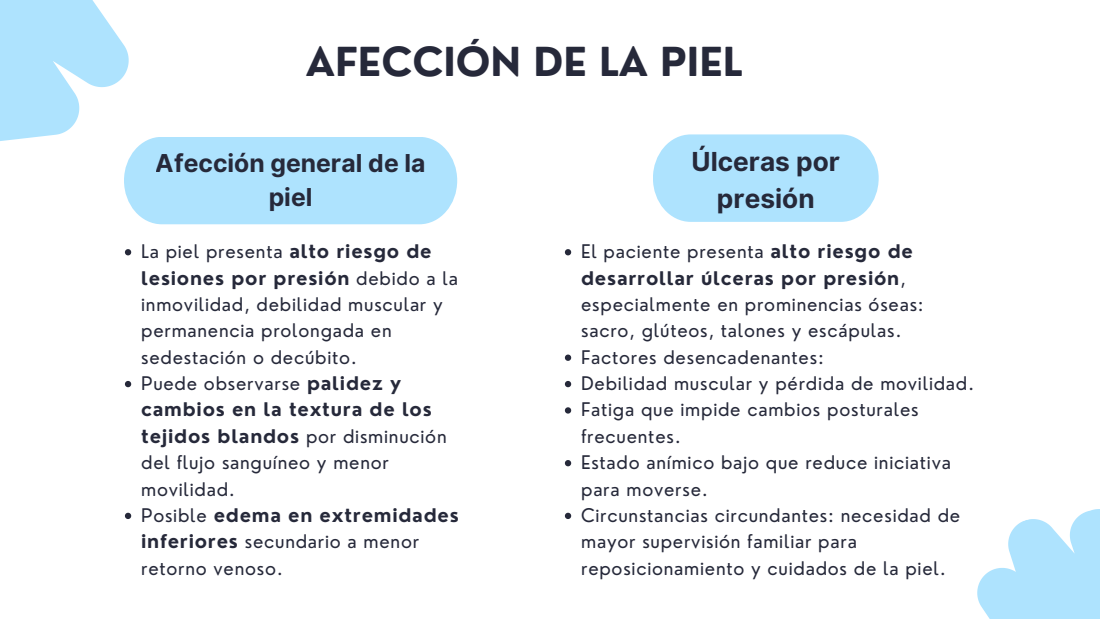
[picture p208: page 26]
piel; presión

AFECCIÓN DE LA PIEL

La piel presenta alto riesgo de
lesiones por presión debido a la
inmovilidad, debilidad muscular y
permanencia prolongada en
sedestación o decúbito.
Puede observarse palidez y
cambios en la textura de los
tejidos blandos por disminución
del flujo sanguíneo y menor
movilidad.
Posible edema en extremidades
inferiores secundario a menor
retorno venoso.

El paciente presenta alto riesgo de
desarrollar úlceras por presión,
especialmente en prominencias óseas:
sacro, glúteos, talones y escápulas.
Factores desencadenantes:
Debilidad muscular y pérdida de movilidad.
Fatiga que impide cambios posturales
frecuentes.
Estado anímico bajo que reduce iniciativa
para moverse.
Circunstancias circundantes: necesidad de
mayor supervisión familiar para
reposicionamiento y cuidados de la piel.

# Tratamiento y

# Riesgos

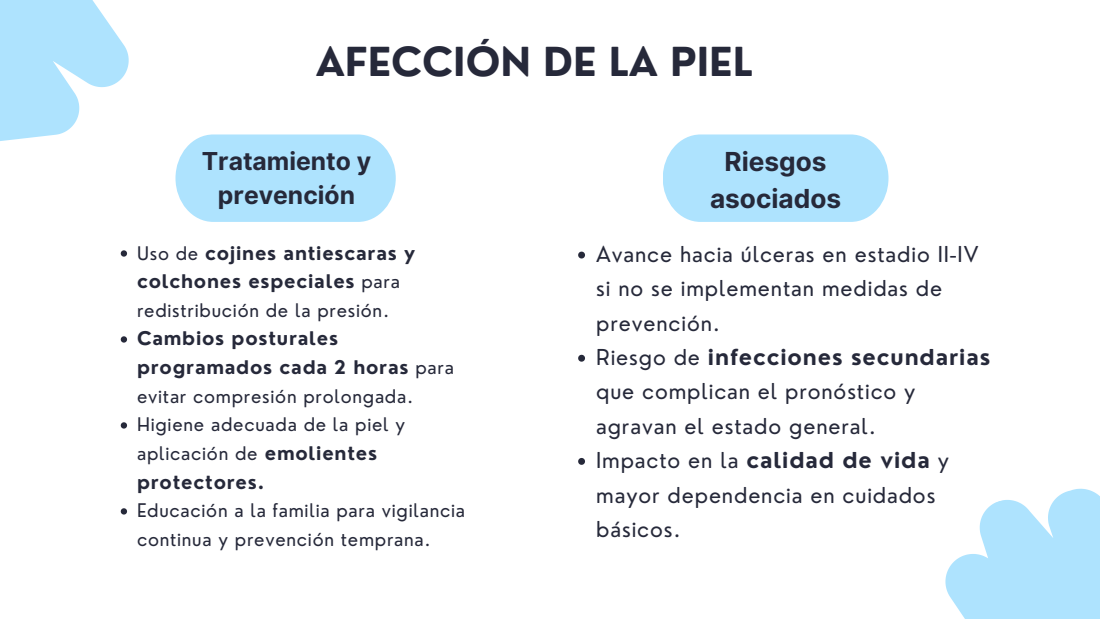
[picture p209: page 27]
prevención; asociados

AFECCIÓN DE LA PIEL

Uso de cojines antiescaras y
colchones especiales para
redistribución de la presión.
Cambios posturales
programados cada 2 horas para
evitar compresión prolongada.
Higiene adecuada de la piel y
aplicación de emolientes
protectores.
Educación a la familia para vigilancia
continua y prevención temprana.

Avance hacia úlceras en estadio II-IV
si no se implementan medidas de
prevención.
Riesgo de infecciones secundarias
que complican el pronóstico y
agravan el estado general.
Impacto en la calidad de vida y
mayor dependencia en cuidados
básicos.

7

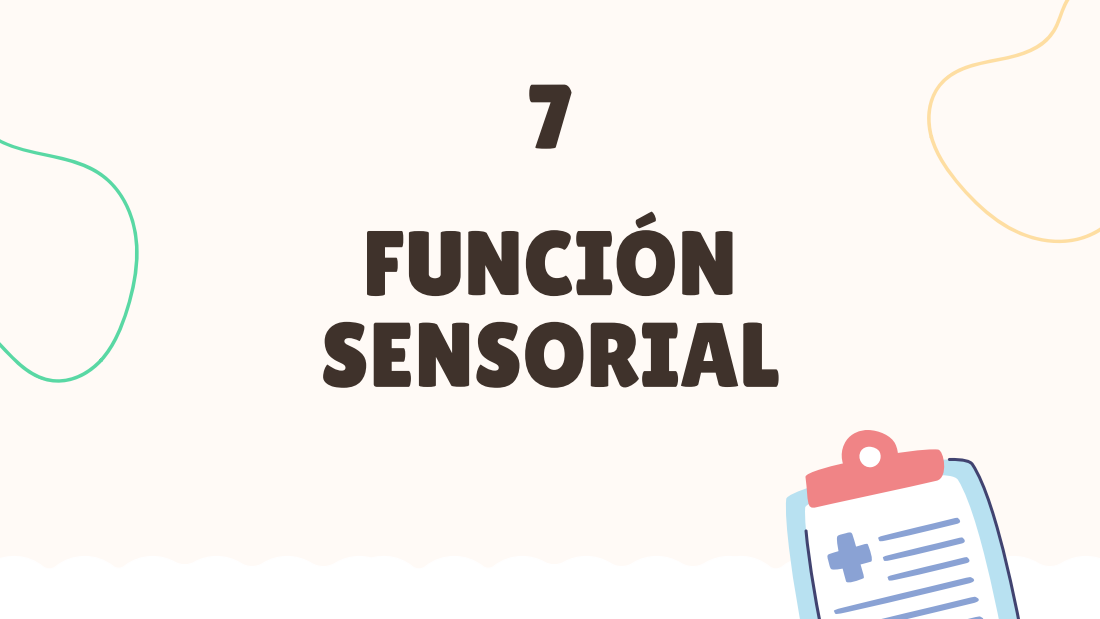
[picture p210: page 28]
FUNCIÓN SENSORIAL

La EM puede afectar la propiocepción y la sensibilidad táctil por lesiones desmielinizantes en médula espinal y nervios periféricos.
Aunque no se describe pérdida sensitiva en este caso, se debe considerar que:
Puede tener disminución de la propiocepción y del sentido kinestésico, lo que afecta la coordinación y aumenta la dependencia en AVD.
El tacto funcional es importante para interactuar con dispositivos (ej. pantallas táctiles, teclados adaptados).
La fatiga y debilidad muscular (3/5) pueden potenciar la dificultad en movimientos finos.

Percepción sensorial: tacto, propiocepción sentido kinestésico.

El paciente comprende órdenes simples y complejas → indica audición funcional conservada.
No se reportan hipoacusia ni tinnitus.
La audición se convierte en un canal sensorial clave para recibir instrucciones terapéuticas y para retroalimentación en estrategias comunicativas.

# Audición

La Esclerosis Múltiple puede generar neuritis óptica y alteraciones visuales (visión borrosa, pérdida de agudeza, diplopía).
En el caso no se reporta déficit visual, por lo que asumimos que mantiene visión funcional suficiente para actividades básicas y para la interacción con SAAC visuales (pictogramas, pantallas, tablets). Es importante valorar periódicamente la agudeza y el campo visual, ya que la progresión puede limitar el uso de sistemas de comunicación basados en estímulos visuales.

Visión (visión funcional, agudeza,

# percepción visual)

Si la visión está conservada, es un punto fuerte para la implementación de tecnologías visuales de comunicación (pictogramas, escritura, lectura de pantalla).

La audición preservada permite el uso de apoyos auditivos en la rehabilitación, como instrucciones verbales, aplicaciones con retroalimentación sonora, o sistemas de comunicación con salida de voz.

Si el tacto fino está limitado, conviene prever accesos alternativos a la tecnología (pulsadores grandes, sistemas de eye-tracking, interfaces por voz o audición).

## 👉 Considerar

## 👉 Considerar

## 👉 Considerar

7

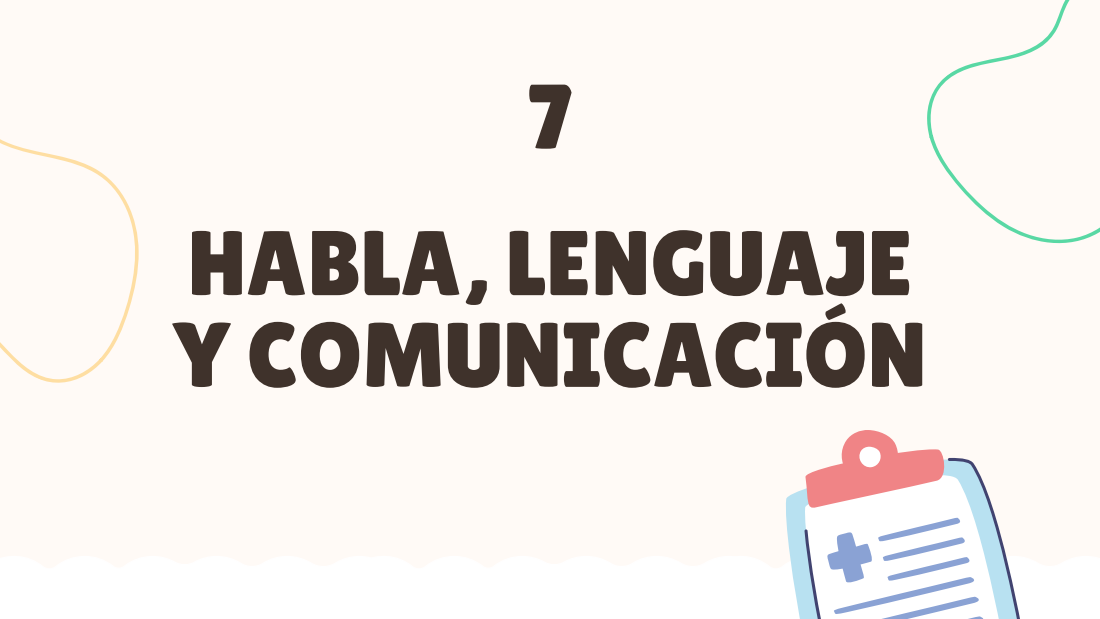
[picture p211: page 30]
HABLA, LENGUAJE Y COMUNICACIÓN

Disartria severa: Dificultad en la articulación, ritmo y entonación.
Puede mantener cierta inteligibilidad en palabras clave, lo que se puede entrenar en logopedia como recurso de emergencia para comunicación básica (ej. “sí”, “no”, “dolor”).
Pronóstico: debido a la progresión de la EM, la inteligibilidad tenderá a disminuir, por lo que los SAAC se vuelven prioritarios.

# Habla y articulación

Receptivo (comprensión): Conservado. El paciente comprende órdenes simples y complejas, lo que permite mantener interacción social y seguir instrucciones terapéuticas.
Expresivo (emisión): Severamente afectado. Su habla es ininteligible en la mayoría de contextos, lo que genera gran limitación comunicativa y dependencia de terceros para expresarse. Implicancia clínica: Se requiere implementar SAAC (sistemas aumentativos y alternativos de comunicación), ya que el canal oral está muy deteriorado.

# Capacidad de lenguaje expresivo y receptivo

### Área de comprensión

### Área de expresión

### Paciente en terapia de logopedia

No se reporta experiencia previa con dispositivos.
Debido a su comprensión preservada y motivación familiar, es candidato para dispositivos generadores de habla o software de comunicación (ejemplo: aplicaciones en tablets con pictogramas, texto a voz, teclados adaptados).
Se debe valorar accesibilidad: uso de manos limitado por debilidad (3/5) → podría requerir acceso por pulsadores, pantallas táctiles adaptadas o incluso control ocular (eye-tracking) si la progresión lo amerita.

# Uso y experiencia con dispositivos generadores de habla

Conciencia y cognición: Lúcido, con buena comprensión → puede aprender y adaptarse a estrategias de comunicación alternativa. Atención y aprendizaje: Se encuentran preservados, aunque la fatiga puede limitar la duración de las sesiones.
Educación: No se menciona, pero a los 52 años es funcionalmente independiente en comprensión de conceptos y estrategias de comunicación.

Nivel cognitivo, aprendizaje,

# atención, estado educativo

### Tableta con pictogramas

### Paciente usando un Ipad pensando

8

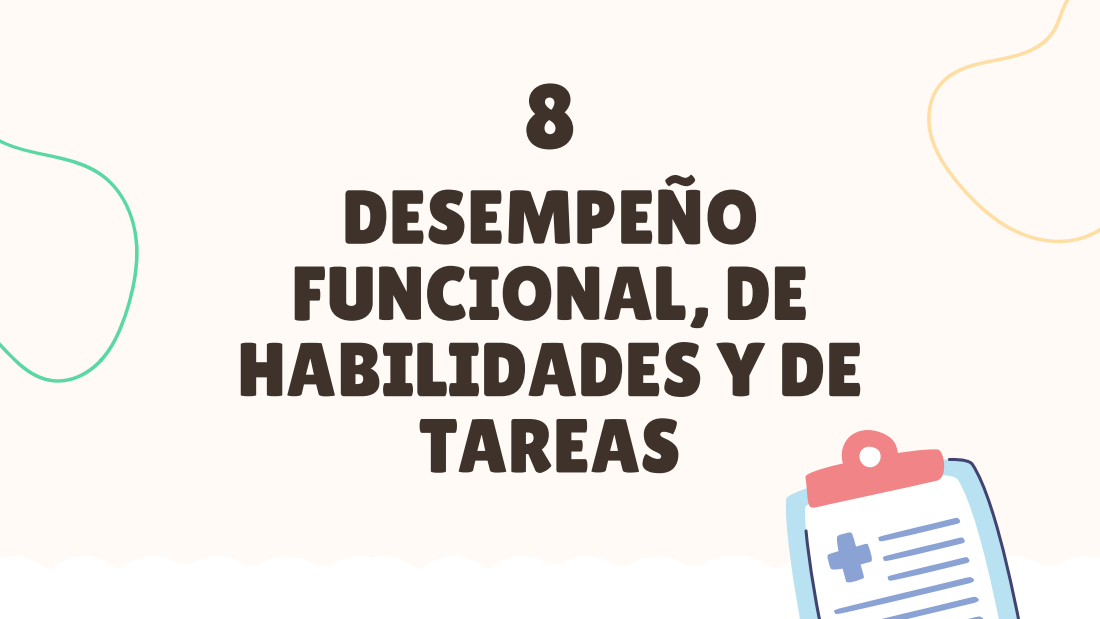
[picture p212: page 33]
DESEMPEÑO FUNCIONAL, DE HABILIDADES Y DE TAREAS

## Necesita asistencia moderada para la comunicación (dependiente de

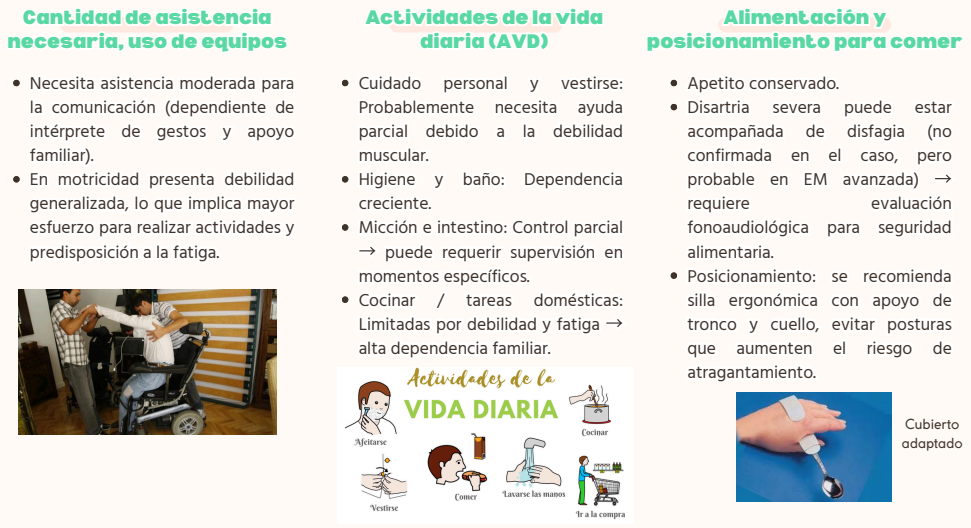
[picture p213: page 34]
Apetito conservado.; Disartria severa; puede estar; requiere; evaluación; Alimentación y; Cubierto adaptado

Cantidad de asistencia
necesaria, uso de equipos
Necesita asistencia moderada para
la comunicación (dependiente de
intérprete de gestos y apoyo
familiar).
En motricidad presenta debilidad
generalizada, lo que implica mayor
esfuerzo para realizar actividades y
predisposición a la fatiga.

Actividades de la vida
diaria (AVD)
Cuidado personal y vestirse:
Probablemente necesita ayuda
parcial debido a la debilidad
muscular.
Higiene y baño: Dependencia
creciente.
Micción e intestino: Control parcial
→ puede requerir supervisión en
momentos específicos.
Cocinar / tareas domésticas:
Limitadas por debilidad y fatiga →
alta dependencia familiar.

posicionamiento para comer
Apetito conservado.
Disartria severa puede estar
acompañada de disfagia (no
confirmada en el caso, pero
probable en EM avanzada) →
fonoaudiológica para seguridad
alimentaria.
Posicionamiento: se recomienda
silla ergonómica con apoyo de
tronco y cuello, evitar posturas
que aumenten el riesgo de
atragantamiento.

## Paciente de 52 años, con dependencia comunicativa y

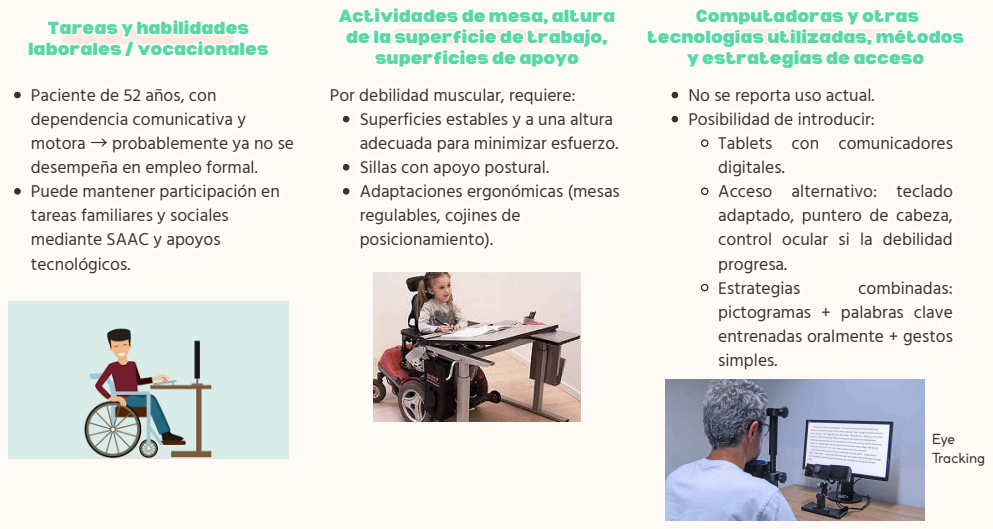
[picture p214: page 35]
Estrategias; combinadas:; Eye Tracking

Actividades de mesa, altura
de la superficie de trabajo,
superficies de apoyo
Por debilidad muscular, requiere:
Superficies estables y a una altura
adecuada para minimizar esfuerzo.
Sillas con apoyo postural.
Adaptaciones ergonómicas (mesas
regulables, cojines de
posicionamiento).

Computadoras y otras
tecnologías utilizadas, métodos
y estrategias de acceso
No se reporta uso actual.
Posibilidad de introducir:
Tablets con comunicadores
digitales.
Acceso alternativo: teclado
adaptado, puntero de cabeza,
control ocular si la debilidad
progresa.
pictogramas + palabras clave
entrenadas oralmente + gestos
simples.

Tareas y habilidades
laborales / vocacionales
Paciente de 52 años, con
dependencia comunicativa y
motora → probablemente ya no se
desempeña en empleo formal.
Puede mantener participación en
tareas familiares y sociales
mediante SAAC y apoyos
tecnológicos.

9

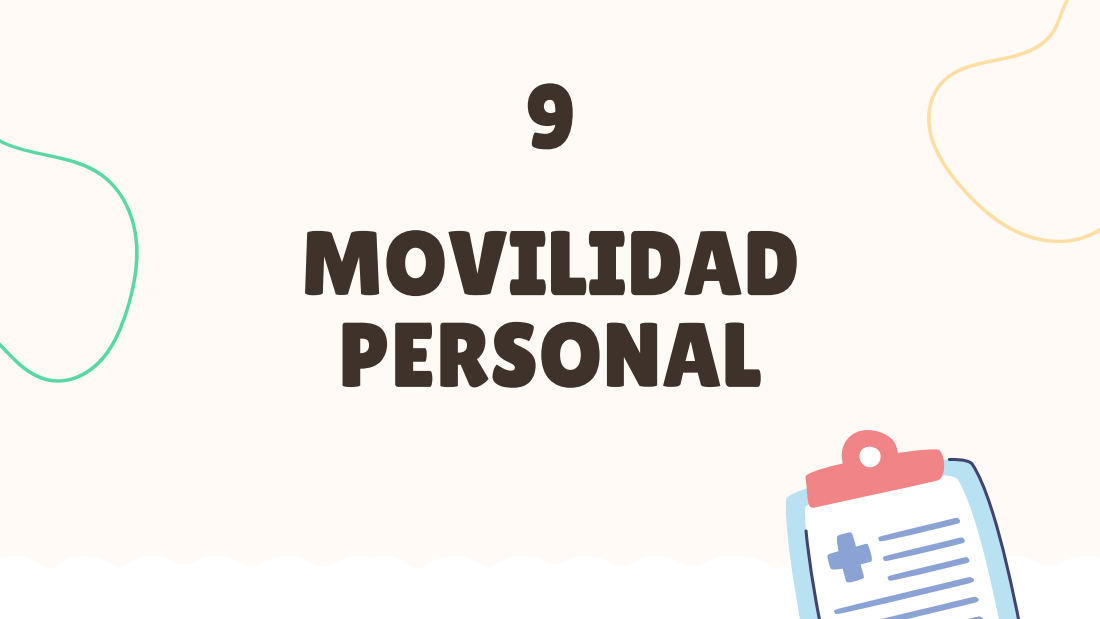
[picture p215: page 36]
MOVILIDAD PERSONAL

Ambulación | Traslados | Uso de silla de ruedas

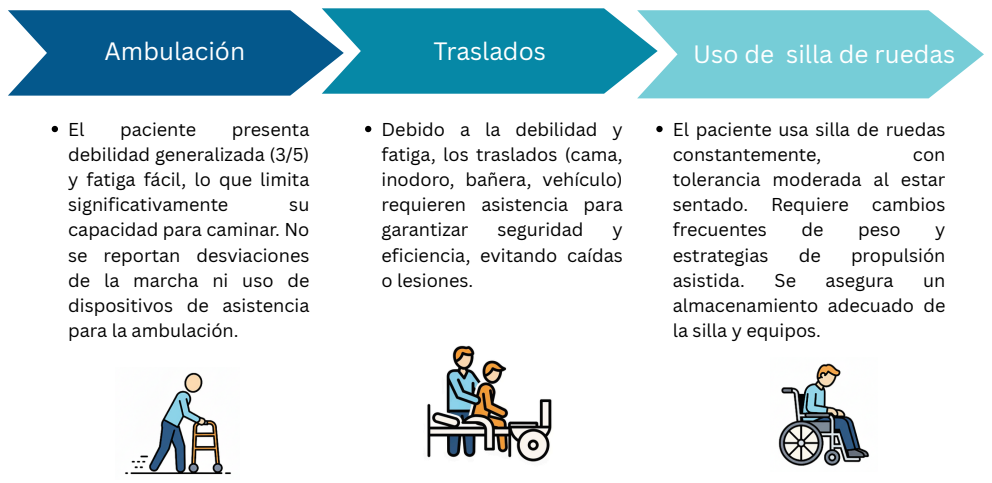
[picture p216: page 37]
garantizar; seguridad; paciente; presenta; significativamente; constantemente,; con; frecuentes; peso; estrategias; propulsión; asistida.; asegura

debilidad generalizada (3/5)
y fatiga fácil, lo que limita
capacidad para caminar. No
se reportan desviaciones
de la marcha ni uso de
dispositivos de asistencia
para la ambulación.

Debido a la debilidad y
fatiga, los traslados (cama,
inodoro, bañera, vehículo)
requieren asistencia para
eficiencia, evitando caídas
o lesiones.

El paciente usa silla de ruedas
tolerancia moderada al estar
sentado. Requiere cambios
almacenamiento adecuado de
la silla y equipos.

10

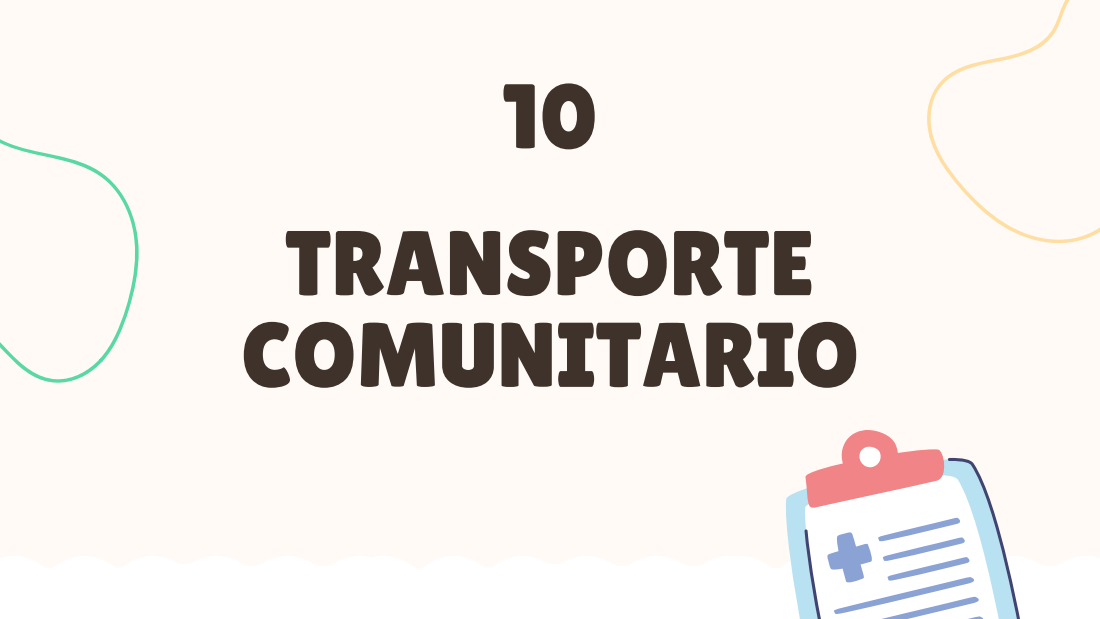
[picture p217: page 38]
TRANSPORTE COMUNITARIO

# Viaje en silla de ruedas en vehículo en movimiento:

o. Vehículos utilizados: Entrada y salida: | Almace

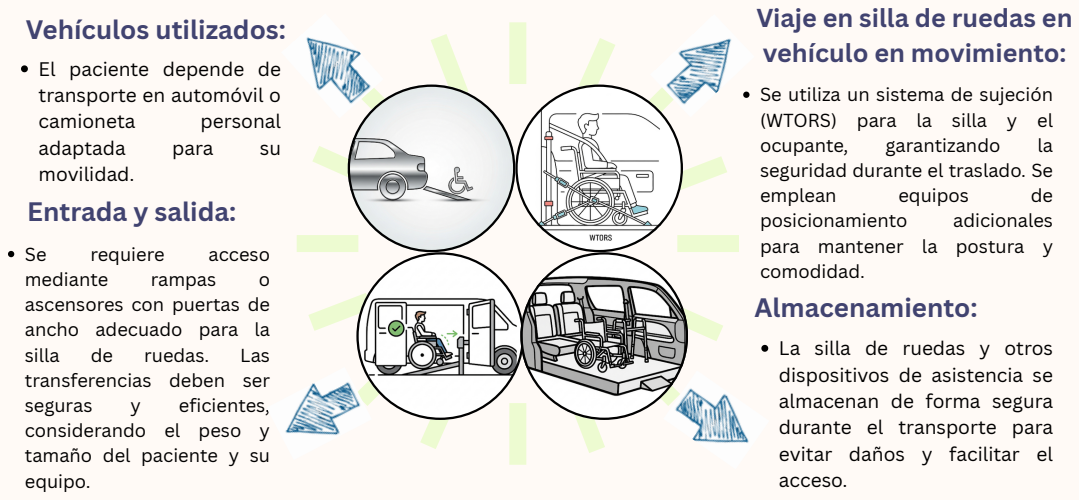
[picture p218: page 39]
requiere; acceso; rampas; silla; ruedas.; Las; seguras; eficien; tes; equipo.; sil; dis; sitiv; sis; cia; vit; cilit; cie; vil; mio; vilid; garantizando; emplean; equipos; adicionales

Se utiliza un sistema de sujeción
(WTORS) para la silla y el
ocupan
seguridad duran
posicionamien
para man
comodidad.

te el traslado. Se

tener la postura

median
ascensores con puertas de
ancho adecuado para la
transferencias deben ser

considerando el peso
tamaño del pacien

9

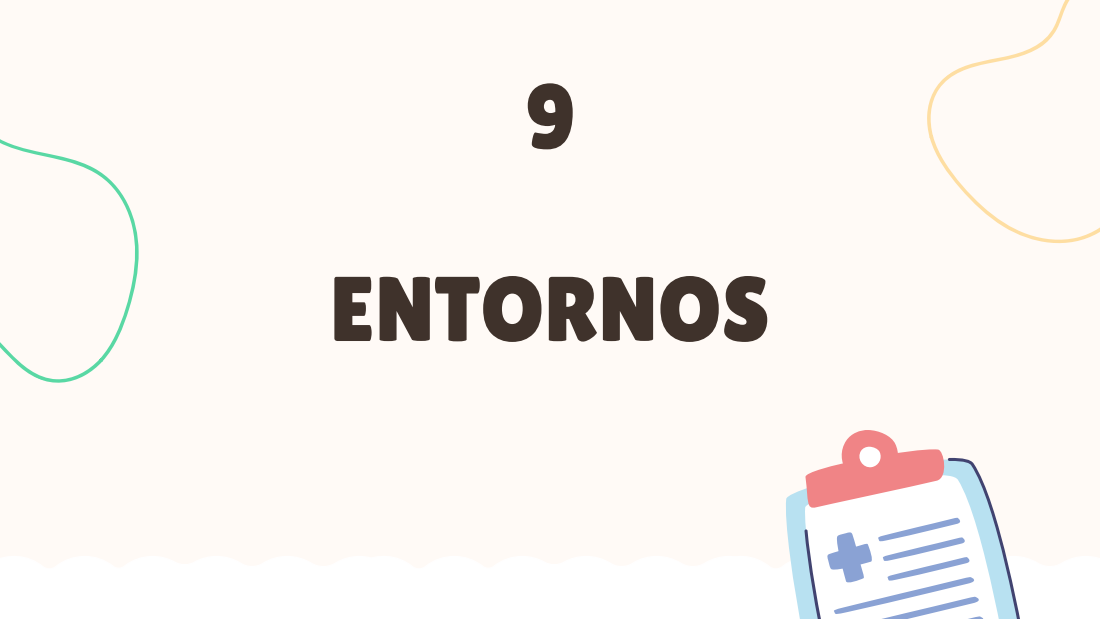
[picture p219: page 40]
ENTORNOS

## Viv

e

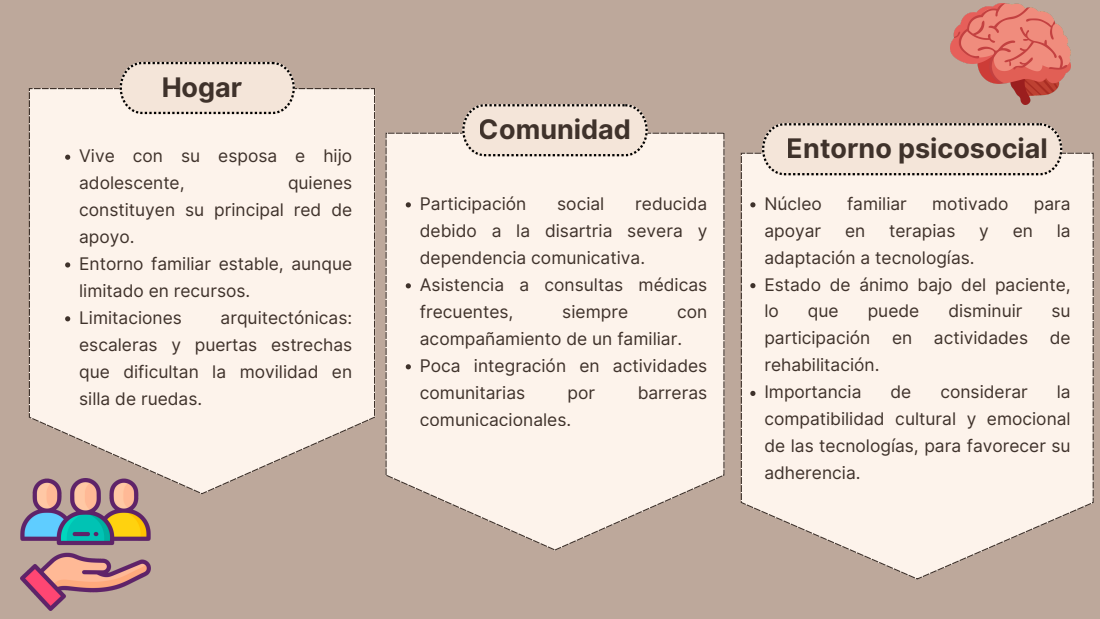
[picture p220: page 41]
hij; ole; uie; tit; rin; cip; o. Entorn o; milia; ble; e limitado en recursos. Limitaciones; arquitectónicas: escaleras y puertas estrechas que dificultan la movilidad en silla de ruedas. Hogar; Participa; cle; tiv; pia; ció; olo; cie; que; puede; disminuir; su participación en actividades de rehabilitación. Importancia; considerar; la compatibilidad cultural y emocional de las tecnologías, para favorecer su adherencia. Entorno psicosocial

s. Estado de ánimo bajo del p

12

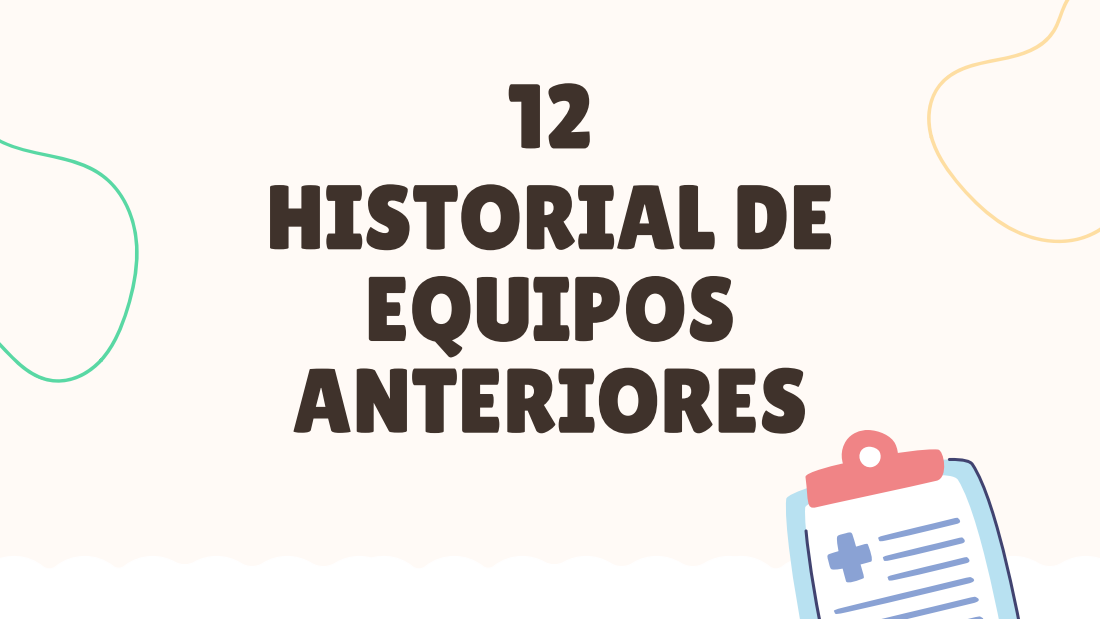
[picture p221: page 42]
HISTORIAL DE EQUIPOS ANTERIORES

# Estrategias previas de

# Resultados

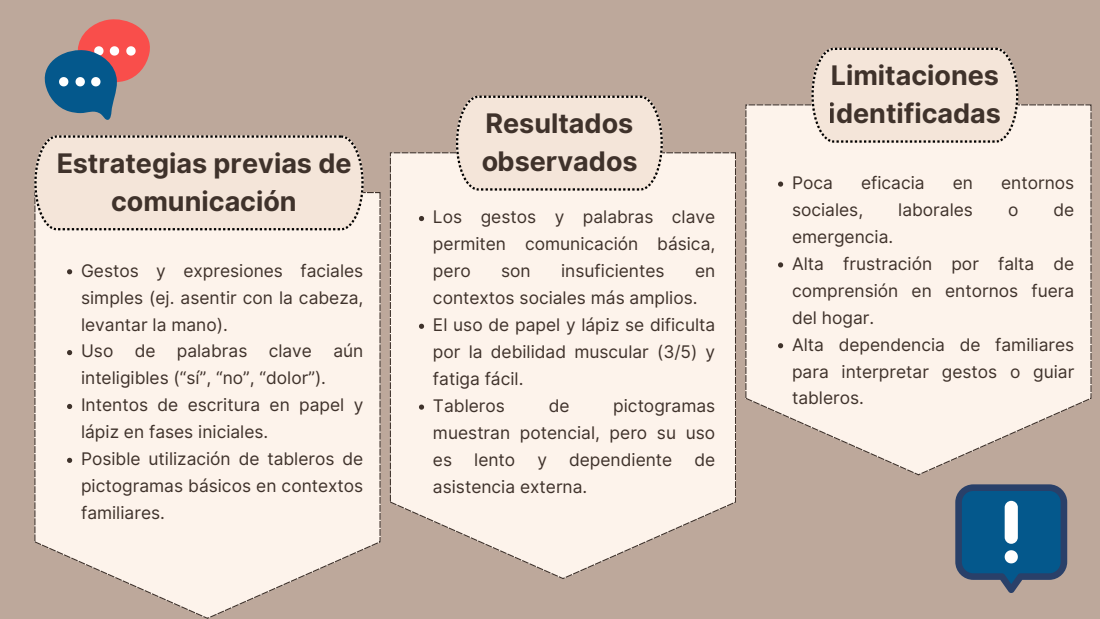
[picture p222: page 43]
“dolor”).; pero; son; insuficientes; Tableros; pictogramas; Poca; eficacia; entornos; sociales,; laborales; Limitaciones identificadas

observados

emergencia.
Alta frustración por falta de
comprensión en entornos fuera
del hogar.
Alta dependencia de familiares
para interpretar gestos o guiar
tableros.

comunicación

Los gestos y palabras clave
permiten comunicación básica,
contextos sociales más amplios.
El uso de papel y lápiz se dificulta
por la debilidad muscular (3/5) y
fatiga fácil.
muestran potencial, pero su uso
es lento y dependiente de
asistencia externa.

Gestos y expresiones faciales
simples (ej. asentir con la cabeza,
levantar la mano).
Uso de palabras clave aún
inteligibles (“sí”
Intentos de escritura en papel y
lápiz en fases iniciales.
Posible utilización de tableros de
pictogramas básicos en contextos
familiares.

13

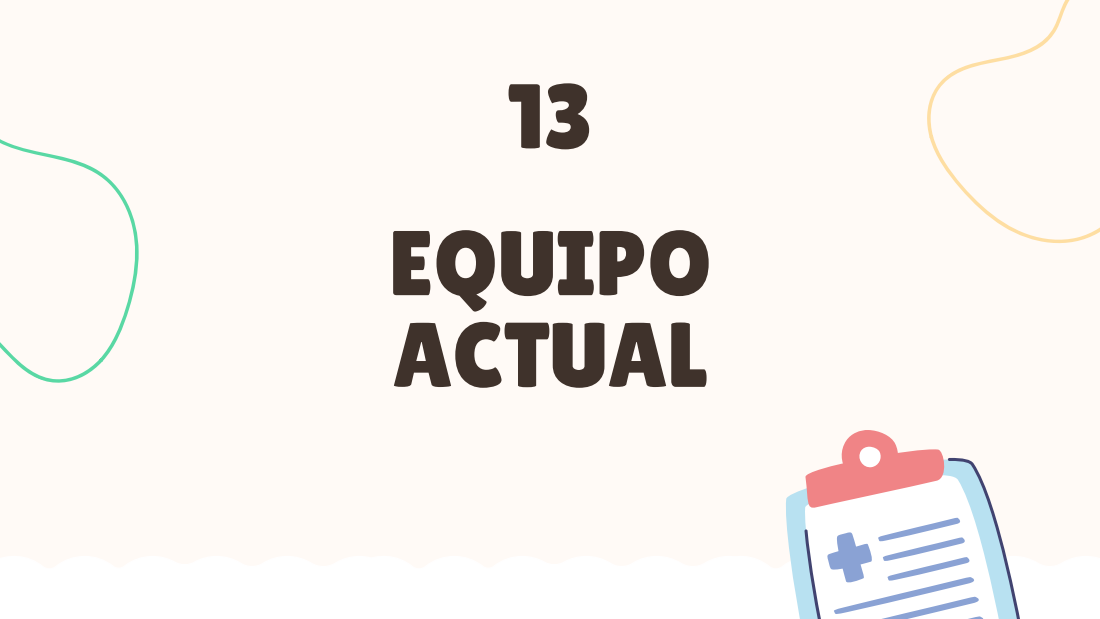
[picture p223: page 44]
EQUIPO ACTUAL

MODELO, ESTILO, MARCA, NÚMERO DE SERIE | CARACTERÍSTICAS, COMPONENTES, PESO, DIMENSIONES | OBJETIVOS Y JUSTIFICACIÓN PARA ELEGIR ESTA TECNOLOGÍA
El paciente actualmente utiliza: Silla de ruedas manual estándar (sin adaptaciones electrónicas, modelo básico, marca genérica). Tablet con software de comunicación aumentativa (SAAC) basado en pictogramas (ejemplo: Grid 3 o Proloquo2Go), con soporte fijo para mesa. No cuenta con pulsadores ni sistemas oculares. | Tablet: ligera, portátil (10 pulgadas, ~500 g), pantalla táctil, requiere precisión en la pulsación. Software SAAC: pictogramas personalizables, salida de voz artificial. Silla de ruedas: 15 kg, plegable, sin motor, necesita asistencia de cuidador | Tablet con SAAC: principal medio de comunicación, compensa la disartria severa, permite expresar necesidades básicas. Silla de ruedas: facilita movilidad y transporte dentro y fuera del hogar. Ambas tecnologías buscan favorecer la independencia, reducir frustración y mantener interacción familiar.

## VIDA ÚTIL RESTANTE PREVISTA DE LA

TECNOLOGÍA (ANTIGÜEDAD, ESTADO,

## HISTORIAL DE REPARACIONES)

## GUSTOS, DISGUSTOS E INQUIETUDES DEL CLIENTE Y DEL CUIDADOR

EFICACIA FUNCIONAL DEL EQUIPO ACTUAL,

## EQUIPO UTILIZADO CORRECTAMENTE

Tablet: antigüedad ~3 años, batería con desgaste moderado, requiere actualización de software en el corto plazo.
Silla de ruedas: 5 años de uso, estructura estable, pero ruedas muestran desgaste.
Estado general: funcional pero con necesidad de mantenimiento preventivo.

Paciente: le gusta la facilidad de uso de la tablet, pero se frustra cuando no puede seleccionar pictogramas pequeños debido a la debilidad motora.
Esposa/cuidadora: valora el apoyo del SAAC, pero le preocupa la dependencia tecnológica y posibles fallos de batería.
Inquietud: costo de reemplazo o actualización de equipos.

Tablet SAAC: eficaz para necesidades básicas, pero limitada para conversaciones complejas. Uso correcto en la mayoría de situaciones.
Silla de ruedas: funcional, pero dependencia total de otra persona para desplazamientos prolongados.
En general, los equipos cumplen parcialmente con la meta de independencia, pero requieren adaptaciones y mejoras (ej. pulsadores grandes, soporte ocular, silla eléctrica).

NOTA: Al no haber datos específicos sobre el equipo actual, nos hemos basado en otros casos clínicos de pacientes con EM para complementar la información presentada del paciente y generalizar algunas de sus circunstancias.
