AlessandroCrosby/GRUPO2/ENTREGABLES/ENTREGABLES SEMANA N°4/PPT DEL ENTREGABLE N°4.pdf

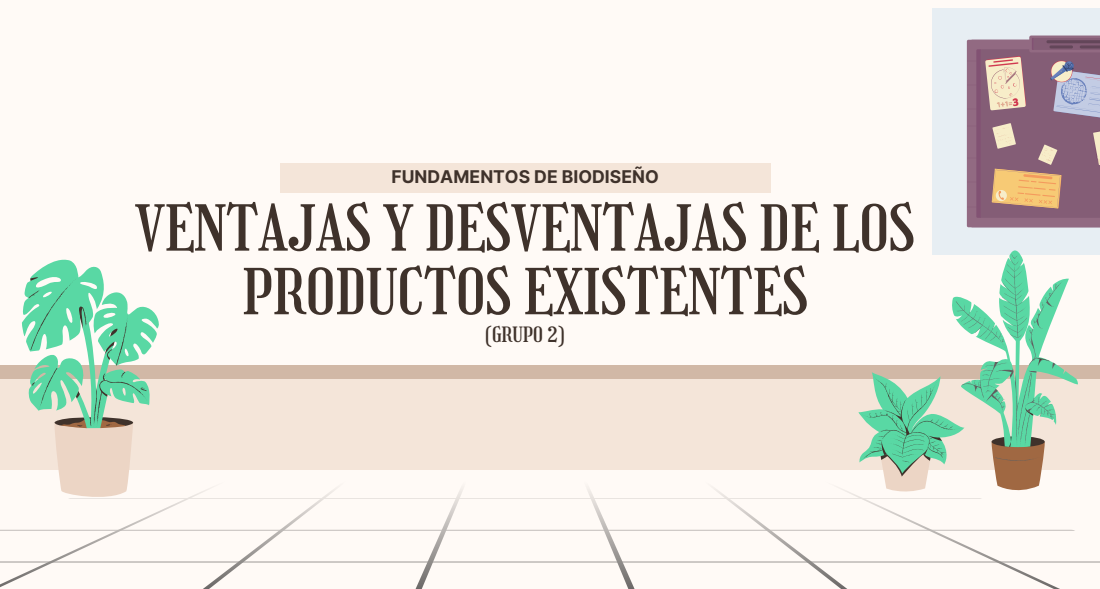
[picture p224: page 1]
(GRUPO 2)

FUNDAMENTOS DE BIODISEÑO
PRODUCTOS EXISTENTES

VENTAJAS Y DESVENTAJAS DE LOS

1

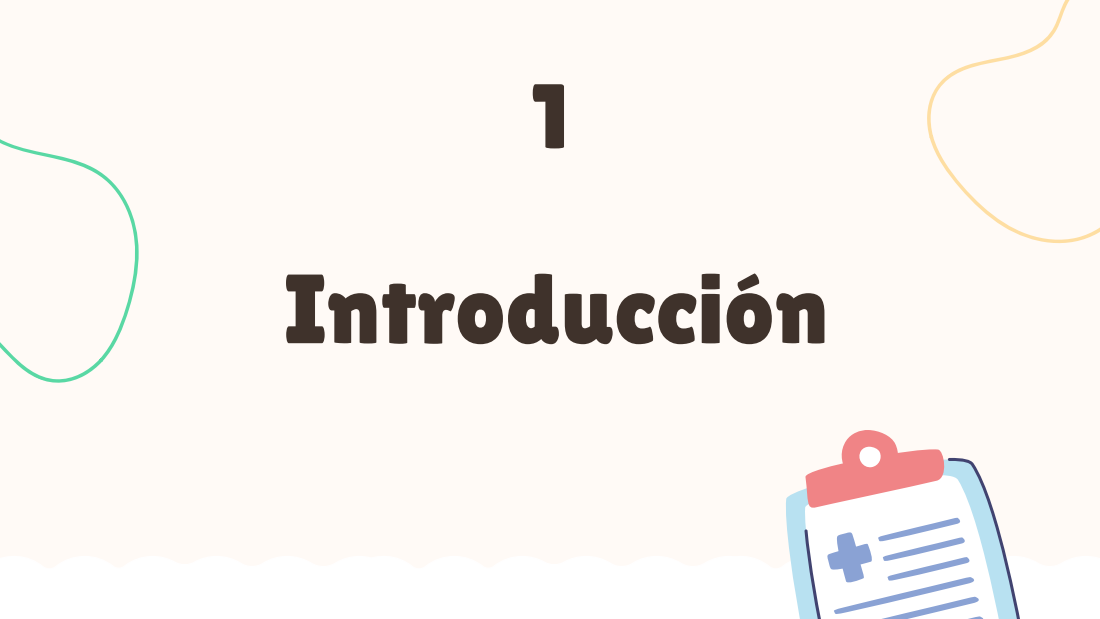
[picture p225: page 2]
Introducción

# Necesidad crítica del paciente

## Situación clínica y desafío principal

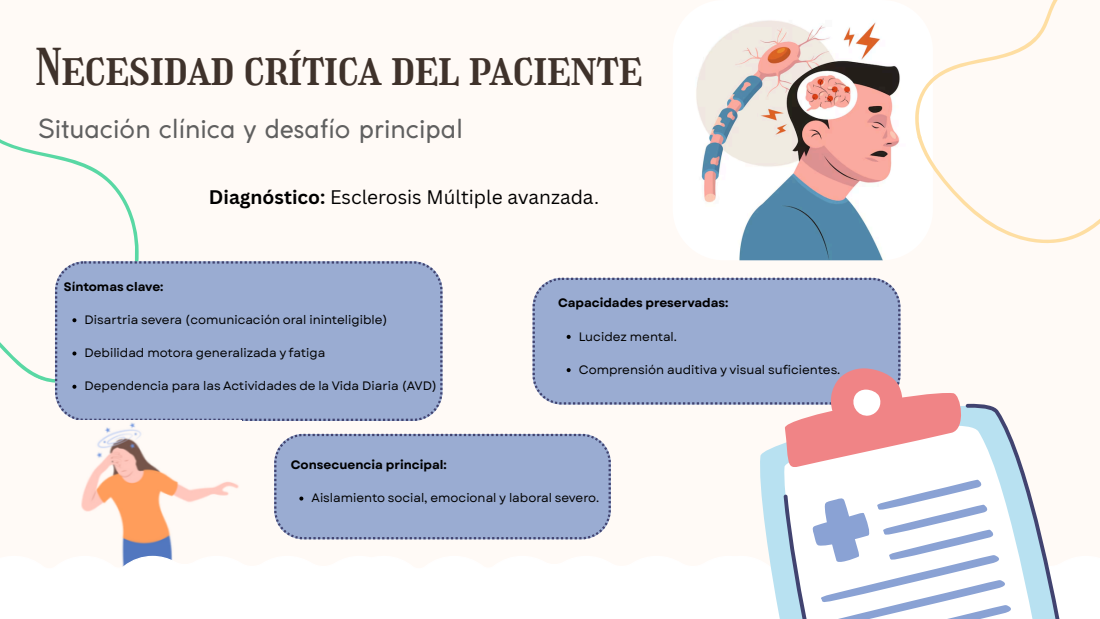
[picture p226: page 3]
Capacidades preservadas:; Lucidez mental.; Consecuencia principal:

Diagnóstico: Esclerosis Múltiple avanzada.

Síntomas clave: Disartria severa (comunicación oral ininteligible) Debilidad motora generalizada y fatiga Dependencia para las Actividades de la Vida Diaria (AVD)

Comprensión auditiva y visual suficientes.

Aislamiento social, emocional y laboral severo.

# Requisitos Prioritarios del Sistema

## Características Esenciales para la Solución

Expresión fluida | Mínimo esfuerzo de uso

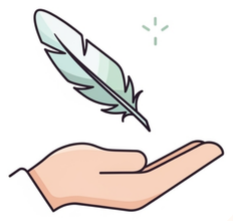
[picture p227: figure]
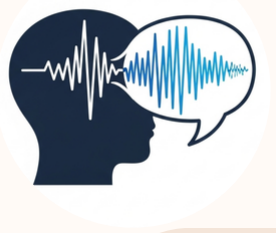
[picture p228: figure]

Entradas alternativas | Soporte integral
Capacidad para mensajes complejos, no solo frases básicas. | Bajo requerimiento físico y cognitivo. Accesible con motricidad manual limitada.

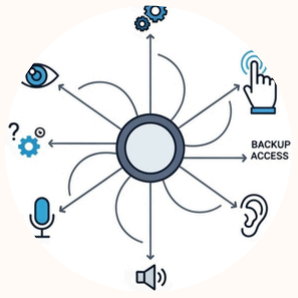
[picture p229: figure]
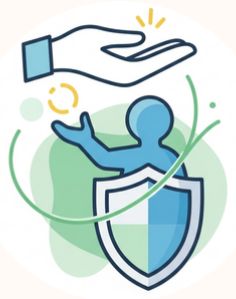
[picture p230: figure]

Múltiples canales de acceso (ej., seguimiento ocular). Backup para cuando falle el canal primario.

Integración de funciones de apoyo postural.
Prevención de complicaciones secundarias (úlceras por
presión)

# JUSTIFICACIÓN Y RAZONES DE PRIORIDAD

## Impacto de una solución efectiva

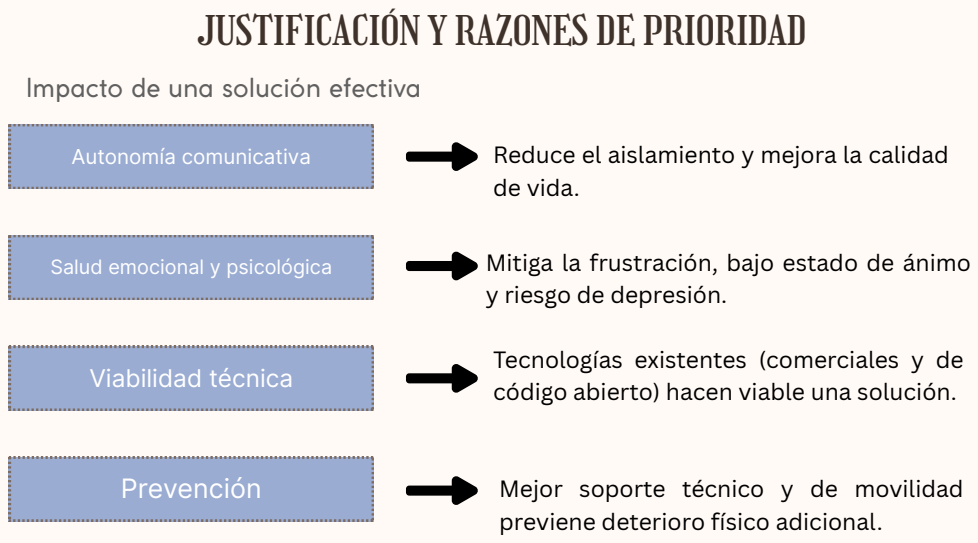
[picture p231: page 5]
Autonomía comunicativa; Viabilidad técnica; Prevención

Reduce el aislamiento y mejora la calidad
de vida.

Mitiga la frustración, bajo estado de ánimo
y riesgo de depresión.

Salud emocional y psicológica

Tecnologías existentes (comerciales y de
código abierto) hacen viable una solución.

Mejor soporte técnico y de movilidad
previene deterioro físico adicional.

2

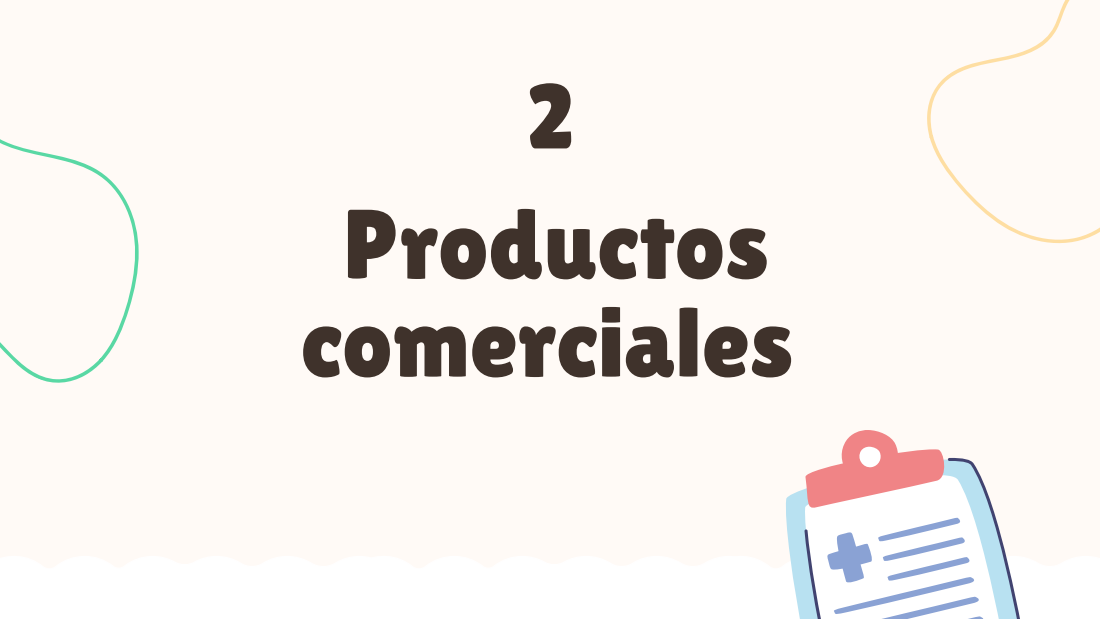
[picture p232: page 6]
Productos comerciales

## TD I-Series – Tobii Dynavox

# Productos comerciales

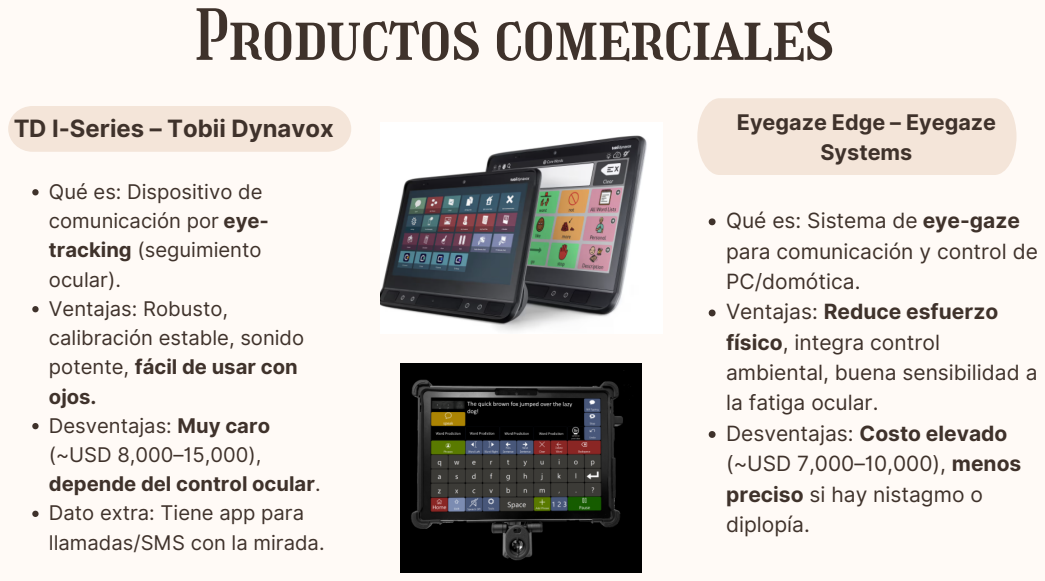
[picture p233: page 7]
Systems

Eyegaze Edge – Eyegaze

Qué es: Dispositivo de
comunicación por eye-
tracking (seguimiento
ocular).
Ventajas: Robusto,
calibración estable, sonido
potente, fácil de usar con
ojos.
Desventajas: Muy caro
(~USD 8,000–15,000),
depende del control ocular.
Dato extra: Tiene app para
llamadas/SMS con la mirada.

Qué es: Sistema de eye-gaze
para comunicación y control de
PC/domótica.
Ventajas: Reduce esfuerzo
físico, integra control
ambiental, buena sensibilidad a
la fatiga ocular.
Desventajas: Costo elevado
(~USD 7,000–10,000), menos
preciso si hay nistagmo o
diplopía.

# Productos comerciales

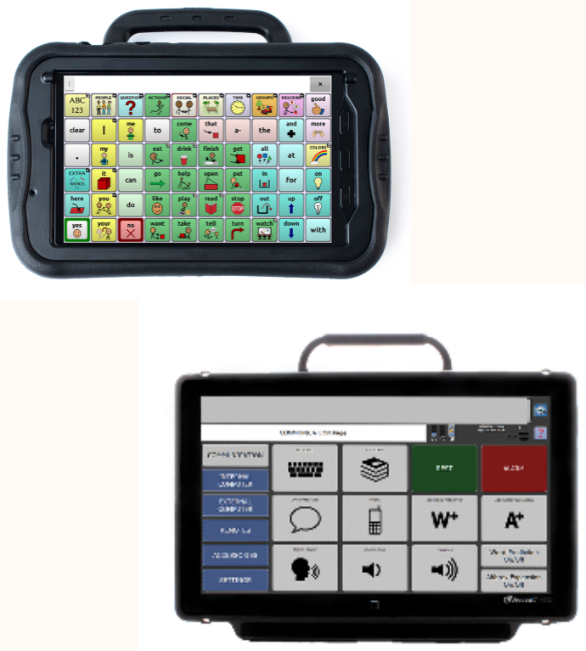
[picture p234: figure]

## Qué es: Dispositivos y apps de

comunicación aumentativa (AAC).

## Ventajas: Personalizable, varios

métodos de acceso (toque, switch,

## eye-tracker), opciones más económicas (apps desde USD 300– 400; dispositivos dedicados >USD

2,000).
Desventajas: Sin eye-tracker,

## pacientes con poca fuerza manual tienen dificultades; requiere accesorios

extra.

# NovaChat / TouchChat – PRC-Saltillo

# Sillas de ruedas eléctricas avanzadas Permobil

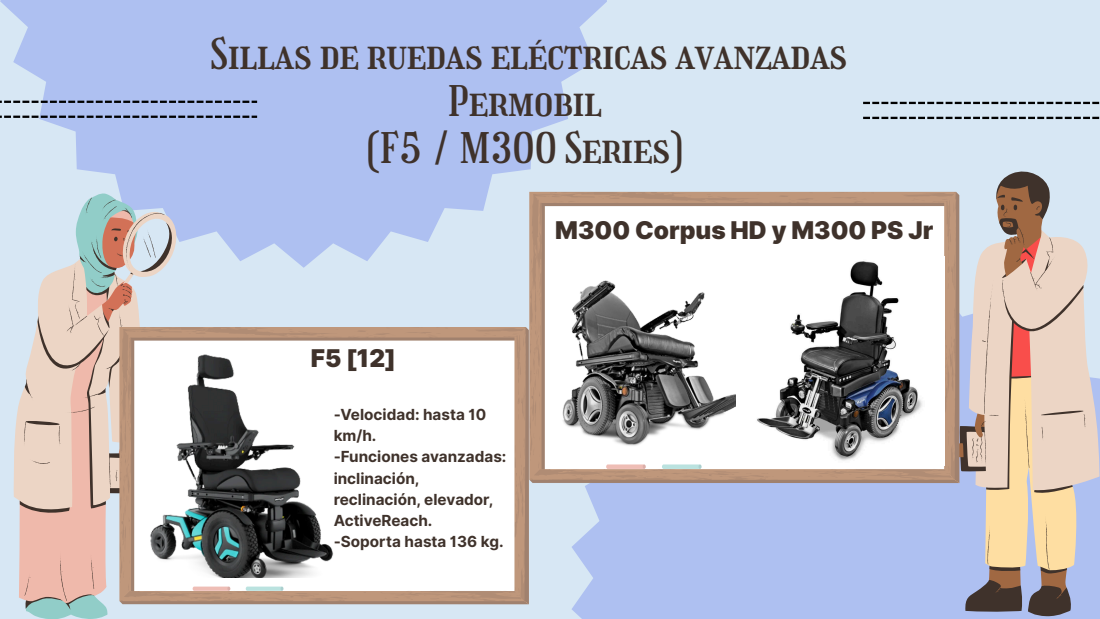
[picture p235: page 9]
(F5 / M300 Series)

M300 Corpus HD y M300 PS Jr

-Velocidad: hasta 10
-Funciones avanzadas:
inclinación,
reclinación, elevador,
ActiveReach.
-Soporta hasta 136 kg.

# Ventajas y Desventajas

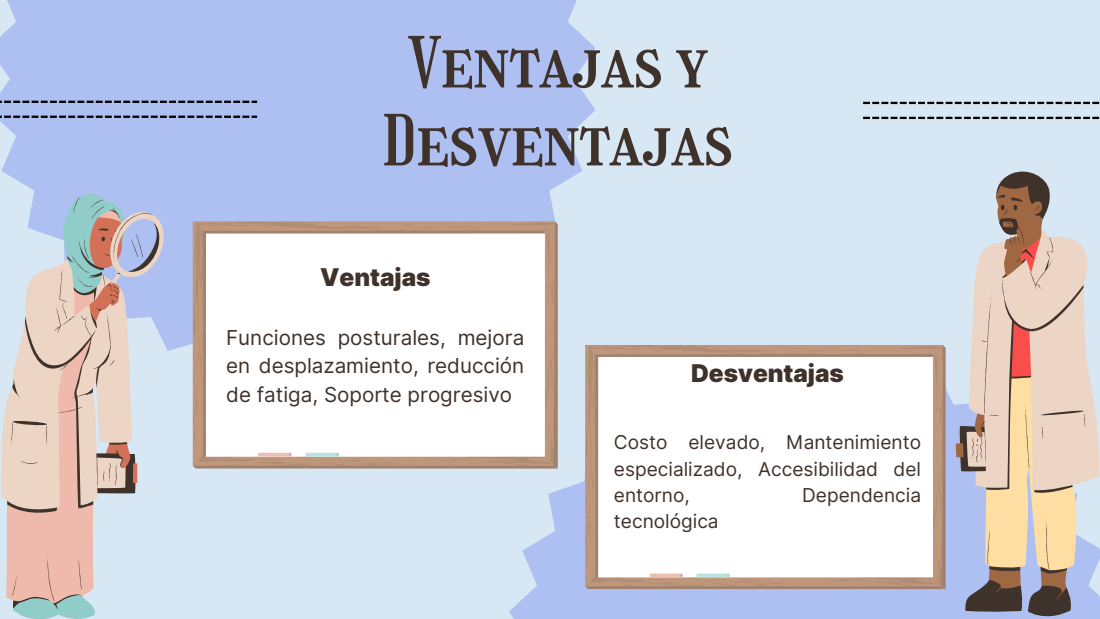
[picture p236: page 10]
Ventajas; entorno,; Dependencia; Desventajas

Funciones posturales, mejora
en desplazamiento, reducción
de fatiga, Soporte progresivo

Costo elevado, Mantenimiento
especializado, Accesibilidad del
tecnológica

# Prevención de úlceras por presión ROHO (cojín de celdas de aire)

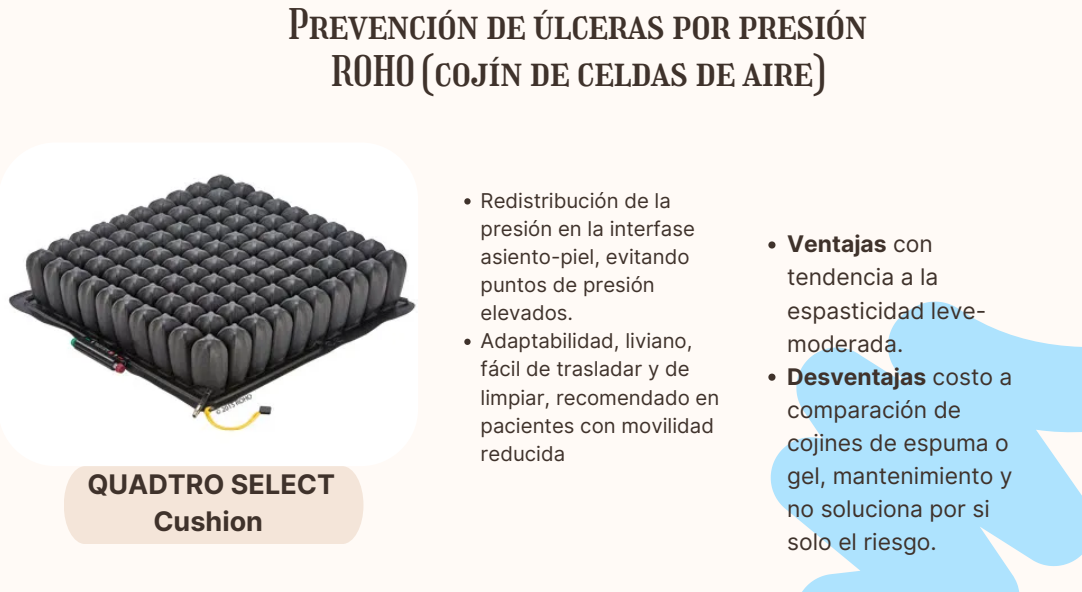
[picture p237: page 11]
QUADTRO SELECT Cushion

Redistribución de la
presión en la interfase
asiento-piel, evitando
puntos de presión
elevados.
Adaptabilidad, liviano,
fácil de trasladar y de
limpiar, recomendado en
pacientes con movilidad
reducida

Ventajas con
tendencia a la
espasticidad leve-
moderada.
Desventajas costo a
comparación de
cojines de espuma o
gel, mantenimiento y
no soluciona por si
solo el riesgo.

2

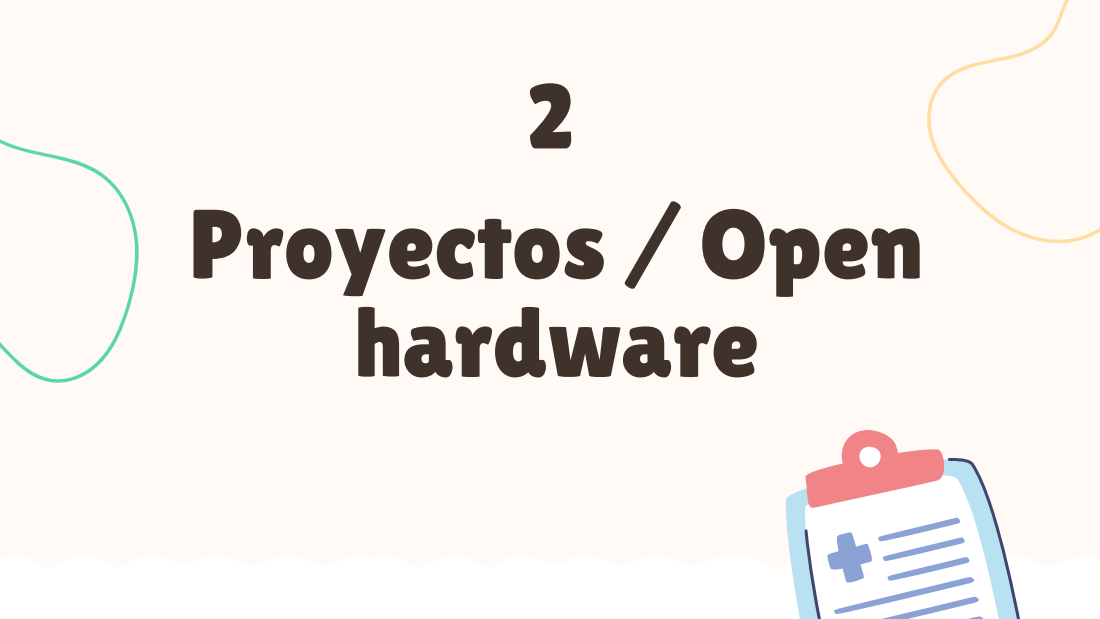
[picture p238: page 12]
Proyectos / Open hardware

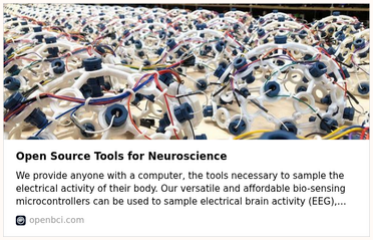
[picture p239: figure]

Descrpción: Placas y software open-source para registrar EEG/EMG/EKG y prototipar interfaces BCI no invasivas; ampliamente usada en investigación y por makers

Ventajas: Bajo coste relativo frente a equipos clínicos; alto grado de personalización e integración con software libre; comunidad activa (útil para prototipos experimentales).

Desventajas: No es un dispositivo médico certificado para uso clínico sin validación; calidad de señal inferior a equipos médicos de alto costo; requiere conocimientos técnicos para procesamiento de señales y seguridad.

# OpenBCI — Plataforma BCI open-hardware

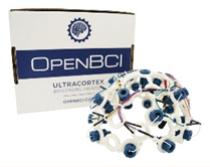
[picture p240: figure]

Ultracortex "Mark IV" EEG
Headset

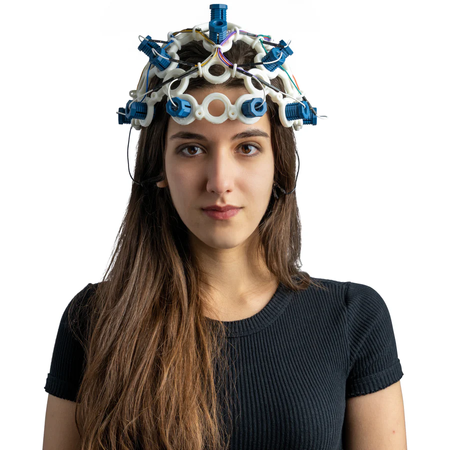
[picture p241: figure]
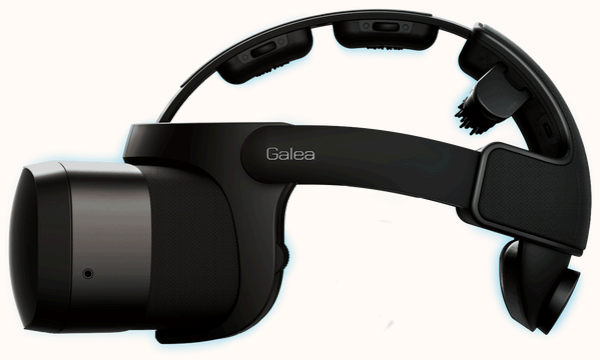
[picture p242: figure]

“Para el paciente con disartria severa, una BCI no invasiva (EEG) podría servir como canal alternativo de entrada si la oculomotricidad se deteriora, pero necesitaría validación de usabilidad y robustez clínica”

Nuestra misión
OpenBCI crea herramientas de
código | | abierto | para
biodetección y neurociencia. La misión de OpenBCI es reducir la barrera de entrada para la interfaz cerebro-computadora, al tiempo que garantiza que estas tecnologías se adopten en el panorama del consumidor de una manera ética que
proteja | la | autonomía | del
usuario y la salud mental.

El último proyecto de
OpenBCI
Galea es una plataforma de hardware y software que
fusiona la biometría de
próxima generación con la
realidad mixta. Galea es el primer dispositivo que integra EEG, EMG, EDA, PPG y
seguimiento ocular en un solo auricular.

# EyeWriter — open eye-tracking low-cost

## REPOSITORIO DE EYEWRITER

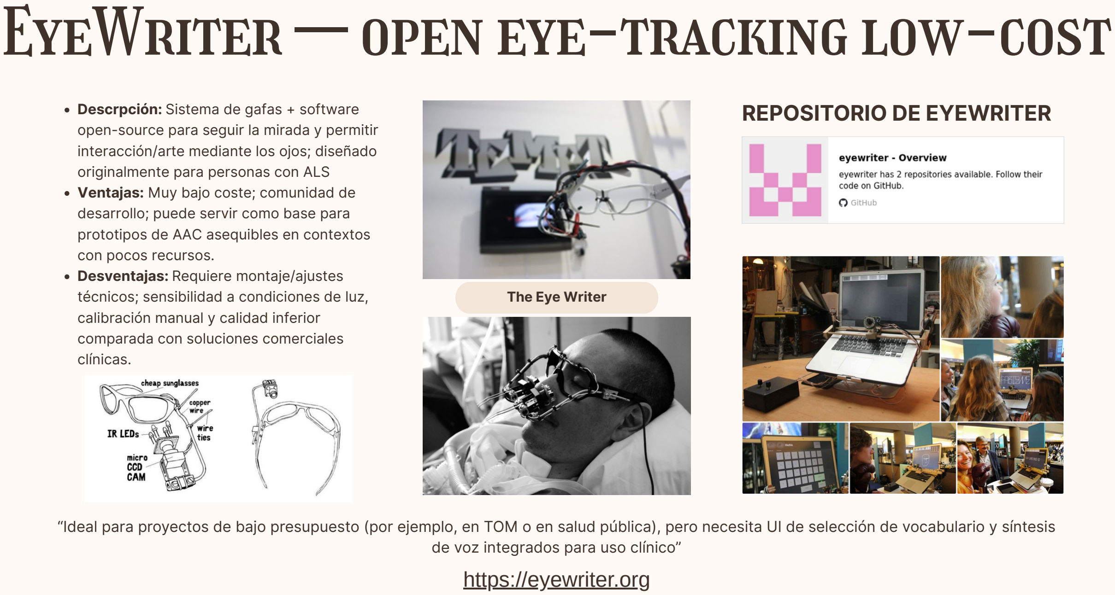
[picture p243: page 14]

Descrpción: Sistema de gafas + software open-source para seguir la mirada y permitir interacción/arte mediante los ojos; diseñado originalmente para personas con ALS Ventajas: Muy bajo coste; comunidad de desarrollo; puede servir como base para prototipos de AAC asequibles en contextos con pocos recursos.
Desventajas: Requiere montaje/ajustes técnicos; sensibilidad a condiciones de luz, calibración manual y calidad inferior comparada con soluciones comerciales clínicas.

The Eye Writer

“Ideal para proyectos de bajo presupuesto (por ejemplo, en TOM o en salud pública), pero necesita UI de selección de vocabulario y síntesis de voz integrados para uso clínico”

## https://eyewriter.org

4

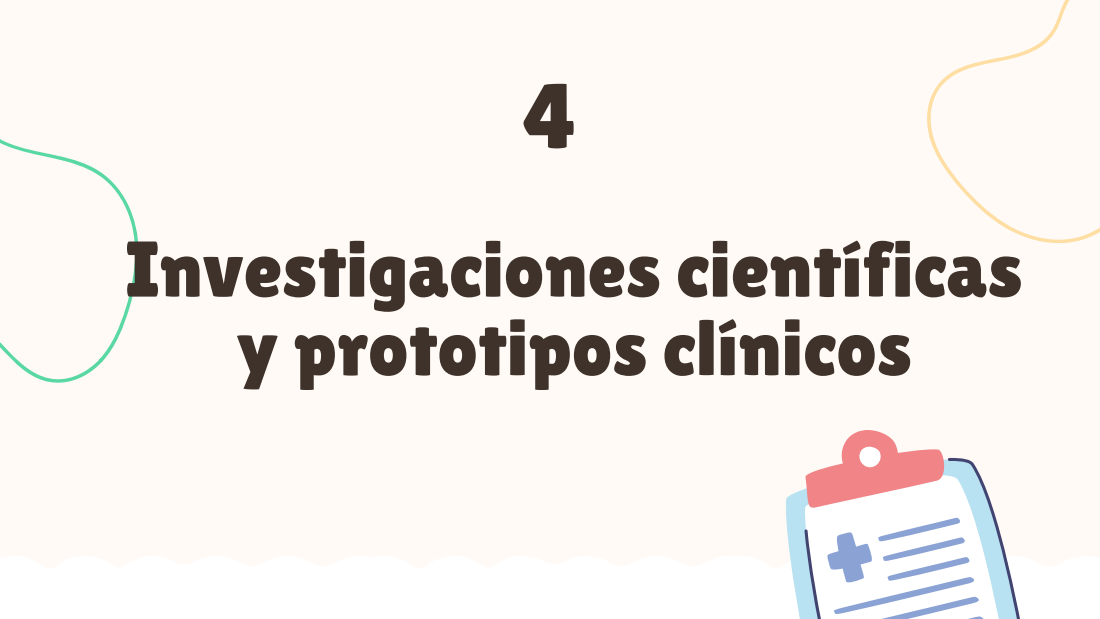
[picture p244: page 15]
Investigaciones científicas y prototipos clínicos

# c-VEP BCI para comunicación

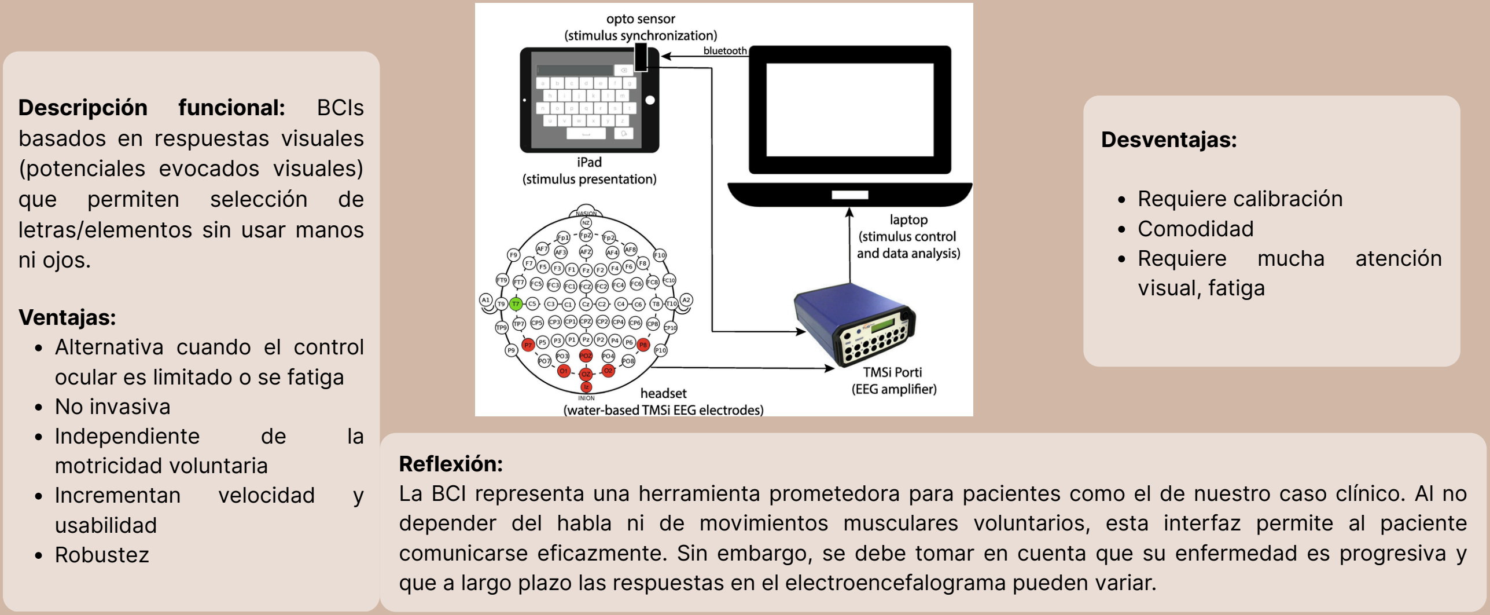
[picture p245: figure]
Descripción funcional: BCIs basados en respuestas visuales (potenciales evocados visuales) que permiten selección de letras/elementos sin usar manos ni ojos.; Ventajas: Alternativa cuando el control ocular es limitado o se fatiga No invasiva; Independiente; motricidad voluntaria; Incrementan; velocidad; usabilidad Robustez; Desventajas:; Requiere calibración Comodidad Requiere mucha atención visual, fatiga; Reflexión:

S. Ghosh et al.,

“A visual brain-computer interface as communication aid for patients with amyotrophic lateral sclerosis” Journal of the Neurological” Sciences, vol. 430, 2021. [Online]. Available: https://www.sciencedirect.com/science/article/pii/S1388245721006635

La BCI representa una herramienta prometedora para pacientes como el de nuestro caso clínico. Al no depender del habla ni de movimientos musculares voluntarios, esta interfaz permite al paciente comunicarse eficazmente. Sin embargo, se debe tomar en cuenta que su enfermedad es progresiva y que a largo plazo las respuestas en el electroencefalograma pueden variar.

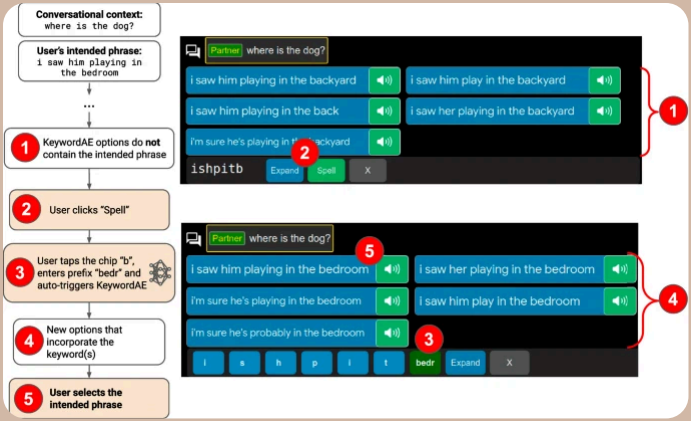
[picture p246: figure]

El LLM-assisted AAC es una herramienta que combina modelos de lenguaje con sistemas de comunicación aumentativa, diseñada para apoyar a personas con esclerosis múltiple avanzada que mantienen sus capacidades cognitivas, pero presentan disartria severa. Esta tecnología facilita la expresión de ideas de manera más fluida y natural, disminuye el esfuerzo necesario para comunicarse y mejora la interacción social y la autonomía del paciente.

# LLM-assisted AAC (LLMs para acelerar entrada en eye-gaze)

S. Cai et al., «Using large language models to accelerate communication for eye gaze typing users with ALS», Nature Communications, vol. 15, n.o 1, nov. 2024, doi: 10.1038/s41467-024-53873-3.

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
S. C

ai e

t

al.,

«

U

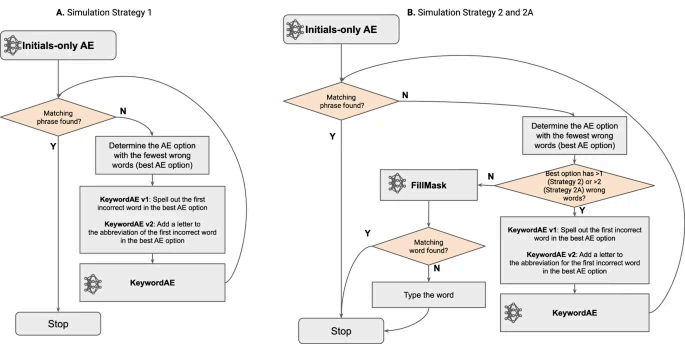
[picture p247: figure]

sin

g la

r

g

e la

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
ol. 1

5

,
n.o

1

,

n

o

v. 2

0

2

4

,

d

oi: 1

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
# LLM-assisted AAC (LLMs para acelerar entrada en eye-gaze)

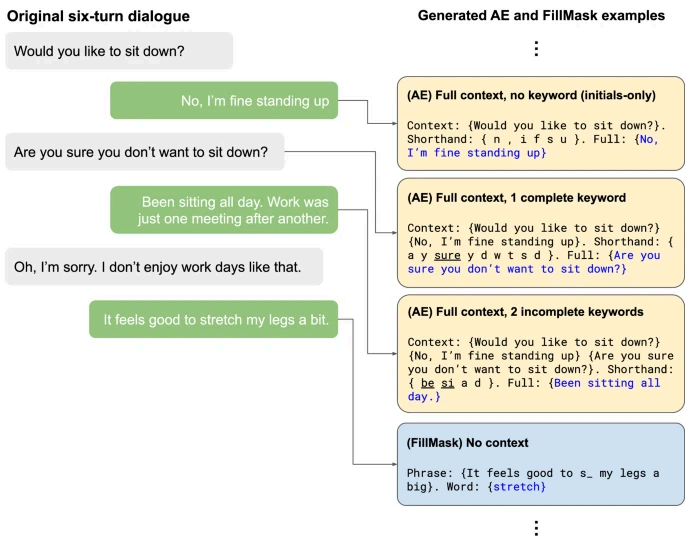
[picture p248: figure]
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

5

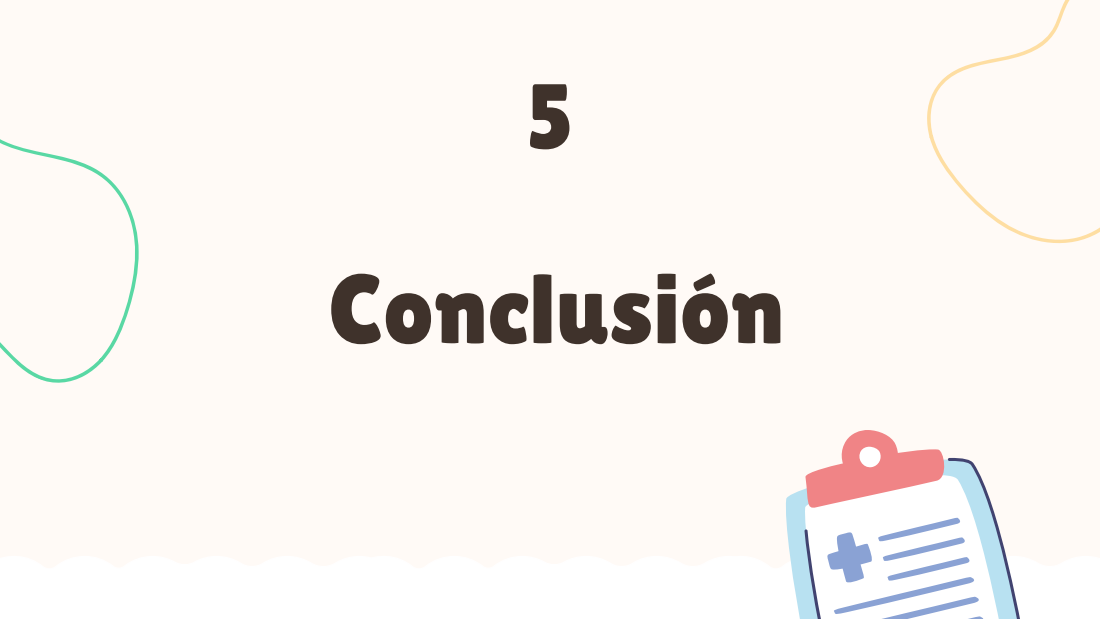
[picture p249: page 20]
Conclusión

# PROPUESTAS DE MEJORA PARA UN NUEVO PROTOTIPO

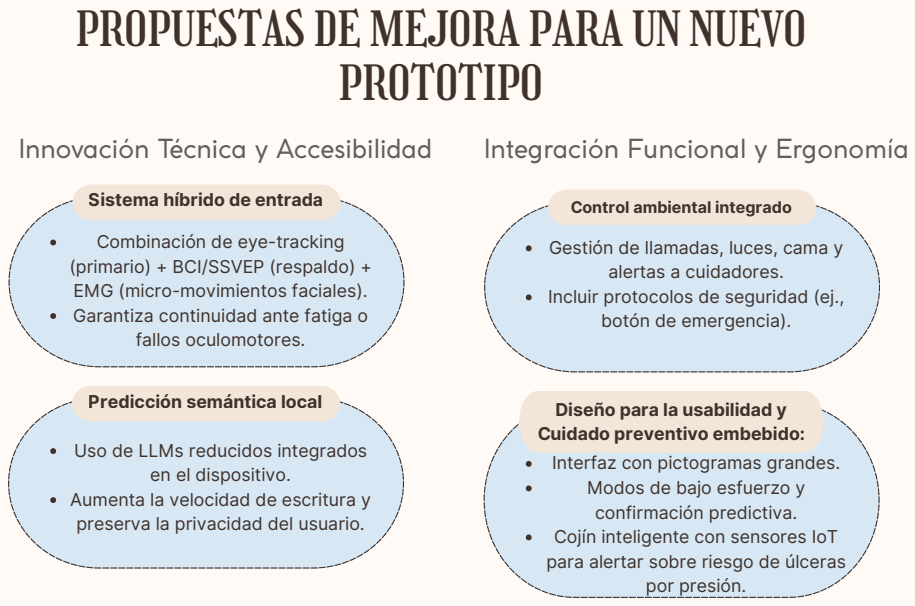
[picture p250: page 21]
por presión.

Innovación Técnica y Accesibilidad

Integración Funcional y Ergonomía

Sistema híbrido de entrada

Control ambiental integrado
Gestión de llamadas, luces, cama y
alertas a cuidadores.
Incluir protocolos de seguridad (ej.,
botón de emergencia).

Combinación de eye-tracking
(primario) + BCI/SSVEP (respaldo) +
EMG (micro-movimientos faciales).
Garantiza continuidad ante fatiga o
fallos oculomotores.

Predicción semántica local

Diseño para la usabilidad y
Cuidado preventivo embebido:
Interfaz con pictogramas grandes.
Modos de bajo esfuerzo y
confirmación predictiva.
Cojín inteligente con sensores IoT
para alertar sobre riesgo de úlceras

Uso de LLMs reducidos integrados

en el dispositivo.

Aumenta la velocidad de escritura y
preserva la privacidad del usuario.

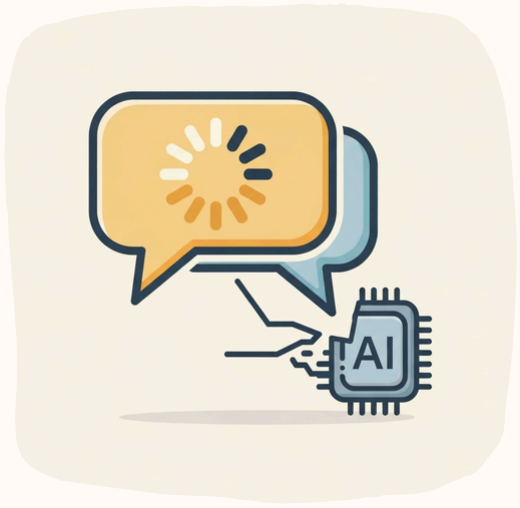
[picture p251: figure]

Velocidad comunicativa:

Las soluciones actuales son lentas para conversaciones complejas.

Integración de LLMs contextuales no es estándar.

Falta de continuidad robusta:

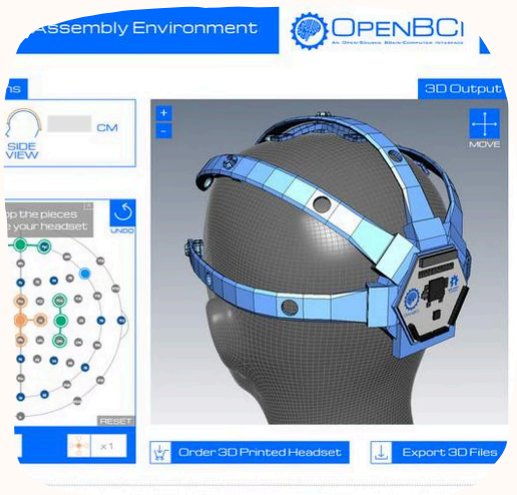
[picture p252: figure]

Carencia de sistemas híbridos comerciales (gaze + BCI) validados para cuando falla el control ocular.

Accesibilidad económica:

Proyectos de open-hardware (EyeWriter, OpenBCI) carecen de empaquetado clínico y soporte para uso domiciliario prolongado.

# Necesidades insatisfechas actualmente

## Brechas en las soluciones existentes
